AhmedMKAlzoubi/Digital-B-Card/datasheets/all_datasheets_combined.md

# Digital Business Card — All Datasheets (Combined)

*Single merged reference: system datasheets (MCU, display) + all BOM part datasheets.
Merged 2026-08-01 from `datasheets_combined.md` and `part_datasheets_combined.md`, with J2 (C295747) added as §15 of Part II.*

---

# PART I — SYSTEM DATASHEETS

# Datasheets — Combined Reference

_Compiled 2026-07-31 from 4 source PDFs. Full-text extraction; the Good Display module was OCR-processed as it is image-based, so minor OCR artifacts may be present._

## Contents

1. [ESP32-C3-MINI-1 Datasheet](#1-esp32-c3-mini-1-datasheet) — Espressif Systems — ESP32-C3-MINI-1 / MINI-1U Wi-Fi + Bluetooth LE MCU module
2. [ESP32-C3 Hardware Design Guidelines](#2-esp32-c3-hardware-design-guidelines) — Espressif Systems — ESP32-C3 series hardware design guidelines
3. [SSD1680 Datasheet](#3-ssd1680-datasheet) — Solomon Systech — SSD1680 active matrix EPD display driver / controller
4. [GDEM0266T71WT Datasheet](#4-gdem0266t71wt-datasheet) — Good Display — GDEM0266T71WT 2.66" e-paper display module (OCR-extracted)

---

# 1. ESP32-C3-MINI-1 Datasheet

> **Source file:** `esp32-c3-mini-1_datasheet_en.pdf`  
> Espressif Systems — ESP32-C3-MINI-1 / MINI-1U Wi-Fi + Bluetooth LE MCU module

<!-- Page 1 -->

ESP32-C3-MINI-1
ESP32-C3-MINI-1U
Datasheet Version 2.2
Small-sized 2.4 GHz Wi-Fi (802.11b/g/n) and Bluetooth® 5 module
Built around ESP32-C3 series of SoCs, RISC-V single-core microprocessor
Up to 8 MB flash in chip package
15 GPIOs
On-board PCB antenna or external antenna connector
ESP32-C3-MINI-1
ESP32-C3-MINI-1U
www.espressif.com

<!-- Page 2 -->

1
Module Overview
1
Module Overview
Note:
Check the link or the QR code to make sure that you use the latest version of this document:
https://www.espressif.com/documentation/esp32-c3-mini-1_datasheet_en.pdf
1.1
Features
CPU and On-Chip Memory
• ESP32-C3FH4, ESP32-C3FH4X,
ESP32-C3FH8X, or ESP32-C3FH4AZ
embedded, 32-bit RISC-V single-core
processor, up to 160 MHz
• 384 KB ROM
• 400 KB SRAM (16 KB for cache)
• 8 KB SRAM in RTC
• Up to 8 MB flash in chip package
Wi-Fi
• IEEE 802.11 b/g/n-compliant
• Center frequency range of operating channel:
2412 ~ 2484 MHz
• Supports 20 MHz, 40 MHz bandwidth in 2.4
GHz band
• 1T1R mode with data rate up to 150 Mbps
• Wi-Fi Multimedia (WMM)
• TX/RX A-MPDU, TX/RX A-MSDU
• Immediate Block ACK
• Fragmentation and defragmentation
• Transmit opportunity (TXOP)
• Automatic Beacon monitoring (hardware TSF)
• 4 × virtual Wi-Fi interfaces
• Simultaneous support for Infrastructure BSS in
Station mode, SoftAP mode, Station + SoftAP
mode, and promiscuous mode
Note that when the chip scans in Station mode,
the SoftAP channel will change along with the
Station channel
• 802.11mc FTM
Bluetooth®
• Bluetooth LE: Bluetooth 5, Bluetooth mesh
• Speed: 125 Kbps, 500 Kbps, 1 Mbps, 2 Mbps
• Advertising extensions
• Multiple advertisement sets
• Channel selection algorithm #2
• Internal co-existence mechanism between Wi-Fi
and Bluetooth to share the same antenna
Peripherals
• Up to 15 GPIOs
– 3 strapping GPIOs
• SPI, UART, I2C, I2S, remote control peripheral,
LED PWM controller, general DMA controller,
TWAI® controller (compatible with ISO 11898-1,
i.e. CAN Specification 2.0), USB Serial/JTAG
controller, temperature sensor, SAR ADC,
general-purpose timers, watchdog timers
Note:
* Please refer to ESP32-C3 Series Datasheet for
detailed information about the module peripher-
als.
Integrated Components on Module
• 40 MHz crystal oscillator
Espressif Systems
2
Submit Documentation Feedback
ESP32-C3-MINI-1 & MINI-1U Datasheet v2.2

<!-- Page 3 -->

1
Module Overview
Antenna Options
• ESP32-C3-MINI-1: On-board PCB antenna
• ESP32-C3-MINI-1U: External antenna via a
connector
Operating Conditions
• Operating voltage/Power supply: 3.0 ~ 3.6 V
• Operating ambient temperature:
– 85 °C version module: –40 ~ 85 °C
– 105 °C version module: –40 ~ 105 °C
Certification
• RF certification: See certificates
• Green certification: RoHS/REACH
Test
• HTOL/HTSL/uHAST/TCT/ESD/Latch-up
1.2
Series Comparison
ESP32-C3-MINI-1 and ESP32-C3-MINI-1U are two general-purpose Wi-Fi and Bluetooth LE modules. The rich
set of peripherals and a small size make the two modules an ideal choice for smart homes, industrial
automation, health care, consumer electronics, etc.
ESP32-C3-MINI-1 comes with a PCB antenna. ESP32-C3-MINI-1U comes with an external antenna connector.
A wide selection of module variants are available as shown in Table 1-1 and 1-2.
The series comparison for the two modules is as follows:
Table 1-1. ESP32-C3-MINI-1 (ANT) Series Comparison1
Ambient Temp.2
Embedded
Size3
Part Number5
Flash4
(°C)
Chip Revision6
(mm)
ESP32-C3-MINI-1-N4X
(Recommended)
4 MB (Quad SPI)
–40 ∼85
v1.1
13.2 × 16.6 × 2.4
ESP32-C3-MINI-1-H4X
(Recommended)
–40 ∼105
v1.1
ESP32-C3-MINI-1-H8X
8 MB (Quad SPI)
–40 ∼105
v1.1
ESP32-C3-MINI-1-N4 (NRND)
4 MB (Quad SPI)
–40 ∼85
v0.4
ESP32-C3-MINI-1-H4 (NRND)
–40 ∼105
v0.4
ESP32-C3-MINI-1-H4-AZ (NRND)
–40 ∼105
v0.4
1 This table shares the same notes presented in Table 1-2 below.
Espressif Systems
3
Submit Documentation Feedback
ESP32-C3-MINI-1 & MINI-1U Datasheet v2.2

<!-- Page 4 -->

1
Module Overview
Table 1-2. ESP32-C3-MINI-1U (CONN) Series Comparison
Ambient Temp.2
Embedded
Size3
Part Number5
Flash4, 7
(°C)
Chip Revision 6
(mm)
ESP32-C3-MINI-1U-N4X
(Recommended)
4 MB (Quad SPI)
–40 ∼85
v1.1
13.2 × 12.5 × 2.4
ESP32-C3-MINI-1U-H4X
(Recommended)
–40 ∼105
v1.1
ESP32-C3-MINI-1U-N4 (NRND)
–40 ∼85
v0.4
ESP32-C3-MINI-1U-H4 (NRND)
–40 ∼105
v0.4
2 Ambient temperature specifies the recommended temperature range of the environment immediately outside the
Espressif module.
3 For details, refer to Section 10.1 Module Dimensions.
4 The flash is integrated in the chip’s package. For specifications, refer to Section 6.5 Memory Specifications.
5 All modules can be pre-programmed with AWS IoT ExpressLink firmware. Modules with such firmware have suffix ”-A”
in their part numbers, e.g. ESP32-C3-MINI-1-N4-A. Since AWS IoT ExpressLink firmware enables flash encryption
and secure boot, joint download boot mode will be disabled, and it will no longer be possible to program firmware
through the UART or USB port into the modules.
6 All chip revisions have the same SRAM size, but chip revision v1.1 has around 10 KB more available space for users
than chip revision v0.4. Chip revision v1.1 depends on specific ESP-IDF versions, as detailed in Compatibility Advisory
for ESP32-C3 Chip Revision v1.1. For how to identify chip revisions, please refer to ESP32-C3 Series SoC Errata.
7 By default, the SPI flash on the module operates at a maximum clock frequency of 80 MHz and does not support
the auto suspend feature. If you have a requirement for a higher flash clock frequency of 120 MHz or if you need
the flash auto suspend feature, please contact us.
Both ESP32-C3-MINI-1 and ESP32-C3-MINI-1U has two operating ambient temperature options: –40 ∼85 °C
variants and –40 ∼105 °C variants. These modules can be embedded with the following chips:
• ESP32-C3FH4: chip revision v0.4, 4 MB flash
• ESP32-C3FH4X: chip revision v1.1, 4 MB flash
• ESP32-C3FH8X: chip reivision v1.1, 8 MB
ESP32-C3-MINI-1 has one more variant: ESP32-C3-MINI-1-H4-AZ embedded with the ESP32-C3FH4AZ chip.
For this chip, SPI0/SPI1 pins for flash connection are not bonded.
For more information about the differences between chips embedded, please refer to Section Chip Series
Comparison in ESP32-C3 Series Datasheet.
1.3
Applications
• Smart Home
• Industrial Automation
• Health Care
• Consumer Electronics
• Smart Agriculture
• POS Machines
• Service Robot
• Audio Devices
• Generic Low-power IoT Sensor Hubs
• Generic Low-power IoT Data Loggers
Espressif Systems
4
Submit Documentation Feedback
ESP32-C3-MINI-1 & MINI-1U Datasheet v2.2

<!-- Page 5 -->

Contents
Contents
1
Module Overview
2
1.1
Features
2
1.2
Series Comparison
3
1.3
Applications
4
2
Block Diagram
9
3
Pin Definitions
10
3.1
Pin Layout
10
3.2
Pin Description
10
4
Boot Configurations
12
4.1
Chip Boot Mode Control
13
4.2
ROM Messages Printing Control
14
4.3
Chip Power-up and Reset
14
5
Peripherals
16
5.1
Peripheral Overview
16
5.2
Peripheral Description
16
5.2.1
Connectivity Interface
16
5.2.1.1
UART Controller
16
5.2.1.2
SPI Controller
16
5.2.1.3
I2C Controller
17
5.2.1.4
I2S Controller
18
5.2.1.5
USB Serial/JTAG Controller
18
5.2.1.6
Two-wire Automotive Interface
18
5.2.1.7
LED PWM Controller
19
5.2.1.8
Remote Control Peripheral
19
5.2.2
Analog Signal Processing
19
5.2.2.1
SAR ADC
20
5.2.2.2
Temperature Sensor
20
6
Electrical Characteristics
21
6.1
Absolute Maximum Ratings
21
6.2
Recommended Operating Conditions
21
6.3
DC Characteristics (3.3 V, 25 °C)
21
6.4
Current Consumption Characteristics
22
6.4.1
Current Consumption in Active Mode
22
6.4.2
Current Consumption in Other Modes
23
6.5
Memory Specifications
23
7
RF Characteristics
25
7.1
Wi-Fi Radio
25
Espressif Systems
5
Submit Documentation Feedback
ESP32-C3-MINI-1 & MINI-1U Datasheet v2.2

<!-- Page 6 -->

Contents
7.1.1
Wi-Fi RF Transmitter (TX) Characteristics
25
7.1.2
Wi-Fi RF Receiver (RX) Characteristics
26
7.2
Bluetooth 5 (LE) Radio
27
7.2.1
Bluetooth LE RF Transmitter (TX) Characteristics
27
7.2.2
Bluetooth LE RF Receiver (RX) Characteristics
29
8
Module Schematics
32
9
Peripheral Schematics
34
10 Physical Dimensions
35
10.1
Module Dimensions
35
10.2
Dimensions of External Antenna Connector
36
11
PCB Layout Recommendations
38
11.1
PCB Land Pattern
38
11.2
Module Placement for PCB Design
39
12 Product Handling
40
12.1
Storage Conditions
40
12.2
Electrostatic Discharge (ESD)
40
12.3
Reflow Profile
40
12.4
Ultrasonic Vibration
41
Datasheet Versioning
42
Related Documentation and Resources
43
Revision History
45
Espressif Systems
6
Submit Documentation Feedback
ESP32-C3-MINI-1 & MINI-1U Datasheet v2.2

<!-- Page 7 -->

List of Tables
List of Tables
1-1
ESP32-C3-MINI-1 (ANT) Series Comparison1
3
1-2
ESP32-C3-MINI-1U (CONN) Series Comparison
4
3-1
Pin Definitions
11
4-1
Default Configuration of Strapping Pins
12
4-2
Description of Timing Parameters for the Strapping Pins
13
4-3
Chip Boot Mode Control
13
4-4
UART0 ROM Message Printing Control
14
4-5
USB Serial/JTAG ROM Message Printing Control
14
4-6 Description of Timing Parameters for Power-up and Reset
15
6-1
Absolute Maximum Ratings
21
6-2 Recommended Operating Conditions
21
6-3 DC Characteristics (3.3 V, 25 °C)
21
6-4 Current Consumption for Wi-Fi (2.4 GHz) in Active Mode
22
6-5 Current Consumption for Bluetooth LE in Active Mode
22
6-6 Current Consumption in Modem-sleep Mode
23
6-7
Current Consumption in Low-Power Modes
23
6-8 Flash Specifications
23
7-1
Wi-Fi RF Characteristics
25
7-2
TX Power with Spectral Mask and EVM Meeting 802.11 Standards
25
7-3
TX EVM Test1
25
7-4
RX Sensitivity
26
7-5
Maximum RX Level
27
7-6
RX Adjacent Channel Rejection
27
7-7
Bluetooth LE RF Characteristics
27
7-8
Bluetooth LE - Transmitter Characteristics - 1 Mbps
28
7-9
Bluetooth LE - Transmitter Characteristics - 2 Mbps
28
7-10 Bluetooth LE - Transmitter Characteristics - 125 Kbps
28
7-11
Bluetooth LE - Transmitter Characteristics - 500 Kbps
29
7-12 Bluetooth LE - Receiver Characteristics - 1 Mbps
29
7-13 Bluetooth LE - Receiver Characteristics - 2 Mbps
30
7-14 Bluetooth LE - Receiver Characteristics - 125 Kbps
30
7-15 Bluetooth LE - Receiver Characteristics - 500 Kbps
31
Espressif Systems
7
Submit Documentation Feedback
ESP32-C3-MINI-1 & MINI-1U Datasheet v2.2

<!-- Page 8 -->

List of Figures
List of Figures
2-1
ESP32-C3-MINI-1 Block Diagram
9
2-2 ESP32-C3-MINI-1U Block Diagram
9
3-1
Pin Layout (Top View)
10
4-1
Visualization of Timing Parameters for the Strapping Pins
13
4-2
Visualization of Timing Parameters for Power-up and Reset
15
8-1
ESP32-C3-MINI-1 Schematics
32
8-2
ESP32-C3-MINI-1U Schematics
33
9-1
Peripheral Schematics
34
10-1 ESP32-C3-MINI-1 Physical Dimensions
35
10-2 ESP32-C3-MINI-1U Physical Dimensions
35
10-3 Dimensions of External Antenna Connector
36
11-1
ESP32-C3-MINI-1 Recommended PCB Land Pattern
38
11-2 ESP32-C3-MINI-1U Recommended PCB Land Pattern
39
12-1 Reflow Profile
40
Espressif Systems
8
Submit Documentation Feedback
ESP32-C3-MINI-1 & MINI-1U Datasheet v2.2

<!-- Page 9 -->

2
Block Diagram
2
Block Diagram
SPI Flash
RF Matching
40 MHz
Crystal
3V3
ESP32-C3-MINI-1
EN
GPIOs
Antenna
ESP32-C3FH4
Figure 2-1. ESP32-C3-MINI-1 Block Diagram
SPI Flash
40 MHz
Crystal
3V3
ESP32-C3-MINI-1U
EN
GPIOs
ESP32-C3FH4
RF Matching
Antenna
Figure 2-2. ESP32-C3-MINI-1U Block Diagram
Note:
For the pin mapping between the chip and the in-package flash, please refer to ESP32-C3 Series Datasheet > Table
Pin Mapping Between Chip and In-package Flash.
Espressif Systems
9
Submit Documentation Feedback
ESP32-C3-MINI-1 & MINI-1U Datasheet v2.2

<!-- Page 10 -->

3
Pin Definitions
3
Pin Definitions
3.1
Pin Layout
The pin diagram below shows the approximate location of pins on the module. For the actual diagram drawn to
scale, please refer to Figure 10.1 Module Dimensions.
Pin 49
GND
GND
GND
GND
GND
GND
GND
GND
GND
Pin 1
Pin 2
Pin 3
Pin 4
Pin 6
Pin 5
Pin 7
Pin 8
Pin 9
Pin 10
Pin 11
Pin 53
GND
Pin 52
GND
Pin 12
Pin 13
Pin 14
Pin 15
Pin 16
Pin 17
Pin 18
Pin 19
Pin 20
Pin 21
Pin 22
Pin 23
Pin 24
Pin 25
Pin 51
GND
Pin 26
Pin 27
Pin 28
Pin 29
Pin 30
Pin 31
Pin 32
Pin 33
Pin 34
Pin 35
Pin 50
GND
Pin 36
Pin 37
Pin 38
Pin 39
Pin 40
Pin 41
Pin 42
Pin 43
Pin 44
Pin 45
Pin 46
Pin 47
Pin 48
GND
GND
3V3
NC
IO2
IO3
NC
EN
NC
NC
GND
IO0
IO1
GND
NC
IO10
NC
IO4
IO5
IO6
IO7
IO8
IO9
NC
NC
IO18
IO19
NC
NC
RXD0
TXD0
NC
NC
NC
NC
GND
GND
GND
GND
GND
GND
GND
GND
GND
GND
GND
GND
GND
Keepout Zone
A
Figure 3-1. Pin Layout (Top View)
Note A:
The zone marked with dotted lines is the antenna keepout zone. The pin diagram is applicable to ESP32-C3-MINI-1
and ESP32-C3-MINI-1U, but the latter has no antenna keepout zone.
To learn more about the keepout zone for module’s antenna on the base board, please refer to
ESP32-C3 Hardware Design Guidelines > Section General Principles of PCB Layout for Modules.
3.2
Pin Description
The module has 53 pins. See pin definitions in Table 3-1 Pin Definitions.
For peripheral pin configurations, please refer to Section 5.2 Peripheral Description.
Espressif Systems
10
Submit Documentation Feedback
ESP32-C3-MINI-1 & MINI-1U Datasheet v2.2

<!-- Page 11 -->

3
Pin Definitions
Table 3-1. Pin Definitions
Name
No.
Type1
Function
GND
1, 2, 11, 14,
36-53
P
Ground
3V3
3
P
Power supply
NC
4, 7, 9, 10,
15, 17, 24,
25, 28, 29,
32-35
—
NC
IO2
5
I/O/T
GPIO2, ADC1_CH2, FSPIQ
IO3
6
I/O/T
GPIO3, ADC1_CH3
EN
8
I
High: on, enables the chip.
Low: off, the chip powers off.
Note: Do not leave the EN pin floating.
IO0
12
I/O/T
GPIO0, ADC1_CH0, XTAL_32K_P
IO1
13
I/O/T
GPIO1, ADC1_CH1, XTAL_32K_N
IO10
16
I/O/T
GPIO10, FSPICS0
IO4
18
I/O/T
GPIO4, ADC1_CH4, FSPIHD, MTMS
IO5
19
I/O/T
GPIO5, ADC2_CH0, FSPIWP, MTDI
IO6
20
I/O/T
GPIO6, FSPICLK, MTCK
IO7
21
I/O/T
GPIO7, FSPID, MTDO
IO8
22
I/O/T
GPIO8
IO9
23
I/O/T
GPIO9
IO18
26
I/O/T
GPIO18, USB_D-
IO19
27
I/O/T
GPIO19, USB_D+
RXD0
30
I/O/T
GPIO20, U0RXD
TXD0
31
I/O/T
GPIO21, U0TXD
1 P: power supply; I: input; O: output; T: high impedance.
Espressif Systems
11
Submit Documentation Feedback
ESP32-C3-MINI-1 & MINI-1U Datasheet v2.2

<!-- Page 12 -->

4
Boot Configurations
4
Boot Configurations
Note:
The content below is excerpted from ESP32-C3 Series Datasheet > Chapter Boot Configurations. For the strapping
pin mapping between the chip and modules, please refer to Chapter 8 Module Schematics.
The chip allows for configuring the following boot parameters through strapping pins and eFuse parameters at
power-up or a hardware reset, without microcontroller interaction.
• Chip boot mode
– Strapping pins: GPIO2, GPIO8, and GPIO9
• ROM message printing
– Strapping pin: GPIO8
– eFuse parameters: EFUSE_UART_PRINT_CONTROL and EFUSE_USB_PRINT_CHANNEL
The default values of all the above eFuse parameters are 0, which means that they are not burnt. Given that
eFuse is one-time programmable, once programmed to 1, it can never be reverted to 0. For how to program
eFuse parameters, please refer to ESP32-C3 Technical Reference Manual > Chapter eFuse Controller.
The default values of the strapping pins, namely the logic levels, are determined by pins’ internal weak
pull-up/pull-down resistors at reset if the pins are not connected to any circuit, or connected to an external
high-impedance circuit.
Table 4-1. Default Configuration of Strapping Pins
Strapping Pin
Default Configuration
Bit Value
GPIO2
Floating
–
GPIO8
Floating
–
GPIO9
Weak pull-up
1
To change the bit values, the strapping pins should be connected to external pull-down/pull-up resistances. If
the ESP32-C3 is used as a device by a host MCU, the strapping pin voltage levels can also be controlled by
the host MCU.
All strapping pins have latches. At Chip Reset, the latches sample the bit values of their respective strapping
pins and store them until the chip is powered down or shut down. The states of latches cannot be changed in
any other way. It makes the strapping pin values available during the entire chip operation, and the pins are
freed up to be used as regular IO pins after reset. For details on Chip Reset, see
ESP32-C3 Technical Reference Manual > Chapter Reset and Clock.
The timing of signals connected to the strapping pins should adhere to the setup time and hold time
specifications in Table 4-2 and Figure 4-1.
Espressif Systems
12
Submit Documentation Feedback
ESP32-C3-MINI-1 & MINI-1U Datasheet v2.2

<!-- Page 13 -->

4
Boot Configurations
Table 4-2. Description of Timing Parameters for the Strapping Pins
Parameter
Description
Min (ms)
tSU
Setup time is the time reserved for the power rails to stabilize be-
fore the CHIP_EN pin is pulled high to activate the chip.
0
tH
Hold time is the time reserved for the chip to read the strapping
pin values after CHIP_EN is already high and before these pins
start operating as regular IO pins.
3
Strapping pin
VIH_nRST
VIH
tSU
tH
CHIP_EN
Figure 4-1. Visualization of Timing Parameters for the Strapping Pins
4.1
Chip Boot Mode Control
GPIO2, GPIO8, and GPIO9 control the boot mode after the reset is released. See Table 4-3 Chip Boot Mode
Control.
Table 4-3. Chip Boot Mode Control
Boot Mode
GPIO2 2
GPIO8
GPIO9
SPI boot mode
1
Any value
1
Joint download boot mode 3
1
1
0
1 Bold marks the default value and configuration.
2 GPIO2 actually does not determine SPI Boot and Joint Down-
load Boot mode, but it is recommended to pull this pin up due
to glitches.
3 Joint Download Boot mode supports the following download
methods:
• USB-Serial-JTAG Download Boot
• UART Download Boot
In SPI Boot mode, the ROM bootloader loads and executes the program from SPI flash to boot the
system.
Espressif Systems
13
Submit Documentation Feedback
ESP32-C3-MINI-1 & MINI-1U Datasheet v2.2

<!-- Page 14 -->

4
Boot Configurations
In Joint Download Boot mode, users can download binary files into flash using UART0 or USB interface. It is
also possible to download binary files into SRAM and execute it from SRAM.
In addition to SPI Boot and Joint Download Boot modes, ESP32-C3 also supports SPI Download Boot mode.
For details, please see ESP32-C3 Technical Reference Manual > Chapter Chip Boot Control.
4.2
ROM Messages Printing Control
During the boot process, the messages by the ROM code can be printed to:
• (Default) UART0 and USB Serial/JTAG controller
• UART0
• USB Serial/JTAG controller
EFUSE_UART_PRINT_CONTROL and GPIO8 control ROM messages printing to UART0 as shown in Table 4-4
UART0 ROM Message Printing Control.
Table 4-4. UART0 ROM Message Printing Control
UART0 ROM Code Printing
EFUSE_UART_PRINT_CONTROL
GPIO8
Enabled
0
Ignored
1
0
2
1
Disabled
1
1
2
0
3
Ignored
1 Bold marks the default value and configuration.
EFUSE_USB_PRINT_CHANNEL controls the printing to USB Serial/JTAG controller as shown in Table 4-5 USB
Serial/JTAG ROM Message Printing Control.
Table 4-5. USB Serial/JTAG ROM Message Printing Control
USB Serial/JTAG
ROM Code Printing
EFUSE_DIS_USB_SERIAL_JTAG 2
EFUSE_USB_PRINT_CHANNEL
Enabled
0
0
Disabled
0
1
1
Ignored
1 Bold marks the default value and configuration.
2 EFUSE_DIS_USB_SERIAL_JTAG controls whether to disable USB Serial/JTAG.
4.3
Chip Power-up and Reset
Once the power is supplied to the chip, its power rails need a short time to stabilize. After that, CHIP_EN – the
pin used for power-up and reset – is pulled high to activate the chip. For information on CHIP_EN as well as
power-up and reset timing, see Figure 4-2 and Table 4-6.
Espressif Systems
14
Submit Documentation Feedback
ESP32-C3-MINI-1 & MINI-1U Datasheet v2.2

<!-- Page 15 -->

4
Boot Configurations
VIL_nRST
tST BL
tRST
2.8 V
VDDA,
VDD3P3,
VDD3P3_RTC,
VDD3P3_CPU
CHIP_EN
Figure 4-2. Visualization of Timing Parameters for Power-up and Reset
Table 4-6. Description of Timing Parameters for Power-up and Reset
Parameter
Description
Min (µs)
tST BL
Time
reserved
for
the
power
rails
of
VDDA,
VDD3P3,
VDD3P3_RTC, and VDD3P3_CPU to stabilize before the CHIP_EN
pin is pulled high to activate the chip
50
tRST
Time reserved for CHIP_EN to stay below VIL_nRST to reset the
chip (see Table 6-3)
50
Espressif Systems
15
Submit Documentation Feedback
ESP32-C3-MINI-1 & MINI-1U Datasheet v2.2

<!-- Page 16 -->

5
Peripherals
5
Peripherals
5.1
Peripheral Overview
ESP32-C3FH4 integrates a rich set of peripherals including SPI, UART, I2C, I2S, remote control peripheral, LED
PWM controller, TWAI® controller, USB Serial/JTAG controller, temperature sensor, SAR ADC.
To learn more about on-chip components, please refer to ESP32-C3 Series Datasheet > Section Functional
Description.
Note:
The content below is sourced from ESP32-C3 Series Datasheet > Section Peripherals. Some information may not be
applicable to ESP32-C3-MINI-1 and ESP32-C3-MINI-1U as not all the IO signals are exposed on the module.
To learn more about peripheral signals, please refer to ESP32-C3 Technical Reference Manual > Section Peripheral
Signal List.
5.2
Peripheral Description
This section describes the chip’s peripheral capabilities, covering connectivity interfaces and on-chip sensors
that extend its functionality.
5.2.1
Connectivity Interface
This subsection describes the connectivity interfaces on the chip that enable communication and interaction
with external devices and networks.
5.2.1.1
UART Controller
ESP32-C3 has two UART interfaces, i.e. UART0 and UART1, which support IrDA and asynchronous
communication (RS232 and RS485) at a speed of up to 5 Mbps. The UART controller provides hardware flow
control (CTS and RTS signals) and software flow control (XON and XOFF). Both UART interfaces connect to
GDMA via UHCI0, and can be accessed by the GDMA controller or directly by the CPU.
For details, see ESP32-C3 Technical Reference Manual > Chapter UART Controller (UART, LP_UART).
Pin Assignment
For details, see ESP32-C3 Series Datasheet > Section Peripheral Pin Assignment.
5.2.1.2
SPI Controller
ESP32-C3 has the following SPI interfaces:
• SPI0 used by ESP32-C3’s GDMA controller and cache to access in-package or off-package flash
• SPI1 used by the CPU to access in-package or off-package flash
• SPI2 is a general purpose SPI controller with access to a DMA channel allocated by the GDMA controller
Espressif Systems
16
Submit Documentation Feedback
ESP32-C3-MINI-1 & MINI-1U Datasheet v2.2

<!-- Page 17 -->

5
Peripherals
Features of SPI0 and SPI1
• Supports Single SPI, Dual SPI, and Quad SPI, QPI modes
• Configurable clock frequency with a maximum of 120 MHz in Single Transfer Rate (STR) mode
• Data transmission is in bytes
Features of SPI2
• Supports operation as a master or slave
• Connects to a DMA channel allocated by the GDMA controller
• Supports Single SPI, Dual SPI, and Quad SPI, QPI
• Configurable clock polarity (CPOL) and phase (CPHA)
• Configurable clock frequency
• Data transmission is in bytes
• Configurable read and write data bit order: most-significant bit (MSB) first, or least-significant bit (LSB)
first
• As a master
– Supports 2-line full-duplex communication with clock frequency up to 80 MHz
– Supports 1-, 2-, 4-line half-duplex communication with clock frequency up to 80 MHz
– Provides six SPI_CS pins for connection with six independent SPI slaves
– Configurable CS setup time and hold time
• As a slave
– Supports 2-line full-duplex communication with clock frequency up to 60 MHz
– Supports 1-, 2-, 4-line half-duplex communication with clock frequency up to 60 MHz
For details, see ESP32-C3 Technical Reference Manual > Chapter SPI Controller (SPI).
Pin Assignment
For details, see ESP32-C3 Series Datasheet > Section Peripheral Pin Assignment.
5.2.1.3
I2C Controller
ESP32-C3 has an I2C bus interface which is used for I2C master mode or slave mode, depending on your
configuration. The I2C interface supports:
• Standard mode (100 Kbit/s)
• Fast mode (400 Kbit/s)
• Up to 800 Kbit/s (constrained by SCL and SDA pull-up strength)
• 7-bit and 10-bit addressing mode
• Double addressing mode
Espressif Systems
17
Submit Documentation Feedback
ESP32-C3-MINI-1 & MINI-1U Datasheet v2.2

<!-- Page 18 -->

5
Peripherals
• 7-bit broadcast address
For details, see ESP32-C3 Technical Reference Manual > Chapter I2C Controller (I2C).
Pin Assignment
For details, see ESP32-C3 Series Datasheet > Section Peripheral Pin Assignment.
5.2.1.4
I2S Controller
ESP32-C3 includes a standard I2S interface. This interface can operate as a master or a slave in full-duplex
mode or half-duplex mode, and can be configured for 8-bit, 16-bit, 24-bit, or 32-bit serial communication. BCK
clock frequency, from 10 kHz up to 40 MHz, is supported.
The I2S interface connects to the GDMA controller. The interface supports TDM PCM, TDM MSB alignment,
TDM standard, and PDM standard.
For details, see ESP32-C3 Technical Reference Manual > Chapter I2S Controller (I2S).
Pin Assignment
For details, see ESP32-C3 Series Datasheet > Section Peripheral Pin Assignment.
5.2.1.5
USB Serial/JTAG Controller
ESP32-C3 integrates a USB Serial/JTAG controller. This controller has the following features:
• CDC-ACM virtual serial port and JTAG adapter functionality
• USB 2.0 full speed compliant, capable of up to 12 Mbit/s transfer speed (Note that this controller does
not support the faster 480 Mbit/s high-speed transfer mode)
• Programming in-package/off-package flash
• CPU debugging with compact JTAG instructions
• A full-speed USB PHY integrated in the chip
For details, see ESP32-C3 Technical Reference Manual > Chapter USB Serial/JTAG Controller
(USB_SERIAL_JTAG).
Pin Assignment
For details, see ESP32-C3 Series Datasheet > Section Peripheral Pin Assignment.
5.2.1.6
Two-wire Automotive Interface
ESP32-C3 has a TWAI® controller with the following features:
• Compatible with ISO 11898-1 protocol (CAN Specification 2.0)
• Standard frame format (11-bit ID) and extended frame format (29-bit ID)
• Bit rates from 1 Kbit/s to 1 Mbit/s
• Multiple modes of operation: Normal, Listen Only, and Self-Test (no acknowledgment required)
Espressif Systems
18
Submit Documentation Feedback
ESP32-C3-MINI-1 & MINI-1U Datasheet v2.2

<!-- Page 19 -->

5
Peripherals
• 64-byte receive FIFO
• Acceptance filter (single and dual filter modes)
• Error detection and handling: error counters, configurable error interrupt threshold, error code capture,
arbitration lost capture
For details, see ESP32-C3 Technical Reference Manual > Chapter Two-wire Automotive Interface.
Pin Assignment
For details, see ESP32-C3 Series Datasheet > Section Peripheral Pin Assignment.
5.2.1.7
LED PWM Controller
The LED PWM controller can generate independent digital waveform on six channels. The LED PWM
controller:
• Can generate digital waveform with configurable periods and duty cycle. The resolution of duty cycle
can be up to 14 bits.
• Has multiple clock sources, including APB clock and external main crystal clock.
• Can operate when the CPU is in Light-sleep mode.
• Supports gradual increase or decrease of duty cycle, which is useful for the LED RGB color-gradient
generator.
For details, see ESP32-C3 Technical Reference Manual > Chapter LED PWM Controller.
Pin Assignment
For details, see ESP32-C3 Series Datasheet > Section Peripheral Pin Assignment.
5.2.1.8
Remote Control Peripheral
The Remote Control Peripheral (RMT) supports two channels of infrared remote transmission and two
channels of infrared remote reception. By controlling pulse waveform through software, it supports various
infrared and other single wire protocols. All four channels share a 192 × 32-bit memory block to store transmit
or receive waveform.
For more details, see ESP32-C3 Technical Reference Manual > Chapter Remote Control Peripheral (RMT).
Pin Assignment
For details, see ESP32-C3 Series Datasheet > Section Peripheral Pin Assignment.
5.2.2
Analog Signal Processing
This subsection describes components on the chip that sense and process real-world data.
Espressif Systems
19
Submit Documentation Feedback
ESP32-C3-MINI-1 & MINI-1U Datasheet v2.2

<!-- Page 20 -->

5
Peripherals
5.2.2.1
SAR ADC
ESP32-C3 integrates two 12-bit SAR ADCs.
• ADC1 supports measurements on 5 channels, and is factory-calibrated.
• ADC2 supports measurements on 1 channel, and is not factory-calibrated.
Note:
ADC2 of some chip revisions is not operable. For details, please refer to ESP32-C3 Series SoC Errata.
For more details, see ESP32-C3 Technical Reference Manual > Chapter On-Chip Sensors and Analog Signal
Processing.
Pin Assignment
For details, see ESP32-C3 Series Datasheet > Section Peripheral Pin Assignment.
5.2.2.2
Temperature Sensor
The temperature sensor generates a voltage that varies with temperature. The voltage is internally converted
via an ADC into a digital value.
The temperature sensor has a range of –40 °C to 125 °C. It is designed primarily to sense the temperature
changes inside the chip. The temperature value depends on factors like microcontroller clock frequency or
I/O load. Generally, the chip’s internal temperature is higher than the operating ambient temperature.
For more details, see ESP32-C3 Technical Reference Manual > Chapter On-Chip Sensors and Analog Signal
Processing.
Espressif Systems
20
Submit Documentation Feedback
ESP32-C3-MINI-1 & MINI-1U Datasheet v2.2

<!-- Page 21 -->

6
Electrical Characteristics
6
Electrical Characteristics
6.1
Absolute Maximum Ratings
Stresses above those listed in Table 6-1 Absolute Maximum Ratings may cause permanent damage to the
device. These are stress ratings only and functional operation of the device at these or any other conditions
beyond those indicated under Table 6-2 Recommended Operating Conditions is not implied. Exposure to
absolute-maximum-rated conditions for extended periods may affect device reliability.
Table 6-1. Absolute Maximum Ratings
Symbol
Parameter
Min
Max
Unit
VDD33
Power supply voltage
–0.3
3.6
V
6.2
Recommended Operating Conditions
Table 6-2. Recommended Operating Conditions
Symbol
Parameter
Min
Typ
Max
Unit
VDD33
Power supply voltage
3.0
3.3
3.6
V
IV DD
Current delivered by external power supply
0.5
—
—
A
TA
Operating ambient temperature
85 °C version
–40
—
85
°C
105 °C version
105
6.3
DC Characteristics (3.3 V, 25 °C)
Table 6-3. DC Characteristics (3.3 V, 25 °C)
Parameter
Description
Min
Typ
Max
Unit
CIN
Pin capacitance
—
2
—
pF
VIH
High-level input voltage
0.75 × VDD 1
—
VDD 1 + 0.3
V
VIL
Low-level input voltage
–0.3
—
0.25 × VDD 1
V
IIH
High-level input current
—
—
50
nA
IIL
Low-level input current
—
—
50
nA
VOH 2
High-level output voltage
0.8 × VDD 1
—
—
V
VOL 2
Low-level output voltage
—
—
0.1 × VDD 1
V
IOH
High-level source current (VDD 1 = 3.3 V,
VOH >= 2.64 V, PAD_DRIVER = 3)
—
40
—
mA
IOL
Low-level sink current (VDD 1 = 3.3 V, VOL =
0.495 V, PAD_DRIVER = 3)
—
28
—
mA
RP U
Internal weak pull-up resistor
—
45
—
kΩ
RP D
Internal weak pull-down resistor
—
45
—
kΩ
VIH_nRST
Chip reset release voltage (CHIP_EN voltage
is within the specified range)
0.75 × VDD 1
—
VDD 1 + 0.3
V
Cont’d on next page
Espressif Systems
21
Submit Documentation Feedback
ESP32-C3-MINI-1 & MINI-1U Datasheet v2.2

<!-- Page 22 -->

6
Electrical Characteristics
Table 6-3 – cont’d from previous page
Parameter
Description
Min
Typ
Max
Unit
VIL_nRST
Chip reset voltage (CHIP_EN voltage is within
the specified range)
–0.3
—
0.25 × VDD 1
V
1 VDD – voltage from a power pin of a respective power domain.
2 VOH and VOL are measured using high-impedance load.
6.4
Current Consumption Characteristics
6.4.1
Current Consumption in Active Mode
The current consumption measurements are taken with a 3.3 V supply at 25 °C ambient temperature.
TX current consumption is rated at a 100% duty cycle.
RX current consumption is rated when the peripherals are disabled and the CPU idle.
Table 6-4. Current Consumption for Wi-Fi (2.4 GHz) in Active Mode
Work mode
Description
Peak (mA)
Active (RF working)
TX
802.11b, 1 Mbps, @20.5 dBm
350
802.11g, 54 Mbps, @18 dBm
295
802.11n, HT20, MCS7, @17.5 dBm
290
802.11n, HT40, MCS7, @17 dBm
290
RX
802.11b/g/n, HT20
82
802.11n, HT40
84
Table 6-5. Current Consumption for Bluetooth LE in Active Mode
Work Mode
RF Condition
Description
Peak (mA)
Active (RF working)
TX
Bluetooth LE @ 20.0 dBm
340
Bluetooth LE @ 9.0 dBm
190
Bluetooth LE @ 0 dBm
170
Bluetooth LE @ –15.0 dBm
100
RX
Bluetooth LE
86
Espressif Systems
22
Submit Documentation Feedback
ESP32-C3-MINI-1 & MINI-1U Datasheet v2.2

<!-- Page 23 -->

6
Electrical Characteristics
Note:
The content below is excerpted from Section Power Consumption in Other Modes in ESP32-C3 Series Datasheet.
6.4.2
Current Consumption in Other Modes
Table 6-6. Current Consumption in Modem-sleep Mode
Typ
Mode
CPU Frequency
(MHz)
Description
All Peripherals Clocks
Disabled (mA)
All Peripherals Clocks
Enabled (mA) 1
Modem-sleep 2,3
160
CPU is running
23
28
CPU is idle
16
21
80
CPU is running
17
22
CPU is idle
13
18
1 In practice, the current consumption might be different depending on which peripherals are enabled.
2 In Modem-sleep mode, Wi-Fi is clock gated.
3 In Modem-sleep mode, the consumption might be higher when accessing flash. For a flash rated at
80 Mbit/s, in SPI 2-line mode the consumption is 10 mA.
Table 6-7. Current Consumption in Low-Power Modes
Mode
Description
Typ (µA)
Light-sleep
VDD_SPI and Wi-Fi are powered down, and all GPIOs are high-impedance
130
Deep-sleep
RTC timer + RTC memory
5
Power off
CHIP_EN is set to low level, the chip is powered off
1
6.5
Memory Specifications
The data below is sourced from the memory vendor datasheet. These values are guaranteed through design
and/or characterization but are not fully tested in production. Devices are shipped with the memory
erased.
Table 6-8. Flash Specifications
Parameter
Description
Min
Typ
Max
Unit
VCC
Power supply voltage (1.8 V)
1.65
1.80
2.00
V
Power supply voltage (3.3 V)
2.7
3.3
3.6
V
FC
Maximum clock frequency
80
—
—
MHz
—
Program/erase cycles
100,000
—
—
cycles
TRET
Data retention time
20
—
—
years
TP P
Page program time
—
0.8
5
ms
TSE
Sector erase time (4 KB)
—
70
500
ms
TBE1
Block erase time (32 KB)
—
0.2
2
s
TBE2
Block erase time (64 KB)
—
0.3
3
s
Cont’d on next page
Espressif Systems
23
Submit Documentation Feedback
ESP32-C3-MINI-1 & MINI-1U Datasheet v2.2

<!-- Page 24 -->

6
Electrical Characteristics
Table 6-8 – cont’d from previous page
Parameter
Description
Min
Typ
Max
Unit
TCE
Chip erase time (16 Mb)
—
7
20
s
Chip erase time (32 Mb)
—
20
60
s
Chip erase time (64 Mb)
—
25
100
s
Chip erase time (128 Mb)
—
60
200
s
Chip erase time (256 Mb)
—
70
300
s
Espressif Systems
24
Submit Documentation Feedback
ESP32-C3-MINI-1 & MINI-1U Datasheet v2.2

<!-- Page 25 -->

7
RF Characteristics
7
RF Characteristics
This section contains tables with RF characteristics of the Espressif product.
The RF data is measured at the antenna port, where RF cable is connected, including the front-end loss. The
external antennas used for the tests on the modules with external antenna connectors have an impedance of
50 Ω.
Devices should operate in the center frequency range allocated by regional regulatory authorities. The target
center frequency range and the target transmit power are configurable by software. See ESP RF Test Tool and
Test Guide for instructions.
Unless otherwise stated, the RF tests are conducted with a 3.3 V (±5%) supply at 25 ºC ambient temperature.
7.1
Wi-Fi Radio
Table 7-1. Wi-Fi RF Characteristics
Name
Description
Center frequency range of operating channel
2412 ~ 2484 MHz
Wi-Fi wireless standard
IEEE 802.11b/g/n
7.1.1
Wi-Fi RF Transmitter (TX) Characteristics
Table 7-2. TX Power with Spectral Mask and EVM Meeting 802.11 Standards
Min
Typ
Max
Rate
(dBm)
(dBm)
(dBm)
802.11b, 1 Mbps
—
20.5
—
802.11b, 11 Mbps
—
20.5
—
802.11g, 6 Mbps
—
20.0
—
802.11g, 54 Mbps
—
18.0
—
802.11n, HT20, MCS0
—
19.0
—
802.11n, HT20, MCS7
—
17.5
—
802.11n, HT40, MCS0
—
18.5
—
802.11n, HT40, MCS7
—
17.0
—
Table 7-3. TX EVM Test1
Min
Typ
Limit
Rate
(dB)
(dB)
(dB)
802.11b, 1 Mbps, @20.5 dBm
—
–24.5
–10
802.11b, 11 Mbps, @20.5 dBm
—
–25.0
–10
802.11g, 6 Mbps, @20 dBm
—
–23.0
–5
802.11g, 54 Mbps, @18 dBm
—
–28.0
–25
Cont’d on next page
Espressif Systems
25
Submit Documentation Feedback
ESP32-C3-MINI-1 & MINI-1U Datasheet v2.2

<!-- Page 26 -->

7
RF Characteristics
Table 7-3 – cont’d from previous page
Min
Typ
Limit
Rate
(dB)
(dB)
(dB)
802.11n, HT20, MCS0, @19 dBm
—
–23.5
–5
802.11n, HT20, MCS7, @17.5 dBm
—
–30.5
–27
802.11n, HT40, MCS0, @18.5 dBm
—
–26.5
–5
802.11n, HT40, MCS7, @17 dBm
—
–30.5
–27
1 EVM is measured at the corresponding typical TX power provided
in Table 7-2 TX Power with Spectral Mask and EVM Meeting 802.11
Standards above.
7.1.2
Wi-Fi RF Receiver (RX) Characteristics
For RX tests, the PER (packet error rate) limit is 8% for 802.11b, and 10% for 802.11g/n.
Table 7-4. RX Sensitivity
Min
Typ
Max
Rate
(dBm)
(dBm)
(dBm)
802.11b, 1 Mbps
—
–98.0
—
802.11b, 2 Mbps
—
–96.0
—
802.11b, 5.5 Mbps
—
–93.0
—
802.11b, 11 Mbps
—
–88.6
—
802.11g, 6 Mbps
—
–92.8
—
802.11g, 9 Mbps
—
–91.8
—
802.11g, 12 Mbps
—
–90.8
—
802.11g, 18 Mbps
—
–88.4
—
802.11g, 24 Mbps
—
–85.4
—
802.11g, 36 Mbps
—
–82.0
—
802.11g, 48 Mbps
—
–77.8
—
802.11g, 54 Mbps
—
–76.2
—
802.11n, HT20, MCS0
—
–92.6
—
802.11n, HT20, MCS1
—
–90.6
—
802.11n, HT20, MCS2
—
–88.0
—
802.11n, HT20, MCS3
—
–84.8
—
802.11n, HT20, MCS4
—
–81.6
—
802.11n, HT20, MCS5
—
–77.4
—
802.11n, HT20, MCS6
—
–75.6
—
802.11n, HT20, MCS7
—
–74.4
—
802.11n, HT40, MCS0
—
–90.0
—
802.11n, HT40, MCS1
—
–87.6
—
802.11n, HT40, MCS2
—
–84.8
—
802.11n, HT40, MCS3
—
–81.8
—
802.11n, HT40, MCS4
—
–78.4
—
802.11n, HT40, MCS5
—
–74.2
—
Cont’d on next page
Espressif Systems
26
Submit Documentation Feedback
ESP32-C3-MINI-1 & MINI-1U Datasheet v2.2

<!-- Page 27 -->

7
RF Characteristics
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
GPIO is already configured. It is recommended to use the default configuration. Please refer to
ESP-AT User Guide for ESP32-C3 > Section Hardware Connection.
Espressif Systems
34
Submit Documentation Feedback
ESP32-C3-MINI-1 & MINI-1U Datasheet v2.2

<!-- Page 35 -->

10
Physical Dimensions
10
Physical Dimensions
10.1
Module Dimensions
5.4
16.6±0.15
0.8
13.2±0.15
Top view
Side view
Bottom view
2.4±0.15
11.2
0.6
1.45
1.45
8.4
9.2
10
11.2
12.6
6.8
7.6
8.4
9
10.6
0.62
0.62
11.95
9.95
0.6
5.4
9.2
11
Ø0.5
Unit: mm
Figure 10-1. ESP32-C3-MINI-1 Physical Dimensions
5.4
12.5±0.15
0.8
13.2±0.15
Top view
Side view
Bottom view
0.6
1.45
1.45
8.4
9.2
10
11.2
12.6
6.8
7.6
8.4
9
10.6
12.25
0.6
5.4
9.2
11
Unit: mm
1.55
1.7
8.7
0.47
0.48
9.18
11.55
2.4±0.15
0.85
5.6
Figure 10-2. ESP32-C3-MINI-1U Physical Dimensions
Note:
For information about tape, reel, and product marking, please refer to ESP32-C3 Module Packaging Information.
Espressif Systems
35
Submit Documentation Feedback
ESP32-C3-MINI-1 & MINI-1U Datasheet v2.2

<!-- Page 36 -->

10
Physical Dimensions
10.2
Dimensions of External Antenna Connector
ESP32-C3-MINI-1U uses the third generation external antenna connector as shown in Figure 10-3 Dimensions
of External Antenna Connector. This connector is compatible with the following connectors:
• W.FL Series connector from Hirose
• MHF III connector from I-PEX
• AMC connector from Amphenol
SECTION: A-A
SCALE: 1:1
A
1.7
1.7
0.85
2.05±0.10
1.40
A
0.10
0.57
INSULATION RESISTANCE: 500MOHM Min.
DIELECTRIC WITHSTANDING VOLTAGE: 200V AC FOR 1MINUTE;
CONTACT MATERIAL: COPPER ALLOY, GOLD PLATED ALL OVER;
PERFORMANCE:
CONTACT RESISTANCE: 20mOHM Max.
HOUSING MATERIAL: THERMOPLASTIC, WHITE, UL 94V-0;
SHELL MATERIAL: COPPER ALLOY, GOLD PLATED ALL OVER;
CONTACT
GROUND CONTACT
2.00±0.10
Unit: mm
Tolerance: +/-0.1 mm
HOUSING
CONTACT
SHELL
Figure 10-3. Dimensions of External Antenna Connector
The external antenna used for ESP32-C3-MINI-1U during certification testing is the third generation monopole
antenna, with material code TFPD08H10060011.
The module does not include an external antenna upon shipment. If needed, select a suitable external
Espressif Systems
36
Submit Documentation Feedback
ESP32-C3-MINI-1 & MINI-1U Datasheet v2.2

<!-- Page 37 -->

10
Physical Dimensions
antenna based on the product’s usage environment and performance requirements.
It is recommended to select an antenna that meets the following requirements:
• 2.4 GHz band
• 50 Ωimpedance
• The maximum gain does not exceed 2.33 dBi, the gain of the antenna used for certification
• The connector matches the specifications shown in Figure 10-3 Dimensions of External Antenna
Connector
Note:
If you use an external antenna of a different type or gain, additional testing, such as EMC, may be required beyond the
existing antenna test reports for Espressif modules. Specific requirements depend on the certification type.
Espressif Systems
37
Submit Documentation Feedback
ESP32-C3-MINI-1 & MINI-1U Datasheet v2.2

<!-- Page 38 -->

11
PCB Layout Recommendations
11
PCB Layout Recommendations
11.1
PCB Land Pattern
This section provides the following resources for your reference:
• Figures for recommended PCB land patterns with all the dimensions needed for PCB design. See Figure
11-1 ESP32-C3-MINI-1 Recommended PCB Land Pattern and Figure 11-2 ESP32-C3-MINI-1U
Recommended PCB Land Pattern.
• Source files of recommended PCB land patterns to measure dimensions not covered in Figure 11-1 and
Figure 11-2. You can view the source files for ESP32-C3-MINI-1 and ESP32-C3-MINI-1U with Autodesk
Viewer.
• 3D models of ESP32-C3-MINI-1 and ESP32-C3-MINI-1U. Please make sure that you download the 3D
model file in .STEP format. Beware that some browsers might add .txt.
1.6
Antenna Area
Pin 1
11.2
0.6
9.9
5.4
11.9
1.6
13.2
16.6
1.45
5.4
1.45
0.6
11.8
9.8
Unit: mm
Pad
48 x 0.4
48 x 0.8
4 x 0.7
4 x 0.7
0.8
Via for thermal pad
Figure 11-1. ESP32-C3-MINI-1 Recommended PCB Land Pattern
Espressif Systems
38
Submit Documentation Feedback
ESP32-C3-MINI-1 & MINI-1U Datasheet v2.2

<!-- Page 39 -->

11
PCB Layout Recommendations
1.6
Pin 1
12.5
0.6
9.9
5.4
11.9
1.6
13.2
1.45
5.4
1.45
0.6
11.8
9.8
48 x 0.4
48 x 0.8
4 x 0.7
4 x 0.7
0.8
5.6
Unit: mm
Pad
Via for thermal pad
Figure 11-2. ESP32-C3-MINI-1U Recommended PCB Land Pattern
11.2
Module Placement for PCB Design
If module-on-board design is adopted, attention should be paid while positioning the module on the base
board. The interference of the base board on the module’s antenna performance should be minimized.
For details about module placement for PCB design, please refer to ESP32-C3 Hardware Design Guidelines >
Section General Principles of PCB Layout for Modules.
Espressif Systems
39
Submit Documentation Feedback
ESP32-C3-MINI-1 & MINI-1U Datasheet v2.2

<!-- Page 40 -->

12
Product Handling
12
Product Handling
12.1
Storage Conditions
The products sealed in moisture barrier bags (MBB) should be stored in a non-condensing atmospheric
environment of < 40 °C and 90%RH. The module is rated at the moisture sensitivity level (MSL) of 3.
After unpacking, the module must be soldered within 168 hours with the factory conditions 25±5 °C and
60%RH. If the above conditions are not met, the module needs to be baked.
12.2
Electrostatic Discharge (ESD)
• Human body model (HBM): ±2000 V
• Charged-device model (CDM): ±500 V
12.3
Reflow Profile
Solder the module in a single reflow.
50
100
0
150
200
250
200
100
50
150
250

Time (s)
217
25
Preheating
150 – 200 °C
60 – 120 s
Ramp-up
25 – 150 °C
60 – 90 s
1 – 3 °C/s
Soldering
＞ 217 °C
60 – 90 s
Peak temperature: 235 – 250 °C
Peak time: 30 – 70 s
Soldering time: ＞ 30 s
Solder: Sn-Ag-Cu (SAC305) lead-free solder
Temperature (°C)
180
230
Cooling
＜ 180 °C
–5 ~ –1 °C/s
Figure 12-1. Reflow Profile
Espressif Systems
40
Submit Documentation Feedback
ESP32-C3-MINI-1 & MINI-1U Datasheet v2.2

<!-- Page 41 -->

12
Product Handling
12.4
Ultrasonic Vibration
Avoid exposing Espressif modules to vibration from ultrasonic equipment, such as ultrasonic welders or
ultrasonic cleaners. This vibration may induce resonance in the in-module crystal and lead to its malfunction or
even failure. As a consequence, the module may stop working or its performance may deteriorate.
Espressif Systems
41
Submit Documentation Feedback
ESP32-C3-MINI-1 & MINI-1U Datasheet v2.2

<!-- Page 42 -->

Datasheet Versioning
Datasheet Versioning
Datasheet
Version
Status
Watermark
Definition
v0.1 ~ v0.5
(excluding v0.5)
Draft
Confidential
This datasheet is under development for products
in the design stage. Specifications may change
without prior notice.
v0.5 ~ v1.0
(excluding v1.0)
Preliminary
release
Preliminary
This datasheet is actively updated for products in
the verification stage. Specifications may change
before mass production, and the changes will be
documentation in the datasheet’s Revision History.
v1.0 and higher
Official release
—
This datasheet is publicly released for products in
mass production. Specifications are finalized, and
major changes will be communicated via Product
Change Notifications (PCN).
Any version
—
Not
Recommended
for New Design
(NRND)1
This datasheet is updated less frequently for
products not recommended for new designs.
Any version
—
End of Life
(EOL)2
This datasheet is no longer mtained for products
that have reached end of life.
1 Watermark will be added to the datasheet title page only when all the product variants covered by this
datasheet are not recommended for new designs.
2 Watermark will be added to the datasheet title page only when all the product variants covered by this
datasheet have reached end of life.
Espressif Systems
42
Submit Documentation Feedback
ESP32-C3-MINI-1 & MINI-1U Datasheet v2.2

<!-- Page 43 -->

Related Documentation and Resources
Related Documentation and Resources
Related Documentation
• ESP32-C3 Series Datasheet- Specifications of the ESP32-C3 hardware.
• ESP32-C3 Technical Reference Manual – Detailed information on how to use the ESP32-C3 memory and periph-
erals.
• ESP32-C3 Hardware Design Guidelines – Guidelines on how to integrate the ESP32-C3 into your hardware prod-
uct.
• ESP32-C3 Series SoC Errata – Descriptions of known errors in ESP32-C3 series of SoCs.
• Certificates
https://espressif.com/en/support/documents/certificates
• ESP32-C3 Product/Process Change Notifications (PCN)
https://espressif.com/en/support/documents/pcns?keys=ESP32-C3
• ESP32-C3 Advisories – Information on security, bugs, compatibility, component reliability.
https://espressif.com/en/support/documents/advisories?keys=ESP32-C3
• Documentation Updates and Update Notification Subscription
https://espressif.com/en/support/download/documents
Developer Zone
• ESP-IDF Programming Guide for ESP32-C3 – Extensive documentation for the ESP-IDF development framework.
• ESP-IDF and other development frameworks on GitHub.
https://github.com/espressif
• ESP32 BBS Forum – Engineer-to-Engineer (E2E) Community for Espressif products where you can post questions,
share knowledge, explore ideas, and help solve problems with fellow engineers.
https://esp32.com/
• ESP-FAQ – A summary document of frequently asked questions released by Espressif.
https://espressif.com/projects/esp-faq/en/latest/index.html
• The ESP Journal – Best Practices, Articles, and Notes from Espressif folks.
https://blog.espressif.com/
• See the tabs SDKs and Demos, Apps, Tools, AT Firmware.
https://espressif.com/en/support/download/sdks-demos
Products
• ESP32-C3 Series SoCs – Browse through all ESP32-C3 SoCs.
https://espressif.com/en/products/socs?id=ESP32-C3
• ESP32-C3 Series Modules – Browse through all ESP32-C3-based modules.
https://espressif.com/en/products/modules?id=ESP32-C3
• ESP32-C3 Series DevKits – Browse through all ESP32-C3-based devkits.
https://espressif.com/en/products/devkits?id=ESP32-C3
• ESP Product Selector – Find an Espressif hardware product suitable for your needs by comparing or applying filters.
https://products.espressif.com/#/product-selector?language=en
Espressif Systems
43
Submit Documentation Feedback
ESP32-C3-MINI-1 & MINI-1U Datasheet v2.2

<!-- Page 44 -->

Related Documentation and Resources
Contact Us
• See the tabs Sales Questions, Technical Enquiries, Circuit Schematic & PCB Design Review, Get Samples
(Online stores), Become Our Supplier, Comments & Suggestions.
https://espressif.com/en/contact-us/sales-questions
Espressif Systems
44
Submit Documentation Feedback
ESP32-C3-MINI-1 & MINI-1U Datasheet v2.2

<!-- Page 45 -->

Revision History
Revision History
Date
Version
Release notes
2026-05-06
v2.2
• Added ESP32-C3-MINI-1-H8X
• Table 1-1 ESP32-C3-MINI-1 (ANT) Series Comparison1 and Table 1-
2 ESP32-C3-MINI-1U (CONN) Series Comparison: Updated ”Ordering
Code” to ”Part Number”
2025-07-14
v2.1
• Added Section 4.3 Chip Power-up and Reset
• Added Section 6.5 Memory Specifications
• Section 9 Peripheral Schematics: Added a note about AT communication
using UART0
• Section 10.2 Dimensions of External Antenna Connector: Added the ex-
ternal antenna information for certification
• Added Datasheet Versioning
2025-04-14
v2.0
According to updates in Compatibility Advisory for ESP32-C3 Chip Revision v1.1,
updated SRAM space in note 6 for Table ESP32-C3-MINI-1U (CONN) Series
Comparison
2025-01-24
v1.9
Updated chip in ESP32-C3-MINI-1-N4 and ESP32-C3-MINI-1U-N4 from ESP32-
C3FN4 to ESP32-C3FH4
2024-11-20
v1.8
• Table 1-1 ESP32-C3-MINI-1 (ANT) Series Comparison1 and 1-2 ESP32-C3-
MINI-1U (CONN) Series Comparison:
– Added the ESP32-C3-MINI-1-N4X, ESP32-C3-MINI-1U-N4X, and
ESP32-C3-MINI-1U-H4X variants
– Marked the ESP32-C3-MINI-1U-N4 and ESP32-C3-MINI-1U-H4 vari-
ants as Not Recommended for New Designs (NRND)
• Added Table 6-5 Current Consumption for Bluetooth LE in Active Mode
2024-09-19
v1.7
• Table 1-2 ESP32-C3-MINI-1U (CONN) Series Comparison: Updated flash
program/erase cycles, data retention time (note 4) and maximum clock
frequency (note 7)
• Improved the wording and structure of following sections:
– Updated Section ”Strapping Pins” and renamed to 4 Boot Configu-
rations
– Added Chapter 5 Peripherals
– Updated Table ”Wi-Fi RF Standards” and renamed to ”Wi-Fi RF Char-
acteristics”
– Added Section 11.2 Module Placement for PCB Design
– Optimized Figure 12-1 Reflow Profile
Cont’d on next page
Espressif Systems
45
Submit Documentation Feedback
ESP32-C3-MINI-1 & MINI-1U Datasheet v2.2

<!-- Page 46 -->

Revision History
Cont’d from previous page
Date
Version
Release notes
2024-07-29
v1.6
Added Compatibility Advisory for ESP32-C3 Chip Revision v1.1 to the notes of
Table ESP32-C3-MINI-1U (CONN) Series Comparison
2024-06-05
v1.5
• Added new variant ESP32-C3-MINI-1-H4X
• Marked the ESP32-C3-MINI-1-N4, ESP32-C3-MINI-1-H4, and ESP32-C3-
MINI-1-H4-AZ variants as Not Recommended for New Designs (NRND)
2024-05-15
v1.4
• Updated note 5 of Table ESP32-C3-MINI-1 (ANT) Series Comparison1 and
Table ESP32-C3-MINI-1U (CONN) Series Comparison
• Updated the formatting of Section 4 Boot Configurations
• Updated the maximum value of ”RF power control range” to 20 dBm in
Table Bluetooth LE RF Characteristics
• Updated the note about solder paste in Section 9 Peripheral Schematics
• Updated the markings of dimensions and thermal pad vias in Section 11.1
PCB Land Pattern
2022-11-08
v1.3
• Added a new variant ESP32-C3-MINI-1-H4-AZ
• Changed Table Ordering Information to Table ESP32-C3-MINI-1 (ANT) Se-
ries Comparison1 and Table ESP32-C3-MINI-1U (CONN) Series Compari-
son
• Updated test condition descriptions and data in Section 6.4 Current Con-
sumption Characteristics
• Updated ”RF power control range” in Table Bluetooth LE RF Characteris-
tics
• Added descriptions in Section 11.1 PCB Land Pattern
2022-06-30
v1.2
Added Section 12.4 Ultrasonic Vibration
2022-05-16
v1.1
• Added a note under Table Ordering Information
• Updated Chapter 8 Module Schematics
2021-06-21
v1.0
• Updated module description on the title page
• Deleted Section ”About This Document”
• Restructured Section 1.1 Features
• Added ordering code in Table Ordering Information
• Added descriptions in Section 10.2 Dimensions of External Antenna Con-
nector
• Updated Section ”Learning Resources” and renamed to Related Docu-
mentation and Resources
• Replaced ”chip family” with ”chip series” following Espressif’s taxonomy
2021-04-16
v0.7
Added information about ESP32-C3-MINI-1U module
Cont’d on next page
Espressif Systems
46
Submit Documentation Feedback
ESP32-C3-MINI-1 & MINI-1U Datasheet v2.2

<!-- Page 47 -->

Revision History
Cont’d from previous page
Date
Version
Release notes
2021-02-22
v0.6
Updated the value of C7 to 0.1 µF in Chapter 8 Module Schematics
2021-02-05
v0.5
Preliminary release
Espressif Systems
47
Submit Documentation Feedback
ESP32-C3-MINI-1 & MINI-1U Datasheet v2.2

<!-- Page 48 -->

Disclaimer and Copyright Notice
Information in this document, including URL references, is subject to change without notice.
ALL THIRD PARTY’S INFORMATION IN THIS DOCUMENT IS PROVIDED AS IS WITH NO WARRANTIES TO ITS AUTHENTICITY AND
ACCURACY.
NO WARRANTY IS PROVIDED TO THIS DOCUMENT FOR ITS MERCHANTABILITY, NON-INFRINGEMENT, FITNESS FOR ANY PARTICULAR
PURPOSE, NOR DOES ANY WARRANTY OTHERWISE ARISING OUT OF ANY PROPOSAL, SPECIFICATION OR SAMPLE.
All liability, including liability for infringement of any proprietary rights, relating to use of information in this document is disclaimed. No
licenses express or implied, by estoppel or otherwise, to any intellectual property rights are granted herein.
The Wi-Fi Alliance Member logo is a trademark of the Wi-Fi Alliance. The Bluetooth logo is a registered trademark of Bluetooth SIG.
All trade names, trademarks and registered trademarks mentioned in this document are property of their respective owners, and are
hereby acknowledged.
Copyright © 2026 Espressif Systems (Shanghai) Co., Ltd. All rights reserved.
www.espressif.com

---

# 2. ESP32-C3 Hardware Design Guidelines

> **Source file:** `esp-hardware-design-guidelines-en-master-esp32c3.pdf`  
> Espressif Systems — ESP32-C3 series hardware design guidelines

<!-- Page 1 -->

ESP32-C3
Hardware Design Guidelines
Release master
Espressif Systems
Jul 06, 2026

<!-- Page 2 -->

Table of contents
Table of contents
i
1
Latest Version of This Document
3
1.1
About This Document
. . . . . . . . . . . . . . . . . . . . . . . . . . . . . . . . . . . . . . . .
3
1.1.1
Introduction . . . . . . . . . . . . . . . . . . . . . . . . . . . . . . . . . . . . . . . . .
3
1.1.2
Latest Version of This Document . . . . . . . . . . . . . . . . . . . . . . . . . . . . . .
3
1.2
Product Overview . . . . . . . . . . . . . . . . . . . . . . . . . . . . . . . . . . . . . . . . . . .
3
1.3
Schematic Checklist
. . . . . . . . . . . . . . . . . . . . . . . . . . . . . . . . . . . . . . . . .
4
1.3.1
Overview
. . . . . . . . . . . . . . . . . . . . . . . . . . . . . . . . . . . . . . . . . .
4
1.3.2
Power Supply . . . . . . . . . . . . . . . . . . . . . . . . . . . . . . . . . . . . . . . .
5
1.3.3
Chip Power-up and Reset Timing . . . . . . . . . . . . . . . . . . . . . . . . . . . . . .
6
1.3.4
Flash . . . . . . . . . . . . . . . . . . . . . . . . . . . . . . . . . . . . . . . . . . . . .
7
1.3.5
Clock Source
. . . . . . . . . . . . . . . . . . . . . . . . . . . . . . . . . . . . . . . .
7
1.3.6
RF . . . . . . . . . . . . . . . . . . . . . . . . . . . . . . . . . . . . . . . . . . . . . .
9
1.3.7
UART . . . . . . . . . . . . . . . . . . . . . . . . . . . . . . . . . . . . . . . . . . . .
11
1.3.8
SPI
. . . . . . . . . . . . . . . . . . . . . . . . . . . . . . . . . . . . . . . . . . . . .
11
1.3.9
Strapping Pins . . . . . . . . . . . . . . . . . . . . . . . . . . . . . . . . . . . . . . . .
11
1.3.10
GPIO
. . . . . . . . . . . . . . . . . . . . . . . . . . . . . . . . . . . . . . . . . . . .
13
1.3.11
ADC . . . . . . . . . . . . . . . . . . . . . . . . . . . . . . . . . . . . . . . . . . . . .
14
1.3.12
USB . . . . . . . . . . . . . . . . . . . . . . . . . . . . . . . . . . . . . . . . . . . . .
14
1.4
PCB Layout Design . . . . . . . . . . . . . . . . . . . . . . . . . . . . . . . . . . . . . . . . . .
15
1.4.1
General Principles of PCB Layout for the Chip . . . . . . . . . . . . . . . . . . . . . . .
15
1.4.2
Power Supply . . . . . . . . . . . . . . . . . . . . . . . . . . . . . . . . . . . . . . . .
15
1.4.3
Crystal . . . . . . . . . . . . . . . . . . . . . . . . . . . . . . . . . . . . . . . . . . . .
17
1.4.4
RF . . . . . . . . . . . . . . . . . . . . . . . . . . . . . . . . . . . . . . . . . . . . . .
18
1.4.5
Flash . . . . . . . . . . . . . . . . . . . . . . . . . . . . . . . . . . . . . . . . . . . . .
19
1.4.6
UART . . . . . . . . . . . . . . . . . . . . . . . . . . . . . . . . . . . . . . . . . . . .
20
1.4.7
General Principles of PCB Layout for Modules (Positioning a Module on a Base Board)
.
21
1.4.8
USB . . . . . . . . . . . . . . . . . . . . . . . . . . . . . . . . . . . . . . . . . . . . .
22
1.4.9
Typical Layout Problems and Solutions . . . . . . . . . . . . . . . . . . . . . . . . . . .
22
1.5
Download Guidelines . . . . . . . . . . . . . . . . . . . . . . . . . . . . . . . . . . . . . . . . .
23
1.6
Related Documentation and Resources . . . . . . . . . . . . . . . . . . . . . . . . . . . . . . . .
24
1.6.1
ESP32-C3 Modules . . . . . . . . . . . . . . . . . . . . . . . . . . . . . . . . . . . . .
24
1.6.2
ESP32-C3 Development Boards
. . . . . . . . . . . . . . . . . . . . . . . . . . . . . .
25
1.6.3
Other Related Documentation and Resources . . . . . . . . . . . . . . . . . . . . . . . .
25
1.7
Glossary
. . . . . . . . . . . . . . . . . . . . . . . . . . . . . . . . . . . . . . . . . . . . . . .
25
1.8
Revision History
. . . . . . . . . . . . . . . . . . . . . . . . . . . . . . . . . . . . . . . . . . .
25
1.9
Disclaimer and Copyright Notice . . . . . . . . . . . . . . . . . . . . . . . . . . . . . . . . . . .
26
i

<!-- Page 3 -->

ii

<!-- Page 4 -->

Table of contents
This document provides guidelines for the ESP32-C3 SoC.
Schematic Checklist
PCB Layout Design
Download Guidelines
Resources
Espressif Systems
1
Submit Document Feedback
Release master

<!-- Page 5 -->

Table of contents
Espressif Systems
2
Submit Document Feedback
Release master

<!-- Page 6 -->

Chapter 1
Latest Version of This Document
Check the link to make sure that you use the latest version of this document: https://docs.espressif.com/projects/
esp-hardware-design-guidelines/en/latest/esp32c3/index.html
1.1
About This Document
1.1.1
Introduction
The hardware design guidelines advise on how to integrate ESP32-C3 into a product. These guidelines will help to
achieve optimal performance of your product, ensuring technical accuracy and adherence to Espressif’s standards.
The guidelines are intended for hardware and application engineers.
The document assumes that you possess a certain level of familiarity with the ESP32-C3 SoC. In case you lack prior
knowledge, we recommend utilizing this document in conjunction with the ESP32-C3 Series Datasheet.
1.1.2
Latest Version of This Document
Check the link to make sure that you use the latest version of this document: https://docs.espressif.com/projects/
esp-hardware-design-guidelines/en/latest/esp32c3/index.html
1.2
Product Overview
ESP32-C3 is a system on a chip that integrates the following features:
• Wi-Fi (2.4 GHz band)
• Bluetooth® 5 (LE)
• High performance 32-bit RISC-V single-core processor
• Multiple peripherals
• Built-in security hardware
Powered by 40 nm technology, ESP32-C3 provides a robust, highly-integrated platform, which helps meet the con-
tinuous demands for efficient power usage, compact design, security, high performance, and reliability. Typical
application scenarios for ESP32-C3 include:
• Smart Home
3

<!-- Page 7 -->

Chapter 1. Latest Version of This Document
• Industrial Automation
• Health Care
• Consumer Electronics
• Smart Agriculture
• POS Machines
• Service Robot
• Audio Devices
• Generic Low-power IoT Sensor Hubs
• Generic Low-power IoT Data Loggers
For more information about ESP32-C3, please refer to ESP32-C3 Series Datasheet.
Note:
Unless otherwise specified, “ESP32-C3”used in this document refers to the series of chips, instead of a
specific chip variant.
1.3
Schematic Checklist
1.3.1
Overview
The integrated circuitry of ESP32-C3 requires only 20 electrical components (resistors, capacitors, and inductors)
and a crystal, as well as an SPI flash. The high integration of ESP32-C3 allows for simple peripheral circuit design.
This chapter details the schematic design of ESP32-C3.
The following figure shows a reference schematic design of ESP32-C3. It can be used as the basis of your schematic
design.
Fig. 1: ESP32-C3 Reference Schematic
Espressif Systems
4
Submit Document Feedback
Release master

<!-- Page 8 -->

Chapter 1. Latest Version of This Document
Any basic ESP32-C3 circuit design may be broken down into the following major building blocks:
• Power supply
• Chip power-up and reset timing
• Flash
• Clock source
• RF
• UART
• SPI
• Strapping pins
• GPIO
• ADC
• USB
The rest of this chapter details the specifics of circuit design for each of these sections.
1.3.2
Power Supply
The general recommendations for power supply design are:
• When using a single power supply, the recommended power supply voltage is 3.3 V and the output current is
no less than 500 mA.
• It is suggested to add an ESD protection diode and at least 10 μF capacitor at the main power entrance (where
the external power supply enters the PCB).
The power scheme is shown in ESP32-C3 Series Datasheet > Figure ESP32-C3 Power Scheme.
More information about power supply pins can be found in ESP32-C3 Series Datasheet > Section Power Supply.
Digital Power Supply
ESP32-C3 has pin17 VDD3P3_CPU as the digital power supply pin(s) working in a voltage range of 3.0 V ~ 3.6 V.
It is recommended to add an extra 0.1 μF decoupling capacitor close to the pin(s).
Pin VDD_SPI can serve as the power supply for the external device at 3.3 V (typical value), provided by
VDD3P3_CPU via RSPI. Therefore, there will be some voltage drop from VDD3P3_CPU. When the VDD_SPI
outputs 3.3 V, it is recommended that users add a 1 μF capacitor close to VDD_SPI.
VDD_SPI can be connected to and powered by an external power supply.
When not serving as a power supply pin, VDD_SPI can be used as a regular GPIO.
Attention: When using VDD_SPI as the power supply pin for the in-package flash or external 3.3 V flash, the
supply voltage should be 3.0 V or above, so as to meet the requirements of flash’s working voltage. In such
cases, VDD_SPI cannot be used as a regular GPIO.
Analog Power Supply
ESP32-C3’s VDDA and VDD3P3 pins are the analog power supply pins, working at 3.0 V ~ 3.6 V.
For VDD3P3, when ESP32-C3 is transmitting signals, there may be a sudden increase in the current draw, causing
power rail collapse. Therefore, it is highly recommended to add a 10 μF capacitor to the power rail, which can work
in conjunction with the 0.1 μF capacitor(s) or other capacitors.
It is suggested to add an extra 10 μF capacitor at the main power entrance. If the main power entrance is close to
VDD3P3, then the two 10 μF capacitors can be merged into one.
Espressif Systems
5
Submit Document Feedback
Release master

<!-- Page 9 -->

Chapter 1. Latest Version of This Document
Add an LC circuit to the VDD3P3 power rail to suppress high-frequency harmonics. The inductor’s rated current
is preferably 500 mA and above.
For the remaining capacitor circuits, please refer to ESP32-C3 Reference Schematic.
RTC Power Supply
ESP32-C3’s VDD3P3_RTC pin is the RTC and analog power pin. It is recommended to place a 0.1 μF decoupling
capacitor near this power pin in the circuit.
Note that this power supply cannot be used as a single backup power supply.
The schematic for the RTC power supply pin is shown in Figure ESP32-C3 Schematic for RTC Power Supply Pin.
Fig. 2: ESP32-C3 Schematic for RTC Power Supply Pin
1.3.3
Chip Power-up and Reset Timing
ESP32-C3’s CHIP_EN pin can enable the chip when it is high and reset the chip when it is low.
When ESP32-C3 uses a 3.3 V system power supply, the power rails need some time to stabilize before CHIP_EN
is pulled up and the chip is enabled. Therefore, CHIP_EN needs to be asserted high after the 3.3 V rails have been
brought up.
To reset the chip, keep the reset voltage VIL_nRST in the range of (–0.3 ~ 0.25 × VDD) V. To avoid reboots caused
by external interferences, make the CHIP_EN trace as short as possible.
Figure ESP32-C3 Power-up and Reset Timing shows the power-up and reset timing of ESP32-C3.
Fig. 3: ESP32-C3 Power-up and Reset Timing
Table Description of Timing Parameters for Power-up and Reset provides the specific timing requirements.
Espressif Systems
6
Submit Document Feedback
Release master

<!-- Page 10 -->

Chapter 1. Latest Version of This Document
Table 1: Description of Timing Parameters for Power-up and Reset
Parameter
Description
Minimum (µs)
tSTBL
Time reserved for the power rails to stabilize before the CHIP_EN
pin is pulled high to activate the chip
50
tRST
Time reserved for CHIP_EN to stay below VIL_nRST to reset the
chip
50
Attention:
• CHIP_EN must not be left floating.
• To ensure the correct power-up and reset timing, it is advised to add an RC delay circuit at the CHIP_EN
pin. The recommended setting for the RC delay circuit is usually R = 10 kΩand C = 1 μF. However, specific
parameters should be adjusted based on the characteristics of the actual power supply and the power-up
and reset timing of the chip.
• If the user application has one of the following scenarios:
– Slow power rise or fall, such as during battery charging.
– Frequent power on/off operations.
– Unstable power supply, such as in photovoltaic power generation.
Then, the RC circuit alone may not meet the timing requirements, which may prevent the chip from entering
normal operating mode or cause flash erase operations to occasionally fail to complete. In this case, please
reserve a power monitor chip to reset the chip when the power supply is abnormal, and the threshold of the
power monitor chip is recommended to be around 3.0 V.
1.3.4
Flash
ESP32-C3 can support up to 16 MB external flash, powered by VDD_SPI. It is recommended to add zero-ohm resistor
footprints in series on the SPI communication lines as shown in Figure ESP32-C3 Schematic for External Flash.
These footprints provide flexibility for future adjustments, such as tuning drive strength, mitigating RF interference,
correcting signal timing, and reducing noise, if needed.
For the ESP32-C3 variants with in-package SPI flash, the pins for flash communication cannot be used externally for
other purposes.
Fig. 4: ESP32-C3 Schematic for External Flash
1.3.5
Clock Source
ESP32-C3 supports two external clock sources:
Espressif Systems
7
Submit Document Feedback
Release master

<!-- Page 11 -->

Chapter 1. Latest Version of This Document
• External crystal clock source (Compulsory)
• RTC clock source (Optional)
External Crystal Clock Source (Compulsory)
The ESP32-C3 firmware only supports 40 MHz crystal.
The circuit for the crystal is shown in Figure ESP32-C3 Schematic for External Crystal. Note that the accuracy of the
selected crystal should be within ±10 ppm.
Fig. 5: ESP32-C3 Schematic for External Crystal
Please add a series component on the XTAL_P clock trace. Initially, it is suggested to use an inductor of 24 nH to
reduce the impact of high-frequency crystal harmonics on RF performance, and the value should be adjusted after an
overall test.
The initial values of external capacitors C1 and C2 can be determined according to the formula:
CL = C1 × C2
C1 + C2 + Cstray
where the value of CL (load capacitance) can be found in the crystal’s datasheet, and the value of Cstray refers to the
PCB’s stray capacitance. The values of C1 and C2 need to be further adjusted after an overall test as below:
1. Select TX tone mode using the Certification and Test Tool.
2. Observe the 2.4 GHz signal with a radio communication analyzer or a spectrum analyzer and demodulate it to
obtain the actual frequency offset.
3. Adjust the frequency offset to be within ±10 ppm (recommended) by adjusting the external load capacitance.
• When the center frequency offset is positive, it means that the equivalent load capacitance is small, and the
external load capacitance needs to be increased.
• When the center frequency offset is negative, it means the equivalent load capacitance is large, and the external
load capacitance needs to be reduced.
• External load capacitance at the two sides are usually equal, but in special cases, they may have slightly different
values.
Note:
• Defects in the manufacturing of crystal (for example, large frequency deviation of more than ±10 ppm, unstable
performance within the operating temperature range, etc) may lead to the malfunction of ESP32-C3, resulting
in a decrease of the RF performance.
• It is recommended that the amplitude of the crystal is greater than 500 mV.
• When Wi-Fi or Bluetooth connection fails, after ruling out software problems, you may follow the steps men-
tioned above to ensure that the frequency offset meets the requirements by adjusting capacitors at the two sides
of the crystal.
Espressif Systems
8
Submit Document Feedback
Release master

<!-- Page 12 -->

Chapter 1. Latest Version of This Document
RTC Clock Source (Optional)
ESP32-C3 supports an external 32.768 kHz crystal to act as the RTC clock. The external RTC clock source enhances
timing accuracy and consequently decreases average power consumption, without impacting functionality.
Figure ESP32-C3 Schematic for 32.768 kHz Crystal shows the schematic for the external 32.768 kHz crystal.
Fig. 6: ESP32-C3 Schematic for 32.768 kHz Crystal
Please note the requirements for the 32.768 kHz crystal:
• Equivalent series resistance (ESR) ≤70 kΩ.
• Load capacitance at both ends should be configured according to the crystal’s specification.
The parallel resistor R is used for biasing the crystal circuit (5 MΩ< R ≤10 MΩ).
In general, you do not need to populate the resistor.
If the RTC clock source is not required, then the pins for the 32.768 kHz crystal can be used as GPIOs.
1.3.6
RF
RF Circuit
ESP32-C3’s RF circuit is mainly composed of three parts, the RF traces on the PCB board, the chip matching
circuit, the antenna and the antenna matching circuit. Each part should meet the following requirements:
• For the RF traces on the PCB board, 50 Ωimpedance control is required.
• For the chip matching circuit, it must be placed close to the chip. A CLC structure is preferred.
– The CLC structure is mainly used to adjust the impedance point and suppress harmonics, and
a set of LC can be added if space permits.
– The RF matching circuit is shown in Figure ESP32-C3 Schematic for RF Matching.
• For the antenna and the antenna matching circuit, to ensure radiation performance, the antenna’s characteristic
impedance must be around 50 Ω. Adding a CLC matching circuit near the antenna is recommended to adjust
the antenna. However, if the available space is limited and the antenna impedance point can be guaranteed to
be 50 Ωby simulation, then there is no need to add a matching circuit near the antenna.
RF Tuning
The RF matching parameters vary with the board, so the ones used in Espressif modules could not be applied directly.
Follow the instructions below to do RF tuning.
Figure ESP32-C3 RF Tuning Diagram shows the general process of RF tuning.
In the matching circuit, define the port near the chip as Port 1 and the port near the antenna as Port 2. S11 describes
the ratio of the signal power reflected back from Port 1 to the input signal power, the transmission performance is
best if the matching impedance is conjugate to the chip impedance. S21 is used to describe the transmission loss of
Espressif Systems
9
Submit Document Feedback
Release master

<!-- Page 13 -->

Chapter 1. Latest Version of This Document
Fig. 7: ESP32-C3 Schematic for RF Matching
Fig. 8: ESP32-C3 RF Tuning Diagram
Espressif Systems
10
Submit Document Feedback
Release master

<!-- Page 14 -->

Chapter 1. Latest Version of This Document
signal from Port 1 to Port 2. If S11 is close to the chip conjugate point 35+j0 and S21 is less than -35 dB at 4.8 GHz
and 7.2 GHz, the matching circuit can satisfy transmission requirements.
Connect the two ends of the matching circuit to the network analyzer, and test its signal reflection parameter S11
and transmission parameter S21. Adjust the values of the components in the circuit until S11 and S21 meet the
requirements. If your PCB design of the chip strictly follows the PCB design stated in Chapter PCB Layout Design,
you can refer to the value ranges in Table Recommended Value Ranges for Components to debug the matching circuit.
Table 2: Recommended Value Ranges for Components
Reference Desig-
nator
Recommended Value Range
Serial No.
C11
1.2 ~ 1.8 pF
GRM0335C1H1RXBA01D
L2
2.0 ~ 3.0 nH
LQP03TN2NXB02D
C12
1.8 ~ 1.2 pF
GRM0335C1H1RXBA01D
Please use 0201 packages for RF matching components and add a stub to the first capacitor in the matching circuit
at the chip end.
Note:
If RF function is not required, it is recommended not to initialize the RF stack in firmware. In this case,
the RF pin can be left floating. However, if RF function is enabled, make sure an antenna is connected. Operation
without an antenna may result in unstable behavior or potential damage to the RF circuit.
1.3.7
UART
Usually, UART0 is used as the serial port for download and log printing. For instructions on download over UART0,
please refer to Section Download Guidelines. It is recommended to connect a 499 Ωseries resistor to the U0TXD
line to suppress harmonics.
For application communication, use UART interfaces other than UART0 if possible. Add a series resistor on the TX
line to suppress harmonics.
When using the AT firmware, please note that the UART GPIO is already configured (refer to Hardware Connection).
It is recommended to use the default configuration.
1.3.8
SPI
When using the SPI function, to improve EMC performance, add a series resistor (or ferrite bead) and a capacitor
to ground on the SPI_CLK trace. If space allows, it is recommended to also add a series resistor and capacitor to
ground on other SPI traces. Ensure that the RC/LC components are placed close to the pins of the chip or module.
1.3.9
Strapping Pins
At each startup or reset, a chip requires some initial configuration parameters, such as in which boot mode to load
the chip, etc. These parameters are passed over via the strapping pins. After reset, the strapping pins work as normal
function pins.
GPIO2, GPIO8, and GPIO9 are strapping pins.
All the information about strapping pins is covered in ESP32-C3 Series Datasheet > Chapter Boot Configurations.
In this section, we will mainly cover the strapping pins related to boot mode.
After chip reset is released, the combination of GPIO2, GPIO8, and GPIO9 controls the boot mode. See Table Boot
Mode Control.
Espressif Systems
11
Submit Document Feedback
Release master

<!-- Page 15 -->

Chapter 1. Latest Version of This Document
Table 3: Boot Mode Control
Boot Mode
GPIO2Page 12, 1
GPIO8
GPIO9
Default Config
–(Floating)
–(Floating)
1 (Pull-up)
SPI Boot (default)
1
Any value
1
Joint Download Boot2
1
1
0
Signals applied to the strapping pins should have specific setup time and hold time. For more information, see Figure
Setup and Hold Times for Strapping Pins and Table Description of Timing Parameters for Strapping Pins.
Fig. 9: Setup and Hold Times for Strapping Pins
Table 4: Description of Timing Parameters for Strapping Pins
Parameter
Description
Minimum (ms)
tSU
Time reserved for the power rails to stabilize before the chip enable
pin (CHIP_EN) is pulled high to activate the chip.
0
tH
Time reserved for the chip to read the strapping pin values after
CHIP_EN is already high and before these pins start operating as
regular IO pins.
3
Attention:
• It is recommended to place a pull-up resistor at the GPIO9 pin.
• Do not add high-value capacitors at GPIO9, or the chip may enter download mode.
1 GPIO2 actually does not determine SPI Boot and Joint Download Boot mode, but it is recommended to pull this pin up due to glitches.
2 Joint Download Boot mode supports the following download methods:
• USB-Serial-JTAG Download Boot
• UART Download Boot
Espressif Systems
12
Submit Document Feedback
Release master

<!-- Page 16 -->

Chapter 1. Latest Version of This Document
1.3.10
GPIO
The pins of ESP32-C3 can be configured via IO MUX or GPIO matrix. IO MUX provides the default pin configura-
tions (see ESP32-C3 Series Datasheet > Appendix ESP32-C3 Consolidated Pin Overview), whereas the GPIO matrix
is used to route signals from peripherals to GPIO pins. For more information about IO MUX and GPIO matrix,
please refer to ESP32-C3 Technical Reference Manual > Chapter IO MUX and GPIO Matrix.
Some peripheral signals have already been routed to certain GPIO pins, while some can be routed to any available
GPIO pins. For details, please refer to ESP32-C3 Series Datasheet > Section Peripherals.
When using GPIOs, please:
• Pay attention to the states of strapping pins during power-up.
• Pay attention to the default GPIO configurations after reset (see the table below). For unused pins in the high-
impedance state without an internal pull-up or pull-down, it is recommended to add a pull-up or pull-down
resistor or enable the internal pull during software initialization to avoid extra power consumption, selecting
the direction as required by the external circuit.
• Avoid using the pins already occupied by flash.
• Some pins will have glitches during power-up. Refer to Table Power-Up Glitches on Pins for details.
Table 5: IO MUX Pin Functions
Name
No.
Function 0
Function 1
Function 2
Reset
Notes
XTAL_32K_P
4
GPIO0
GPIO0
—
0
R
XTAL_32K_N
5
GPIO1
GPIO1
—
0
R
GPIO2
6
GPIO2
GPIO2
FSPIQ
1
R
GPIO3
8
GPIO3
GPIO3
—
1
R
MTMS
9
MTMS
GPIO4
FSPIHD
1
R
MTDI
10
MTDI
GPIO5
FSPIWP
1
R
MTCK
12
MTCK
GPIO6
FSPICLK
1*
G
MTDO
13
MTDO
GPIO7
FSPID
1
G
GPIO8
14
GPIO8
GPIO8
—
1
—
GPIO9
15
GPIO9
GPIO9
—
3
—
GPIO10
16
GPIO10
GPIO10
FSPICS0
1
G
VDD_SPI
18
GPIO11
GPIO11
—
0
—
SPIHD
19
SPIHD
GPIO12
—
3
—
SPIWP
20
SPIWP
GPIO13
—
3
—
SPICS0
21
SPICS0
GPIO14
—
3
—
SPICLK
22
SPICLK
GPIO15
—
3
—
SPID
23
SPID
GPIO16
—
3
—
SPIQ
24
SPIQ
GPIO17
—
3
—
GPIO18
25
GPIO18
GPIO18
—
0
USB, G
GPIO19
26
GPIO19
GPIO19
—
0*
USB
U0RXD
27
U0RXD
GPIO20
—
3
G
U0TXD
28
U0TXD
GPIO21
—
4
—
Reset
The default configuration of each pin after reset:
• 0 –input disabled, in high impedance state (IE = 0)
• 1 –input enabled, in high impedance state (IE = 1)
• 2 –input enabled, pull-down resistor enabled (IE = 1, WPD = 1)
• 3 –input enabled, pull-up resistor enabled (IE = 1, WPU = 1)
• 4 –output enabled, pull-up resistor enabled (OE = 1, WPU = 1)
• 0* –input disabled, pull-up resistor enabled (IE = 0, WPU = 0, USB_WPU = 1). See details in Notes
• 1* –When the value of eFuse bit EFUSE_DIS_PAD_JTAG is
– 0, input enabled, pull-up resistor enabled (IE = 1, WPU = 1)
Espressif Systems
13
Submit Document Feedback
Release master

<!-- Page 17 -->

Chapter 1. Latest Version of This Document
– 1, input enabled, in high impedance state (IE = 1)
Notes
• R –These pins have analog functions.
• USB –GPIO18 and GPIO19 are USB pins.
– By default,
the USB function is enabled for USB pins (i.e.,
GPIO18 and GPIO19),
and
the pin pull-up is decided by the USB pull-up resistor.
The USB pull-up resistor is
controlled by USB_SERIAL_JTAG_DP/DM_PULLUP and the pull-up value is controlled by
USB_SERIAL_JTAG_PULLUP_VALUE. For details, see ESP32-C3 Technical Reference Manual >
Chapter USB Serial/JTAG Controller.
– When the USB function is disabled, USB pins are used as regular GPIOs and the pin’s internal weak
pull-up and pull-down resistors are disabled by default (configurable by IO_MUX_FUN_WPU/WPD).
• G –These pins have glitches during power-up. See details in Table Power-Up Glitches on Pins.
Table 6: Power-Up Glitches on Pins
Pin
GlitchPage 14, 3
Typical Time (ns)
MTCK
Low-level glitch
5
MTDO
Low-level glitch
5
GPIO10
Low-level glitch
5
U0RXD
Low-level glitch
5
GPIO18
High-level glitch
50,000
1.3.11
ADC
Please add a 0.1 μF filter capacitor between ESP pins and ground when using the ADC function to improve accuracy.
It is recommend to use ADC1, given that ADC2 is not factory-calibrated, and ADC2 of some chip revisions is not
operable. For details, please refer to ESP32-C3 Series SoC Errata.
The calibrated ADC results after hardware calibration and software calibration are shown in the list below. For higher
accuracy, you may implement your own calibration methods.
• When ATTEN=0 and the effective measurement range is 0 ~ 750 mV, the total error is ±10 mV.
• When ATTEN=1 and the effective measurement range is 0 ~ 1050 mV, the total error is ±10 mV.
• When ATTEN=2 and the effective measurement range is 0 ~ 1300 mV, the total error is ±10 mV.
• When ATTEN=3 and the effective measurement range is 0 ~ 2500 mV, the total error is ±35 mV.
1.3.12
USB
ESP32-C3 integrates a USB Serial/JTAG controller that supports USB 2.0 full-speed device.
GPIO18 and GPIO19 can be used as D- and D+ of USB respectively. It is recommended to reserve series resistors
(initial value can be 22/33 Ω) and capacitors to ground on the traces (initially can be unpopulated), and place them
close to the chip.
Note that upon power-up, the USB_D+ signal will fluctuate between high and low states. The high-level signal is
relatively strong and requires a robust pull-down resistor to drive it low. Therefore, if you need a stable initial state,
adding an external pull-up resistor is recommended to ensure a consistent high-level output voltage at startup.
ESP32-C3 also supports download functions and log message printing via USB. For details please refer to Section
Download Guidelines.
3
• Low-level glitch: the pin is at a low level output status during the time period;
• High-level glitch: the pin is at a high level output status during the time period.
Espressif Systems
14
Submit Document Feedback
Release master

<!-- Page 18 -->

Chapter 1. Latest Version of This Document
1.4
PCB Layout Design
This chapter introduces the key points of how to design an ESP32-C3 PCB layout using an ESP32-C3 module (see
Figure ESP32-C3 Reference PCB Layout) as an example.
Fig. 10: ESP32-C3 Reference PCB Layout
1.4.1
General Principles of PCB Layout for the Chip
It is recommended to use a four-layer PCB design:
• Layer 1 (TOP): Signal traces and components.
• Layer 2 (GND): No signal traces here to ensure a complete GND plane.
• Layer 3 (POWER): GND plane should be applied to better isolate the RF and crystal. Route power traces and
a few signal traces on this layer, provided that there is a complete GND plane under the RF and crystal.
• Layer 4 (BOTTOM): Route a few signal traces here. It is not recommended to place any components on this
layer.
A two-layer PCB design can also be used:
• Layer 1 (TOP): Signal traces and components.
• Layer 2 (BOTTOM): Do not place any components on this layer and keep traces to a minimum. Please make
sure there is a complete GND plane for the chip, RF, and crystal.
1.4.2
Power Supply
Four-Layer PCB Design
Figure ESP32-C3 Power Traces in a Four-Layer PCB Design shows the power traces in a four-layer PCB design.
• A four-layer PCB design is recommended. Whenever possible, route the power traces on the inner layers (not
the ground layer) and connect them to the chip pins through vias. There should be at least two vias if the main
power traces need to cross layers. The drill diameter on other power traces should be no smaller than the width
of the power traces.
Espressif Systems
15
Submit Document Feedback
Release master

<!-- Page 19 -->

Chapter 1. Latest Version of This Document
Fig. 11: ESP32-C3 Power Traces in a Four-Layer PCB Design
• The yellow highlighted traces in Figure ESP32-C3 Power Traces in a Four-Layer PCB Design are the 3.3 V
power traces. The width of the main power traces should be no less than 25 mil. The width of VDD3P3 power
traces should be no less than 20 mil. The recommended width of other power traces is 10 mil. Ensure the
power traces are surrounded by ground copper.
• The red circles in ESP32-C3 Power Traces in a Four-Layer PCB Design show ESD protection diodes. Place
them close to the power input. Add a 10 µF capacitor before the power trace enters the chip. You can also
add a 0.1 µF or 1 µF capacitor in parallel. After that, the power trace can branch out in a star-shaped layout to
reduce coupling between different power pins.
• The power supply for pin2 and pin3 is RF related, so please place a 10 µF capacitor for each pin. You can also
add a 0.1 µF or 1 µF capacitor in parallel.
• Add a CLC/LC filter circuit near pin2 and pin3 to suppress high-frequency harmonics. The power trace can
be routed at a 45-degree angle to maintain distance from adjacent RF traces. Except for the 10 µF capacitor,
it is recommended to use 0201 components. This allows the filter circuit for pin2 and pin3 to be placed closer
to the pins, with a GND isolation layer separating them from surrounding RF and GPIO traces, while also
maximizing the placement of ground vias. Using 0201 components enables placing a via to the bottom layer at
the first capacitor near the chip, while maintaining a keep-out area on other layers, further reducing harmonic
interference. See Figure ESP32-C3 Power Traces in a Four-Layer PCB Design.
• In Figure ESP32-C3 Power Traces in a Four-Layer PCB Design, the 10 µF capacitor is shared by the analog
power supply VDD3P3, and the power entrance since the analog power is close to the chip power entrance.
If the chip power entrance is not near VDD3P3, it is recommended to add a 10 µF capacitor to both the chip
power entrance and VDD3P3.
• Place appropriate decoupling capacitors at the rest of the power pins. Ground vias should be added close to
the capacitor’s ground pad to ensure a short return path.
• The ground pad at the bottom of the chip should be connected to the ground plane through at least nine ground
vias.
• The ground pads of the chip and surrounding circuit components should make full contact with the ground
copper pour rather than being connected via traces.
• If you need to add a thermal pad EPAD under the chip on the bottom of the module, it is recommended to
employ a square grid on the EPAD, cover the gaps with solder paste, and place ground vias in the gaps, as
shown in Figure ESP32-C3 Power Traces in a Four-Layer PCB Design. This helps effectively reduce solder
leakage issues when soldering the module EPAD to the substrate.
• For optimal grounding, connect the EPAD to a large external ground area using wide traces or copper planes.
Two-Layer PCB Design
Figure ESP32 Power Traces in a Two-Layer PCB Design shows the power traces in a two-layer PCB design.
Espressif Systems
16
Submit Document Feedback
Release master

<!-- Page 20 -->

Chapter 1. Latest Version of This Document
Fig. 12: ESP32 Power Traces in a Two-Layer PCB Design
• For a two-layer design, ensure to provide a continuous reference ground for the chip, RF, and crystal oscillator,
as shown in the figure above.
• In the figure above, the trace VDD33 represents the 3.3 V power trace. Unlike a four-layer design, the power
trace should be routed on the top layer as much as possible. Therefore, the thermal pad in the center of the
chip should be reduced in size, allowing the power trace to pass between the signal pads and the thermal pad.
Vias to the bottom layer should only be used when absolutely necessary.
• Other layout considerations are the same as for a four-layer design.
• Note that there are no official two-layer modules. The figure above uses the ESP32 module as an example.
1.4.3
Crystal
Figure ESP32-C3 Crystal Layout (without Keep-out Area on Top Layer) shows the layout for the crystal that is con-
nected to the ground through vias but there is no keep-out area on the top layer for ground isolation.
The layout of the crystal should follow the guidelines below:
• Ensure a complete GND plane for the RF, crystal, and chip.
• The crystal should be placed far from the clock pin to avoid interference on the chip. The gap should be at least
2.0 mm. It is good practice to add high-density ground vias stitching around the clock trace for better isolation.
• There should be no vias for the clock input and output traces.
• Components in series to the crystal trace should be placed close to the chip side.
• The external matching capacitors should be placed on the two sides of the crystal, preferably at the end of the
clock trace, but not connected directly to the series components. This is to make sure the ground pad of the
capacitor is close to that of the crystal.
• Do not route high-frequency digital signal traces under the crystal. It is best not to route any signal trace under
the crystal. The vias on the power traces on both sides of the crystal clock trace should be placed as far away
from the clock trace as possible, and the two sides of the clock trace should be surrounded by ground copper.
• As the crystal is a sensitive component, do not place any magnetic components nearby that may cause interfer-
ence, for example large inductance component, and ensure that there is a clean large-area ground plane around
the crystal.
Espressif Systems
17
Submit Document Feedback
Release master

<!-- Page 21 -->

Chapter 1. Latest Version of This Document
Fig. 13: ESP32-C3 Crystal Layout (without Keep-out Area on Top Layer)
1.4.4
RF
The RF trace is routed as shown highlighted in pink in Figure ESP32-C3 RF Layout in a Four-layer PCB Design.
Fig. 14: ESP32-C3 RF Layout in a Four-layer PCB Design
The RF layout should meet the following guidelines:
• The RF trace should have a 50 Ω characteristic impedance. The reference plane is the layer next to the chip.
For designing the RF trace at 50 Ω impedance, you could refer to the PCB stack-up design shown below.
• A CLC matching circuit is required for chip tuning. Please use 0201 components and place them close to the
pin in a zigzag. In other words, the two capacitors should not be oriented in the same direction to minimize
interference.
• Add a stub on the ground pad of the grounding capacitor near the chip side in the matching circuit to suppress
the second harmonics. It is preferable to keep the stub length 15 mil, and determine the stub width according
to the PCB stack-up so that the characteristic impedance of the stub is 100 Ω± 10%. The reference plane
Espressif Systems
18
Submit Document Feedback
Release master

<!-- Page 22 -->

Chapter 1. Latest Version of This Document
Fig. 15: ESP32-C3 PCB Stack-up Design
is the third layer, so the area under the trace on the second layer should be cleared. The trace highlighted in
Figure ESP32-C3 Stub in a Four-layer PCB Design is the stub. Note that a stub is not required for package
types of 0402 and above.
• For PCB antennas, make sure to validate them through both simulation and real-world testing on a development
board. It is recommended to include an additional CLC matching circuit for antenna tuning. Place this circuit
as close to the antenna as possible.
• The RF trace should have a consistent width and not branch out. It should be as short as possible with dense
ground vias around for interference shielding.
• The RF trace should be routed on the outer layer without vias, i.e., should not cross layers. The RF trace should
be routed at a 135° angle, or with circular arcs if trace bends are required.
• The ground plane on the adjacent layer needs to be complete. Do not route any traces under the RF trace
whenever possible.
• There should be no high-frequency signal traces routed close to the RF trace. The RF antenna should be
placed away from high-frequency components, such as crystals, DDR SDRAM, high-frequency clocks, etc. In
addition, the USB port, USB-to-serial chip, UART signal lines (including traces, vias, test points, header pins,
etc.) must be as far away from the antenna as possible. The UART signal line should be surrounded by ground
copper and ground vias.
1.4.5
Flash
The layout for flash should follow the guidelines below:
• Place the zero-ohm resistors in series on the SPI lines close to ESP32-C3.
• Route the SPI traces on the inner layer (e.g., the third layer) whenever possible, and add ground copper and
ground vias around the clock and data traces of SPI separately.
Espressif Systems
19
Submit Document Feedback
Release master

<!-- Page 23 -->

Chapter 1. Latest Version of This Document
Fig. 16: ESP32-C3 Stub in a Four-layer PCB Design
• If the flash and PSRAM are located far from ESP32-C3, it is recommended to place appropriate decoupling
capacitors both at VDD_SPI and near the flash and PSRAM power supply.
Figure ESP32-C3 Quad SPI Flash Layout shows the quad SPI flash layout.
Fig. 17: ESP32-C3 Quad SPI Flash Layout
1.4.6
UART
Figure ESP32-C3 UART Layout shows the UART layout.
The UART layout should meet the following guidelines:
• The series resistor on the U0TXD trace needs to be placed close to the chip side and away from the crystal.
• The U0TXD and U0RXD traces on the top layer should be as short as possible.
Espressif Systems
20
Submit Document Feedback
Release master

<!-- Page 24 -->

Chapter 1. Latest Version of This Document
Fig. 18: ESP32-C3 UART Layout
• The UART trace should be surrounded by ground copper and ground vias stitching.
1.4.7
General Principles of PCB Layout for Modules (Positioning a Module on a Base
Board)
If module-on-board design is adopted, attention should be paid while positioning the module on the base board. The
interference of the baseboard on the module’s antenna performance should be minimized.
It is suggested to place the module’s on-board PCB antenna outside the base board, and the feed point of the
antenna close to the edge of the base board. In the following example figures, positions with mark ✓are strongly
recommended, while positions without a mark are not recommended.
Fig. 19: Placement of ESP32-C3 Modules on Base Board (antenna feed point on the right)
If the antenna cannot extend beyond the board edge, the feed point should still be placed as close to the board edge
as possible. Then cut off the base board on both sides of the antenna and below it to minimize the impact of the
base board material on the PCB antenna and provide a sufficiently large clearance area for the PCB antenna. Note
that the module should not be placed in the center of the board with clearance created by hollowing out on all four
Espressif Systems
21
Submit Document Feedback
Release master

<!-- Page 25 -->

Chapter 1. Latest Version of This Document
Fig. 20: Placement of ESP32-C3 Modules on Base Board (antenna feed point on the left)
sides. Figure Keepout Zone for ESP32-C3 Module’s Antenna (Antenna feed point on the Left) shows the suggested
clearance area. Please note that sufficient ground copper and dense ground vias should be placed on the base board
near the antenna.
After the base board is placed in the end product, please consider the impact of the housing on the antenna during
end-product design. Ensure that the PCB antenna on the base board also has a sufficiently large clearance area inside
the housing. A clearance of at least 15 mm is recommended in all directions.
Please note that the final end product should be tested for throughput and communication range to ensure RF perfor-
mance.
1.4.8
USB
The USB layout should meet the following guidelines:
• Reserve space for resistors and capacitors on the USB traces close to the chip side.
• Use differential pairs and route them in parallel at equal lengths. Maintain a differential pair impedance of 90
Ω with a tolerance of ±10%.
• USB differential traces should minimize via transitions as much as possible to ensure better impedance control
and avoid signal reflections. If vias are necessary, add a pair of ground return vias at each transition point.
• Ensure there is a continuous reference layer (a ground layer is recommended) beneath the USB traces.
• Surround the USB traces with ground copper.
1.4.9
Typical Layout Problems and Solutions
When ESP32-C3 sends data packages, the voltage ripple is small, but RF TX performance is poor.
Analysis: The RF TX performance can be affected not only by voltage ripples, but also by the crystal itself. Poor
quality and big frequency offsets of the crystal decrease the RF TX performance. The crystal clock may be corrupted
by other interfering signals, such as high-speed output or input signals. In addition, high-frequency signal traces,
such as the SDIO traces and UART traces under the crystal, could also result in the malfunction of the crystal.
Besides, sensitive components or radiating components, such as inductors and antennas, may also decrease the RF
performance.
Espressif Systems
22
Submit Document Feedback
Release master

<!-- Page 26 -->

Chapter 1. Latest Version of This Document
Fig. 21: Keepout Zone for ESP32-C3 Module’s Antenna (Antenna feed point on the Left)
Solution: This problem is caused by improper layout for the crystal and can be solved by re-layout. Please refer to
Section Crystal for details.
When ESP32-C3 sends data packages, the power value is much higher or lower than the target power value,
and the EVM is relatively poor.
Analysis: The disparity between the tested value and the target value may be due to signal reflection caused by
the impedance mismatch on the transmission line connecting the RF pin and the antenna. Besides, the impedance
mismatch will affect the working state of the internal PA, making the PA prematurely access the saturated region in
an abnormal way. The EVM becomes poor as the signal distortion happens.
Solution: Match the antenna’s impedance with the π-type circuit on the RF trace, so that the impedance of the
antenna as seen from the RF pin matches closely with that of the chip. This reduces reflections to the minimum.
TX performance is not bad, but the RX sensitivity is low.
Analysis: Good TX performance indicates proper RF impedance matching. Poor RX sensitivity may result from
external coupling to the antenna. For instance, the crystal signal harmonics could couple to the antenna. If the TX
and RX traces of UART cross over with RF trace, they will affect the RX performance, as well. If there are many
high-frequency interference sources on the board, signal integrity should be considered.
Solution: Keep the antenna away from crystals. Do not route high-frequency signal traces close to the RF trace.
Please refer to Section RF for details.
1.5
Download Guidelines
Espressif Systems
23
Submit Document Feedback
Release master

<!-- Page 27 -->

Chapter 1. Latest Version of This Document
You can download firmware to ESP32-C3 via UART and USB.
To download via UART:
1. Before the download, make sure to set the chip or module to Joint Download Boot mode, according to Table
Boot Mode Control.
2. Power up the chip or module and check the log via the UART0 serial port. If the log shows “waiting for
download”, the chip or module has entered Joint Download Boot mode.
3. Use the Flash Download Tool to flash firmware into flash via UART.
4. After the firmware has been downloaded, pull GPIO9 high or leave it floating to make sure that the chip or
module enters SPI Boot mode.
5. Power up the chip or module again. The chip will read and execute the new firmware during initialization.
To download via USB:
1. If the flash is empty, set the chip or module to Joint Download Boot mode, according to Table Boot Mode
Control.
2. Power up the chip or module and check the log via USB serial port. If the log shows “waiting for download”
, the chip or module has entered Joint Download Boot mode.
3. Use the Flash Download Tool to flash firmware into flash via USB.
4. After the firmware has been downloaded, pull GPIO9 high or leave it floating to make sure that the chip or
module enters SPI Boot mode.
5. Power up the chip or module again. The chip will read and execute the new firmware during initialization.
6. If the flash is not empty, start directly from Step 3.
Note:
• For firmware download instructions, see also ESP Product Firmware Download Instructions.
• For how to check serial port output, see also Establish Serial Connection with ESP32-C3.
• It is advised to download the firmware only after the “waiting for download”log shows via the serial port.
• Serial tools cannot be used simultaneously with the Flash Download Tool on one COM port.
• The USB auto-download will be disabled if the following conditions occur in the application, where it will be
necessary to set the chip or module to Joint Download Boot mode first by configuring the strapping pin.
– USB PHY is disabled by the application;
– USB is configured for other USB functions, e.g., USB host, USB standard device;
– USB IOs are configured to other peripherals, such as UART and LEDC.
• It is recommended that the user retains control of the strapping pins to avoid the USB download function not
being available in case of the above scenario.
• It is recommended to retain the UART download interface, as the current RF test firmware only supports the
UART interface.
1.6
Related Documentation and Resources
1.6.1
ESP32-C3 Modules
For a list of ESP32-C3 modules please check the Modules section on Espressif’s official website.
For module reference designs please refer to:
• Download links
Note: Use the following tools to open the files in module reference designs:
Espressif Systems
24
Submit Document Feedback
Release master

<!-- Page 28 -->

Chapter 1. Latest Version of This Document
• .DSN files: OrCAD Capture V16.6
• .pcb files: Pads Layout VX.2. If you cannot open the .pcb files, please try importing the .asc files into your
software to view the PCB layout.
1.6.2
ESP32-C3 Development Boards
For a list of the latest designs of ESP32-C3 boards please check the Development Boards section on Espressif’s
official website.
1.6.3
Other Related Documentation and Resources
• Chip Datasheet (PDF)
• Technical Reference Manual (PDF)
• Chip Errata
• ESP32-C3 Chip Variants
• Espressif KiCad Library
• ESP Product Selector
• Regulatory Certificates
• User Forum (Hardware)
• Technical Support
• ESP-FAQ
1.7
Glossary
The glossary contains terms and acronyms that are used in this document.
Term
Description
CLC
Capacitor-Inductor-Capacitor
DDR SDRAM
Double Data Rate Synchronous Dynamic Random-Access Memory
ESD
Electrostatic Discharge
LC
Inductor-Capacitor
PA
Power Amplifier
RC
Resistor-Capacitor
RTC
Real-Time Clock
Zero-ohm resistor
A zero-ohm resistor acts as a placeholder in the circuit, allowing for the replacement with
a higher-ohm resistor based on specific design requirements.
1.8
Revision History
Espressif Systems
25
Submit Document Feedback
Release master

<!-- Page 29 -->

Chapter 1. Latest Version of This Document
Table 7: Revision History
Date
Version
Release Notes
2025-06-05
v1.8
•PCB Layout Design
– Section USB: Updated descriptions about the USB layout
guidelines
2025-05-23
v1.7
•PCB Layout Design
– Section Crystal: Updated descriptions about the crystal layout
guidelines
2025-01-07
v1.6
•ESP32-C3 Modules：
– Added download links to module reference designs
2024-11-15
v1.5
•Schematic Checklist
– Section SPI: Newly added section
2024-10-15
v1.4
•Schematic Checklist
– Section UART: Updated the AT related description
2024-02-18
v1.3
•PCB Layout Design
– Section General Principles of PCB Layout for Modules (Posi-
tioning a Module on a Base Board): Updated Figure Placement
of ESP32-C3 Modules on Base Board (antenna feed point on
the right) and Figure Placement of ESP32-C3 Modules on Base
Board (antenna feed point on the left)
2024-01-09
v1.2
•Schematic Checklist
– Section RF Tuning: Updated RF matching description
2023-12-25
v1.1
•PCB Layout Design
– Section Crystal: Updated crystal PCB layout
2023-12-22
v1.0
Migrated ESP32-C3 Hardware Design Guidelines from PDF to HTML for-
mat. During the migration from PDF to HTML format, minor updates, im-
provements, and clarifications were made throughout the documentation. If
you would like to check previous versions of the document, please submit doc-
umentation feedback.
1.9
Disclaimer and Copyright Notice
Information in this document, including URL references, is subject to change without notice.
All third party’s information in this document is provided as is with no warranties to its authenticity and accuracy.
No warranty is provided to this document for its merchantability, non-infringement, fitness for any particular purpose,
nor does any warranty otherwise arising out of any proposal, specification or sample.
All liability, including liability for infringement of any proprietary rights, relating to use of information in this doc-
ument is disclaimed. No licenses express or implied, by estoppel or otherwise, to any intellectual property rights are
Espressif Systems
26
Submit Document Feedback
Release master

<!-- Page 30 -->

Chapter 1. Latest Version of This Document
granted herein.
The Wi-Fi Alliance Member logo is a trademark of the Wi-Fi Alliance. The Bluetooth logo is a registered trademark
of Bluetooth SIG.
All trade names, trademarks and registered trademarks mentioned in this document are property of their respective
owners, and are hereby acknowledged.
Espressif Systems
27
Submit Document Feedback
Release master

---

# 3. SSD1680 Datasheet

> **Source file:** `SSD1680.pdf`  
> Solomon Systech — SSD1680 active matrix EPD display driver / controller

<!-- Page 1 -->

SOLOMON SYSTECH
SEMICONDUCTOR TECHNICAL DATA
This document contains information on a product under development. Solomon Systech reserves the right to change
or discontinue this product without notice.
http://www.solomon-systech.com
SSD1680
Rev 0.14
P 1/46
Jun 2019
Copyright  2019 Solomon Systech Limited
SSD1680
Product Preview
176 Source x 296 Gate Red/Black/White
Active Matrix EPD Display Driver with Controller

<!-- Page 2 -->

SSD1680
Rev 0.14
P 2/46
Jun 2019
Solomon Systech
Appendix: IC Revision history of SSD1680 Specification
Version
Change Items
Effective Date
0.10
Initial Release
28-Feb-19
0.11
Updated Feature list
02-Apr-19
0.12
Updated AC Characteristics
Updated Component list
21-May-19
0.13
Updated Component list
24-May-19
0.14
Updated Component list, removed case size for C0 and C1.
5-Jun-19

<!-- Page 3 -->

SSD1680
Rev 0.14
P 3/46
Jun 2019
Solomon Systech
CONTENTS
1
GENERAL DESCRIPTION ....................................................................................................... 5
2
FEATURES ............................................................................................................................... 5
3
ORDERING INFORMATION..................................................................................................... 6
4
BLOCK DIAGRAM ................................................................................................................... 6
5
PIN DESCRIPTION ................................................................................................................... 7
6
FUNCTIONAL BLOCK DESCRIPTION .................................................................................. 10
6.1
MCU INTERFACE ........................................................................................................................... 10
6.1.1 MCU INTERFACE SELECTION.......................................................................................................... 10
6.1.2 MCU SERIAL INTERFACE (4-WIRE SPI) ........................................................................................... 10
6.1.3 MCU SERIAL PERIPHERAL INTERFACE (3-WIRE SPI) ....................................................................... 11
6.2
OSCILLATOR .............................................................................................................................. 12
6.3
BOOSTER & REGULATOR ......................................................................................................... 12
6.4
VCOM SENSING ......................................................................................................................... 12
6.5
RAM ............................................................................................................................................ 13
6.6
PROGRAMMABLE WAVEFORM FOR GATE, SOURCE AND VCOM ........................................................ 13
6.7
WAVEFORM SETTING ............................................................................................................... 15
6.8
TEMPERATURE SEARCHING............................................................................................................ 16
6.8.1 INTERNAL TEMPERATURE SENSOR ................................................................................................. 16
6.8.2 EXTERNAL TEMPERATURE SENSOR I2C SINGLE MASTER INTERFACE ............................................... 16
6.8.3 FORMAT OF TEMPERATURE VALUE .................................................................................................. 16
6.9
WAVEFORM SETTING SEARCHING MECHANISM ................................................................................ 17
6.10
ONE TIME PROGRAMMABLE (OTP) MEMORY ................................................................................... 18
6.11
THE FORMAT FOR TEMPERATURE RANGE (TR) ............................................................................... 18
6.12
CASCADE MODE ............................................................................................................................ 19
6.13
VCI DETECTION ............................................................................................................................ 19
6.14
HV READY DETECTION .................................................................................................................. 19
7
COMMAND TABLE ................................................................................................................ 20
8
COMMAND DESCRIPTION ................................................................................................... 34
8.1
DRIVER OUTPUT CONTROL (01H) ................................................................................................... 34
8.2
GATE SCAN START POSITION (0FH) ............................................................................................... 36
8.3
DATA ENTRY MODE SETTING (11H) ................................................................................................ 37
8.4
SET RAM X - ADDRESS START / END POSITION (44H) ..................................................................... 38
8.5
SET RAM Y - ADDRESS START / END POSITION (45H) ..................................................................... 38
8.6
SET RAM ADDRESS COUNTER (4EH-4FH) ...................................................................................... 38
9
OPERATION FLOW AND CODE SEQUENCE ...................................................................... 39
9.1
GENERAL OPERATION FLOW TO DRIVE DISPLAY PANEL ..................................................................... 39
10 ABSOLUTE MAXIMUM RATING ........................................................................................... 40
11 ELECTRICAL CHARACTERISTICS ...................................................................................... 40
12 AC CHARACTERISTICS ........................................................................................................ 42
12.1
SERIAL PERIPHERAL INTERFACE ..................................................................................................... 42
13 APPLICATION CIRCUIT ........................................................................................................ 43
14 PACKAGE INFORMATION .................................................................................................... 44
14.1
DIE TRAY DIMENSIONS FOR SSD1680Z ......................................................................................... 44
14.2
DIE TRAY DIMENSIONS FOR SSD1680Z8 ....................................................................................... 45

<!-- Page 4 -->

SSD1680
Rev 0.14
P 4/46
Jun 2019
Solomon Systech
TABLES
TABLE 3-1 : ORDERING INFORMATION .............................................................................................................. 6
TABLE 5-1: POWER SUPPLY PINS .................................................................................................................... 7
TABLE 5-2: INTERFACE LOGIC PINS .................................................................................................................. 8
TABLE 5-3: ANALOG PINS ................................................................................................................................ 9
TABLE 5-4: DRIVER OUTPUT PINS .................................................................................................................... 9
TABLE 5-5: MISCELLANEOUS PINS ................................................................................................................... 9
TABLE 6-1 : INTERFACE PINS ASSIGNMENT UNDER DIFFERENT MCU INTERFACE ............................................... 10
TABLE 6-2 : CONTROL PINS STATUS OF 4-WIRE SPI ........................................................................................ 10
TABLE 6-3 : CONTROL PINS STATUS OF 3-WIRE SPI ........................................................................................ 11
TABLE 6-4 : RAM BIT AND LUT MAPPING FOR 3-COLOR DISPLAY ...................................................................... 13
TABLE 6-5 : RAM BIT AND LUT MAPPING FOR BLACK/WHITE DISPLAY ............................................................... 13
TABLE 6-6 : VS[NX-LUTM] SETTINGS FOR SOURCE VOLTAGE AND VCOM VOLTAGE ......................................... 14
TABLE 6-7 : EXAMPLE OF 12-BIT BINARY TEMPERATURE SETTINGS FOR TEMPERATURE RANGES ........................ 16
TABLE 6-8 : EXAMPLE OF WAVEFORM SETTINGS SELECTION BASED ON TEMPERATURE RANGES. ........................ 17
TABLE 7-1: COMMAND TABLE ........................................................................................................................ 20
TABLE 10-1 : MAXIMUM RATINGS ................................................................................................................... 40
TABLE 11-1: DC CHARACTERISTICS ............................................................................................................... 40
TABLE 11-2: REGULATORS CHARACTERISTICS ............................................................................................... 41
TABLE 12-1 : SERIAL PERIPHERAL INTERFACE TIMING CHARACTERISTICS ........................................................ 42
TABLE 13-1: COMPONENT LIST FOR SSD1680 APPLICATION CIRCUIT ............................................................... 43
FIGURES
FIGURE 4-1 : SSD1680 BLOCK DIAGRAM ......................................................................................................... 6
FIGURE 6-1 : WRITE PROCEDURE IN 4-WIRE SPI MODE ................................................................................... 10
FIGURE 6-2 : READ PROCEDURE IN 4-WIRE SPI MODE ..................................................................................... 11
FIGURE 6-3 : WRITE PROCEDURE IN 3-WIRE SPI ............................................................................................. 11
FIGURE 6-4 : READ PROCEDURE IN 3-WIRE SPI MODE ..................................................................................... 12
FIGURE 6-5 : GATE WAVEFORM AND PROGRAMMABLE SOURCE AND VCOM WAVEFORM ILLUSTRATION .............. 13
FIGURE 6-6 : WAVEFORM SETTING MAPPING .................................................................................................. 15
FIGURE 6-7 : THE WAVEFORM SETTING MAPPING IN OTP FOR WAVEFORM SETTING AND TEMPERATURE RANGE . 18
FIGURE 6-8 : FORMAT OF TEMPERATURE RANGE (TR) IN OTP ........................................................................ 18
FIGURE 8-1: OUTPUT PIN ASSIGNMENT ON DIFFERENT SCAN MODE SETTING .................................................... 35
FIGURE 8-2: EXAMPLE OF SET DISPLAY START LINE WITH NO REMAPPING ....................................................... 36
FIGURE 9-1: OPERATION FLOW TO DRIVE DISPLAY PANEL ................................................................................ 39
FIGURE 12-1: SPI TIMING DIAGRAM ................................................................................................................ 42
FIGURE 13-1: SCHEMATIC OF SSD1680 APPLICATION CIRCUIT ........................................................................ 43
FIGURE 14-1 : SSD1680Z DIE TRAY INFORMATION (UNIT: MM) ......................................................................... 44
FIGURE 14-2 : SSD1680Z8 DIE TRAY INFORMATION (UNIT: MM) ....................................................................... 45

<!-- Page 5 -->

SSD1680
Rev 0.14
P 5/46
Jun 2019
Solomon Systech
1
GENERAL DESCRIPTION
SSD1680 is an Active Matrix EPD display driver with controller for Red/Black/White EPD displays.
It consists of 176 source outputs, 296 gate outputs, 1 VCOM and 1VBD (for border), which can support displays
with resolution up to 176x 296. In addition, SSD1680 has a cascade mode which provides two-chip solutions for
displays with higher resolution.
In the SSD1680, data and commands are sent from MCU through hardware selectable serial peripheral interface.
It has embedded booster, regulator and oscillator which is suitable for EPD display applications.
2
FEATURES
•
Design for dot matrix type active matrix EPD display, support Red/Black/White color
•
Resolution: 176 source outputs, 296 gate outputs, 1 VCOM and 1VBD (for border)
•
Power supply:
•
VCI:
2.2 to 3.7V
•
VDDIO: Connect to VCI
•
VDD:
1.8V, regulate from VCI supply
•
On chip display RAM
•
Mono B/W: 176x296 bits
•
Mono Red: 176x296 bits
•
On-chip booster and regulator for generating VCOM, Gate and Source driving voltage
•
Gate driving output voltage: 2-level outputs (VGH, VGL), Max 40Vp-p
•
VGH: 10V to 20V (Voltage adjustment step: 500mV)
•
VGL: -VGH (Voltage adjustment step: 500mV)
•
Source / VBD driving output voltage: 4-levels outputs (VSH1, VSH2, VSS and VSL)
•
VSH1/VSH2: 2.4V to 17V (Voltage adjustment step: 100mV for 2.4V to 8.8V, 200mV for 8.8V to
17V)
•
VSL: -5V to -17V (Voltage adjustment step: 500mV)
•
VCOM output voltage
•
DCVCOM: -3V to -0.2V in 100mV resolution
•
ACVCOM: 3-level outputs (VSH1+DCVCOM, DCVCOM, VSL+DCVCOM)
•
On-chip oscillator, adjustable frame rate from 25Hz to 200Hz
•
Programmable output Waveform Settings:
•
Individual setting of 5 LUT [LUT0~4]
-
VS: 2-bit per 4 phases
•
Common setting of 5 LUT
-
48 phases (4 phases/group, 12 groups with repeat and state repeat function)
-
TP: Max. 255 frame/phase
-
RP: 1 to 256 times for repeat count
-
SR: 1 to 256 times for state repeat count; state repeat count for phase A,B and 1 state
repeat count for phase C,D
-
FR: Selective Frame Rate for each group
-
XON: All Gate On Selection for each phase A,B and phase C,D
•
Embedded OTP to store the waveform settings and parameters:
•
36 sets of Waveform Settings (WS) including
-
waveform look up table (LUT),
-
Gate/Source voltage, VCOM value
-
Option for LUT end
•
36 sets of Temperature Range (TR)
•
Display mode selection
•
4-byte waveform version
•
10-byte User ID
•
Embedded OTP to store the init code setting
•
External or internal generated voltage for burning OTP
•
Built-in CRC checking method for RAM content and WS & TR in OTP
•
Panel break diagnostic
•
VCI low voltage detection
•
Driving voltage ready detection
•
Support display partial update

<!-- Page 6 -->

SSD1680
Rev 0.14
P 6/46
Jun 2019
Solomon Systech
•
Auto write RAM command for regular patterns
•
Internal Temperature Sensor of +/-2degC accuracy from -25degC to 50degC
•
I2C single master interface to communicate with external temperature sensor
•
MCU interface: 4-wire or 3-wire Serial peripheral interface (maximum SPI write speed 20MHz)
•
Cascade mode to support displays with higher resolution
•
Available in COG package
3
ORDERING INFORMATION
Table 3-1 : Ordering Information
Ordering Part Number
Package Form
Remark
SSD1680Z
Gold Bump Die
Bump Face Up
On Waffle pack
Die thickness: 300um
Bump height: 12um
SSD1680Z8
Gold Bump Die
Bump Face Down
On Waffle pack
Die thickness: 300um
Bump height: 12um
4
BLOCK DIAGRAM
Figure 4-1 : SSD1680 Block Diagram

<!-- Page 7 -->

SSD1680
Rev 0.14
P 7/46
Jun 2019
Solomon Systech
5
PIN DESCRIPTION
Key:
I = Input
O =Output
IO = Bi-directional (input/output)
P = Power pin
C = Capacitor Pin
NC = Not Connected
Table 5-1: Power Supply Pins
Name
Type
Connect to
Function
Description
When not
in use
VCI
P
Power
Supply
Power Supply
Power input pin for the chip.
-
VCIA
P
Power
Supply
Power Supply
Power input pin for the chip.
- Connect to VCI in the application circuit.
-
VDDIO
P
Power
Supply
Power for
interface logic
pins
Power input pin for the Interface.
- Connect to VCI in the application circuit.
-
VDD
P
Capacitor
Regulator
output
Core logic power pin
VDD can be regulated internally from VCI.
- For the single chip application, a capacitor
should be connected between VDD and VSS
under all circumstances.
- For the cascade mode application, a capacitor
should be connected between VDD and VSS in
the master chip under all circumstances.  For the
slave chip, the capacitor is not necessary as
VDD will be supplied from the cascade master
chip externally.
-
VSS
P
VSS
GND
Ground (Digital).
-
VSSA
P
VSS
GND
Ground (Analog)
- Connect to VSS in the application circuit.
-
VSSBG
P
VSS
GND
Ground (Reference) pin.
- Connect to VSS in the application circuit.
-
VSSGS
P
VSS
GND
Ground (Output) pin.
- Connect to VSS in the application circuit.
-
VPP
P
Power
Supply
OTP power
Power Supply for OTP Programming.
Open

<!-- Page 8 -->

SSD1680
Rev 0.14
P 8/46
Jun 2019
Solomon Systech
Table 5-2: Interface Logic Pins
Name
Type
Connect to
Function
Description
When not
in use
SCL
I
MPU
Data Bus
This pin is serial clock pin for interface.
Refer to MCU interface in Section 6.1.
-
SDA
I/O
MPU
Data Bus
This pin is serial data pin for interface.
Refer to MCU interface in Section 6.1.
-
CS#
I
MPU
Logic Control
This pin is the chip select input connecting to the
MCU. Refer to MCU interface in Section 6.1.
VDDIO or
VSS
D/C#
I
MPU
Logic Control
This pin is Data/Command control pin connecting
to the MCU. Refer to MCU interface in Section 6.1.
VDDIO or
VSS
RES#
I
MPU
System Reset
This pin is reset signal input.
Active Low.
-
BUSY
O
MPU
Device Busy
Signal
This pin is Busy state output pin.
When Busy is High, the operation of the chip
should not be interrupted, and command should
not be sent.
For example., The chip would output Busy pin as
High when
- Outputting display waveform; or
- Programming with OTP
- Communicating with digital temperature sensor
In the cascade mode, the BUSY pin of the slave
chip should be left open.
Open
M/S#
I
VDDIO/VSS
Cascade
Mode
Selection
This pin is Master and Slave selection pin.
- For the single chip application, the M/S# pin
should be connected to VDDIO.
- In the cascade mode:
For Master Chip, the M/S# pin should be
connected to VDDIO.
For Slave Chip, the M/S# pin should be
connected to VSS.  The oscillator, booster and
regulator circuits of the slave chip will be
disabled.  The corresponding pins including CL,
VDD, VDDIO, VGH, VGL, VSH1, VSH2, VSL
and VCOM must be connected to the master
chip.
-
CL
I/O
NC
Clock signal
This pin is the clock signal pin.
- For the single chip application, the CL pin should
be left open.
- In the cascade mode, the CL pin of the slave
chip should be connected to the CL pin of the
master chip.
Open
BS1
I
VDDIO/VSS
MCU Interface
Mode
Selection
This pin is for selecting 3-wire or 4-wire SPI bus.
BS1
MCU Interface
L
4-wire SPI
H
3-wire SPI (9-bit SPI)
-
TSDA
I/O
Temperature
sensor SDA
Interface to
Digital Temp.
Sensor
This pin is I2C Interface to digital temperature
sensor Data pin.
External pull up resistor is required when
connecting to I2C slave.
Open
TSCL
O
Temperature
sensor SCL
Interface to
Digital Temp.
Sensor
This pin is I2C Interface to digital temperature
sensor Clock pin.
External pull up resistor is required when
connecting to I2C slave.
Open

<!-- Page 9 -->

SSD1680
Rev 0.14
P 9/46
Jun 2019
Solomon Systech
Table 5-3: Analog Pins
Name
Type
Connect to
Function
Description
When not
in use
GDR
O
POWER
MOSFET
Driver
Control
VGH, VGL
Generation
This pin is N-Channel MOSFET gate drive control
pin.
-
RESE
I
Booster
Control
Input
This pin is Current sense input pin for the control
Loop.
-
VGH
C
Stabilizing
capacitor
This pin is Positive Gate driving voltage.
Connect a stabilizing capacitor between VGH and
VSS in the application circuit.
-
VGL
C
Stabilizing
capacitor
This pin is Negative Gate driving voltage.
Connect a stabilizing capacitor between VGL and
VSS in the application circuit.
-
VSH1
C
Stabilizing
capacitor
VSH1, VSH2,
VSL
Generation
This pin is Positive Source driving voltage, VSH1
Connect a stabilizing capacitor between VSH1 and
VSS in the application circuit.
-
VSH2
C
Stabilizing
capacitor
This pin is Positive Source driving voltage, VSH2
Connect a stabilizing capacitor between VSH2 and
VSS in the application circuit.
VSL
C
Stabilizing
capacitor
This pin is Negative Source driving voltage.
Connect a stabilizing capacitor between VSL and
VSS in the application circuit.
-
VCOM
C
Panel/
Stabilizing
capacitor
VCOM
Generation
This pins is VCOM driving voltage
Connect a stabilizing capacitor between VCOM
and VSS in the application circuit.
-
Table 5-4: Driver Output Pins
Name
Type
Connect to
Function
Description
When not
in use
S [175:0]
O
Panel
Source driving
signal
Source output pin.
Open
G [295:0]
O
Panel
Gate driving
signal
Gate output pin.
Open
VBD
O
Panel
Border driving
signal
Border output pin.
Open
Table 5-5: Miscellaneous Pins
Name
Type
Connect to
Function
Description
When not
in use
NC
NC
NC
Not Connected
This is dummy pin. It should not be connected with
other NC pins.
Open
RSV
NC
NC
Reserved
This is a reserved pin and should be kept open.
Open
TPA, TPB,
TPC, TPD,
TPF, FB
NC
NC
Reserved for
Testing
Reserved pins.
- Keep open.
- Do not connect to other NC pins and test pins
including TPA, TPB, TPC, TPD, TPE, TPF, TIN
and FB.
Open
TIN
I
NC
Reserved for
Testing
This is a reserved pin and should be kept open.
Open
TPE
O
NC
Reserved for
Testing
This is a reserved pin and should be kept open.
Open

<!-- Page 10 -->

SSD1680
Rev 0.14
P 10/46
Jun 2019
Solomon Systech
6
Functional Block Description
6.1 MCU Interface
6.1.1 MCU Interface selection
The SSD1680 can support 3-wire/4-wire serial peripheral. MCU interface is pin selectable by BS1
shown in Table 6-1.
Table 6-1 : Interface pins assignment under different MCU interface
Pin Name
MCU Interface
BS1
RES#
CS#
D/C#
SCL
SDA
4-wire serial peripheral
interface (SPI)
L
RES#
CS#
DC#
SCL
SDA
3-wire serial peripheral
interface (SPI) – 9 bits SPI
H
RES#
CS#
L
SCL
SDA
Note
(1) L is connected to VSS and H is connected to VDDIO
6.1.2 MCU Serial Interface (4-wire SPI)
The 4-wire SPI consists of serial clock SCL, serial data SDA, D/C# and CS#. The control pins status in
4-wire SPI in writing command/data is shown in Table 6-2 and the write procedure 4-wire SPI is shown
in Table 6-2
Table 6-2 : Control pins status of 4-wire SPI
Function
SCL pin
SDA pin
D/C# pin
CS# pin
Write command
↑
Command bit
L
L
Write data
↑
Data bit
H
L
Note:
(1) L is connected to VSS and H is connected to VDDIO
(2) ↑ stands for rising edge of signal
(3) SDA (Write Mode) is shifted into an 8-bit shift register on every rising edge of SCL in the order of
D7, D6, ... D0. The level of D/C# should be kept over the whole byte. The data byte in the shift
register is written to the Graphic Display Data RAM (RAM)/Data Byte register or command Byte
register according to D/C# pin.
Figure 6-1 : Write procedure in 4-wire SPI mode

<!-- Page 11 -->

SSD1680
Rev 0.14
P 11/46
Jun 2019
Solomon Systech
In the read operation (Command 0x1B, 0x27, 0x2D, 0x2E, 0x2F, 0x35). After CS# is pulled low, the
first byte sent is command byte, D/C# is pulled low.  After command byte sent, the following byte(s)
read are data byte(s), so D/C# bit is then pulled high.  An 8-bit data will be shifted out on every clock
falling edge.  The serial data SDA bit shifting sequence is D7, D6, to D0 bit. Figure 6-2 shows the read
procedure in 4-wire SPI.
Figure 6-2 : Read procedure in 4-wire SPI mode
6.1.3 MCU Serial Peripheral Interface (3-wire SPI)
The 3-wire SPI consists of serial clock SCL, serial data SDA and CS#. The operation is similar to 4-
wire SPI while D/C# pin is not used and it must be tied to LOW.  The control pins status in 3-wire SPI
is shown in Table 6-3.
In the write operation, a 9-bit data will be shifted into the shift register on every clock rising edge.  The
bit shifting sequence is D/C# bit, D7 bit, D6 bit to D0 bit.  The first bit is D/C# bit which determines the
following byte is command or data.  When D/C# bit is 0, the following byte is command.  When D/C#
bit is 1, the following byte is data. Table 6-3 shows the write procedure in 3-wire SPI
Table 6-3 : Control pins status of 3-wire SPI
Function
SCL pin
SDA pin
D/C# pin
CS# pin
Write command
↑
Command bit
Tie LOW
L
Write data
↑
Data bit
Tie LOW
L
Note:
(1)
L is connected to VSS and H is connected to VDDIO
(2)
↑ stands for rising edge of signal
Figure 6-3 : Write procedure in 3-wire SPI
SCL
SDA
(Read Mode)
SDA
(Write Mode)
D7
D6
D5
D4
D3
D2
D1
D0
D/C#
CS#
D7
D0

<!-- Page 12 -->

SSD1680
Rev 0.14
P 12/46
Jun 2019
Solomon Systech
In the read operation (Register 0x1B, 0x27, 0x2D, 0x2E, 0x2F, 0x35).  SDA data are transferred in the
unit of 9 bits. After CS# pull low, the first byte is command byte, the D/C# bit is as 0 and following with
the register byte.  After command byte send, the following byte(s) are data byte(s), with D/C# bit is 1.
After D/C# bit sending from MCU, an 8-bit data will be shifted out on every clock falling edge.  The serial
data SDA bit shifting sequence is D7, D6, to D0 bit. Figure 6-4 shows the read procedure in 3-wire SPI.
Figure 6-4 : Read procedure in 3-wire SPI mode
6.2 OSCILLATOR
The oscillator module generates the clock reference for waveform timing and analog operations.
6.3 BOOSTER & REGULATOR
A voltage generation system is included in the driver. It provides all necessary driving voltages required for an
AMEPD panel including VGH, VGL, VSH1, VSH2, VSL and VCOM.  External application circuit is needed to make
the on-chip booster & regulator circuit work properly.
6.4 VCOM SENSING
This functional block provides the scheme to select the optimal VCOM DC level. The sensed value can be
programmed into OTP.
The flow of VCOM sensing:
•
Active Gate is scanning during the VCOM sense Period.
•
Source are VSS.
•
VCOM pin used for sensing.
•
During Sensing period, BUSY is high.
•
After Sensing, Active Gate return to non-select stage.
C3
C2
GDR
C5
VSH1
VSH1
Generator
C4
VGL
C7
VSL
VSL
Generator
C8
VCOM
VCOM
Generator
C1
VDD
VDDIO
VCI
VSS
C0
RESE
VGH
L1
Q1
R1
D1
D2
D3
VGH & VGL
Generator
C6
VSH2
VSH2
Generator

<!-- Page 13 -->

SSD1680
Rev 0.14
P 13/46
Jun 2019
Solomon Systech
6.5 RAM
The On chip display RAM is holding the image data.
1 set of RAM is built for Mono B/W. The RAM size is 176x296 bits.
1 set of RAM is built for Mono Red. The RAM size is 176x296 bits.
Table 6-4 : RAM bit and LUT mapping for 3-color display
Data bit in R RAM
Data bit in B/W RAM
Image Color
LUT
0
0
Black
LUT 0 for driving Black
0
1
White
LUT 1 for driving White
1
0
Red
LUT 2 for driving Red
1
1
Red
LUT 3 = LUT2
Table 6-5 : RAM bit and LUT mapping for black/white display
Data bit in R RAM
Data bit in B/W RAM
Image Color
LUT
0
0
Black
LUT 0 for driving Black
0
1
White
LUT 1 for driving White
1
0
Black
LUT 2 = LUT0
1
1
White
LUT 3 = LUT1
6.6 Programmable Waveform for Gate, Source and VCOM
Figure 6-5 : Gate waveform and Programmable Source and VCOM waveform illustration
SR:repeat times between two Sub Groups from 1 to 256
RP:repeat times for Group from 1 to 256
RP[0]
RP[1]
RP[11]
SR[0AB]
SR[0CD]
SR[1AB]
SR[1CD]
SR[11AB]
SR[11CD]
VSH1
VSH2
VSS
……..
VSL
Option
for LUT
d
  Sub group C&D
group0
group1
group11
phase0A
phase0B
phase0C
phase0D
phase1A phase1B phase1C phase1D
phase11A phase11B phase11Cphase11D
  Sub group A&B
Source
Signal
end
VGH
……..
VGL
…
TP[0A]
TP[0B]
TP[0C]
TP[0D]
TP[1A]
TP[1B]
TP[1C]
TP[1D]
TP[11A]
TP[11B]
TP[11C]
…
…
…
…
…
TP[11D]
…
…
…
…
…
…
…
…
…
…
…
…
…
…
…
…
…
…
Gate
Signal
…
…
…
…
…
…
XON[11CD]
XON[0AB]
XON[0CD]
XON[1AB]
XON[1CD]
XON[11AB]
TP: time of phase length from 0 to 255* frames
0indicates phase skipped
XON: All Gate On selection for each nAB or nCD.
FR: Frame frequency selection for each group.
EOPT: Option for LUT end
FR[0]
FR[1]
FR[11]

<!-- Page 14 -->

SSD1680
Rev 0.14
P 14/46
Jun 2019
Solomon Systech
In the programmable waveform for Source and VCOM, there are 12 groups (Group0 to Group11) and each group
has 4 phases (Phase A to Phase D) and 2 state repeats (Phase A and B, Phase C and D).  Totally, there are 48
phases.  In addition, in each phase, the phase length (TP[nX]) can be set by number of frame from 0 to 255
frames.  Also, each group can be repeated with repeat counting number (RP[n]) from 1 to 256 times; each AB /
CD phases can be repeated with state repeat counting number (SR[nAB]/SR[nCD]) from 1 to 256 times.  For the
voltage, there is four levels for Source voltage (VSS, VSH1, VSH2, VSL) and three levels for VCOM voltage
(DCVCOM, VSH1+DCVCOM, VSL+DCVOM).
The description of each parameter is as follows.
1)
TP[nX] represents the phase length set by the number of frame.
•
The range of TP[nX] is from 0 to 255.
•
n represents the Group number from 0 to 11; X represents the phase number from A to D.
•
When TP[nX] = 0, the phase is skipped.  When TP[nX] = 1, the phase is 1 frame, and so on.  The
maximum phase length is 255 frame.
2)
RP[n] represents the repeat counting number for the Group.
•
The range of RP[n] is from 0 to 255.
•
n represents the Group number from 0 to 11.
•
RP[n] = 0 indicates that the repeat times =1, RP[n] = 1 indicates that the repeat times = 2, and so on.
The maximum repeat times is 256.
3)
SR[nAB] and SR[nCD] represent the state repeat counting number for Phase A & B and Phase C & D
respectively.
•
The range of SR[nXY] is from 0 to 255.
•
n represents the Group number from 0 to 11.
•
SR[nXY] = 0 indicates that the repeat times =1, SR[nXY] = 1 indicates that the repeat times = 2, and so
on.  The maximum repeat times is 256.
4)
VS[nX-LUTm] represents Source and VCOM voltage level which is used in each phase.  Table 6-6
shows the voltage settings for source voltage and VCOM voltage.
•
n represents the Group number from 0 to 11.
•
m represents the LUT number from 0-4.
Table 6-6 : VS[nX-LUTm] settings for Source voltage and VCOM voltage
VS[nX-LUTm]
Source voltage
VCOM voltage
00
VSS
DCVCOM
01
VSH1
VSH1 + DCVCOM
10
VSL
VSL + DCVCOM
11
VSH2
N/A
5)
FR[n] indicates the frame rate of group n
•
The range of FR [n] is from 0 to 7.
•
n represents the Group number from 0 to 11.
6)
XON[nAB] and XON[nCD], indicates the gate scan selection.
•
n represents the Group number from 0 to 11.
•
XON[nXY] = 0 indicates Normal gate scan in Phase[nX] & Phase[nY].
•
XON[nXY] = 1 indicates All gate on, that Gate keeps High until the phase for normal gate scan, in
Phase[nX] & Phase[nY].

<!-- Page 15 -->

SSD1680
Rev 0.14
P 15/46
Jun 2019
Solomon Systech
6.7 WAVEFORM SETTING
As described in Section 6.6, parameters VS[nX-LUTm], TP[nX], RP[n], SR[nXY], FR[n] and XON[nXY]  are used
to define the driving waveform. In the SSD1680, there are 159 bytes in the waveform setting to store LUT0, LUT1,
LUT2, LUT3 and LUT4, gate voltage, source voltage and frame rate.  The waveform LUT of a particular
temperature range can be loaded from OTP or written by MCU.
•
WS byte 0~152, the content of VS[nX-LUTm], TP[nX], RP[n], SR[nXY], FR[n] and XON[nXY]  are defined
by Register 0x32
•
WS byte 153, the content of Option for LUT end, is the parameter belonging to Register 0x3F.
•
WS byte 154, the content of gate level, is the parameter defined by Register 0x03.
•
WS byte 155~157, the content of source level, is the parameter defined by Register 0x04.
•
WS byte 158, the content of VCOM level, is the parameter defined by Register 0x2C.
The SSD1680 waveform setting is shown in Figure 6-6 : Waveform Setting mapping
Figure 6-6 : Waveform Setting mapping
addr.
D7
D6
D5
D4
D3
D2
D1
D0
addr.
D7
D6
D5
D4
D3
D2
D1
D0
0
81
1
82
2
83
3
84
4
85
5
86
6
87
7
88
8
89
9
90
10
91
11
92
12
93
13
94
14
95
15
96
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
XON[0AB]
XON[0CD]
XON[1AB]
XON[1CD]
XON[2AB]
XON[2CD]
XON[3AB]
XON[3CD]
70
151
XON[4AB]
XON[4CD]
XON[5AB]
XON[5CD]
XON[6AB]
XON[6CD]
XON[7AB]
XON[7CD]
71
152
XON[8AB]
XON[8CD]
XON[9AB]
XON[9CD] XON[10AB] XON[10CD] XON[11AB] XON[11CD]
72
153
73
154
74
155
75
156
76
157
77
158
78
79
80
EOPT
TP[11D]
SR[11CD]
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
VS[4C-L0]
VS[4D-L0]
RP[0]
VS[5A-L0]
VS[5B-L0]
VS[5C-L0]
VS[5D-L0]
VS[3A-L0]
VS[3B-L0]
VS[3C-L0]
VS[3D-L0]
TP[0D]
VS[4A-L0]
VS[4B-L0]
VS[1A-L0]
VS[1B-L0]
VS[1C-L0]
VS[1D-L0]
TP[0B]
VS[2A-L0]
VS[0A-L0]
VS[0B-L0]
VS[0C-L0]
VS[0D-L0]
TP[0A]
VS[2B-L0]
VS[2C-L0]
VS[2D-L0]
TP[0C]

<!-- Page 16 -->

SSD1680
Rev 0.14
P 16/46
Jun 2019
Solomon Systech
6.8 Temperature Searching
The SSD1680 has internal temperature sensor to detect the environment temperature or can communicate with
the external temperature sensor by I2C single master interface or can communicate with the external MCU to get
the temperature value through SPI.  In the SSD1680, there is a dedicated format for the temperature value so
that the driver IC can understand it.  The format of temperature value is described in Section 6.8.3.
6.8.1 Internal Temperature Sensor
The internal temperature sensor can be selected by command register. The accuracy of it is ±2degC from -
25degC to 50degC.
6.8.2 External Temperature Sensor I2C Single Master Interface
The driver IC can communicate with the external temperature sensor through I2C single master interface (TSDA
and TSCL). TSDA will be SDA and TSCL will be SCL. TSDA and TSCL are required to connect with external pull-
up resistor. Temperature register value of external temperature sensor can be read by command register.
6.8.3 Format of temperature value
The temperature value is defined by 12-bit binary.  The rules are shown as below.
•
If the Temperature value MSByte bit D11 = 0, then
the temperature is positive and value (DegC) = + (Temperature value) / 16
•
If the Temperature value MSByte bit D11 = 1, then
the temperature is negative and value (DegC) = - (2’s complement of Temperature value) / 16
Table 6-7 shows some examples of 12-bit binary temperature value:
Table 6-7 : Example of 12-bit binary temperature settings for temperature ranges
12-bit binary
(2's complement)
Hexadecimal
 Value
TR Value
[DegC]
0111 1111 1111
7FF
128
0111 1111 1111
7FF
127.9
0110 0100 0000
640
100
0101 0000 0000
500
80
0100 1011 0000
4B0
75
0011 0010 0000
320
50
0001 1001 0000
190
25
0000 0000 0100
004
0.25
0000 0000 0000
000
0
1111 1111 1100
FFC
-0.25
1110 0111 0000
E70
-25
1100 1001 0000
C90
-55

<!-- Page 17 -->

SSD1680
Rev 0.14
P 17/46
Jun 2019
Solomon Systech
6.9 Waveform Setting searching mechanism
As mentioned in Section 6.7, the SSD1680 OTP can store waveform setting and temperature range.  If waveform
setting and temperature range are programmed in OTP memory, corresponding waveform LUT can be selected
according to the sensed temperature to drive the display. The Waveform Setting searching mechanism by driver
IC is as follows.
1)
Read temperature value by command register in the format of 12-bit binary.
2)
According to read temperature and display mode selection, search LUT in OTP from TR0 to TR35 in
sequence.  The last match will be selected, then, the corresponding WS will be loaded in the LUT register
to drive the display.
Remark: Waveform LUT selection criteria is “Lower temperature bound < Sensed temperature ≤ Upper
temperature bound”.
Table 6-8 shows an example for the waveform LUT searching from OTP:
• If the read temperature is 25degC, then, WS4 will be selected.
• If the read temperature is 34degC, then, WS7 will be selected.  Although 34degC is also in the temperature
range TR6, according to searching mechanism, the last match should be selected. Therefore, WS7 is
selected.
Table 6-8 : Example of waveform settings selection based on temperature ranges.
Waveform
LUT in OTP
Temperature
Range in OTP
TR Lower Limit
[Hex]
TR Upper Limit
[Hex]
Temperature range in OTP
WS0
TR0
800
050
-128 DegC < Temperature ≤  5 DegC
WS1
TR1
050
0A0
5 DegC < Temperature ≤  10DegC
WS2
TR2
0A0
0F0
10 DegC < Temperature ≤  15DegC
WS3
TR3
0F0
140
15 DegC < Temperature ≤  20DegC
WS4
TR4
140
190
20 DegC < Temperature ≤  25DegC
WS5
TR5
190
1E0
25 DegC < Temperature ≤  30DegC
WS6
TR6
1E0
230
30 DegC < Temperature ≤  35DegC
WS7
TR7
210
7FF
33 DegC < Temperature ≤  127.9DegC
Others
Others
000
000
Precaution:
Please ensure the temperature range covers whole range of application temperatures, display will not be
updated if no suitable temperature range matches the sensed temperature.

<!-- Page 18 -->

SSD1680
Rev 0.14
P 18/46
Jun 2019
Solomon Systech
6.10 One Time Programmable (OTP) Memory
In the SSD1680, there is an embedded OTP memory which is designed to store the waveform settings of different
temperature range and some variables/parameters.  The OTP memory can store 36 sets of waveform LUT settings
(WS), 36 sets of temperature range (TR), VCOM value, display mode selection, waveform version and user ID.
Figure 6 7 shows the address mapping of the 36 waveform setting (WS0 to WS35) and temperature range (TR0 to
TR35).
Figure 6-7 : The Waveform setting mapping in OTP for waveform setting and temperature range
6.11 The Format for Temperature Range (TR)
The format of TR Lower limit and Upper limit as shown in Figure 6-8 which temp_L[11:0] is the lower limit and
temp_H[11:0] is the upper limit of the temperature range.  There has 36sets of TR for waveform LUT searching.
D7
D6
D5
D4
D3
D2
D1
D0
temp_L[7:0]
temp_H[3:0]
temp_L[11:8]
temp_H[11:4]
Figure 6-8 : Format of Temperature Range (TR) in OTP
addr.
D7
D6
D5
D4
D3
D2
D1
D0
0
…
158
159
…
317
318
…
476
477
…
635
636
…
794
5406
…
5564
5565
…
5723
5724
5725
5726
5727
5728
5729
5730
5731
5732
5733
5734
5735
5736
5737
5738
5826
5827
5828
5829
5830
5831
…
TR35
TR34
…
TR4
TR3
TR2
TR1
TR0
WS35
WS34
WS4
WS3
WS2
WS1
WS0

<!-- Page 19 -->

SSD1680
Rev 0.14
P 19/46
Jun 2019
Solomon Systech
6.12 Cascade Mode
SSD1680 has a cascade mode that can cascade 2 chips to achieve the display resolution up to 352 (sources) x 296
(gates).  The pin M/S# is used to configure the chip.  When M/S# is connected to VDDIO, the chip is configured as a
master chip.  When M/S# is connected to VSS, the chip is configured as a slave chip.
When the chip is configured as a master chip, it will be the same as a single chip application, ie, all circuit blocks will be
worked as usual.  When the chip is configured as a slave chip, its oscillator and booster & regulator circuit will be disabled.
The oscillator clock and all booster voltages will be come from the master chip.  Therefore, the corresponding pins
including CL, VDD, VGH, VGL, VSH1, VSH2, VSL, VGL and VCOM must be connected to the master chip.
6.13 VCI Detection
The VCI detection function is used to detect the VCI level when it is lower than Vlow, threshold voltage set by register.
In SSD1680, there is a command to execute the VCI detection function.  When the VCI detection command is issued,
the VCI detection will be executed.  During the detection period, BUSY output is at high level.  BUSY output is at low
level when the detection is completed.  Then, user can issue the Status Bit Read command to check the status bit for
the result of VCI, which 0 is normal, 1 is VCI<Vlow.
6.14 HV Ready Detection
The HV Ready detection function is used to detect whether the analog block is ready.
In SSD1680, there is a command to execute the HV Ready detection function.  When the HV Ready detection command
is issued, the HV Ready will be executed.  During the detection period, BUSY output is at high level.  BUSY output is at
low level when the detection is completed.  Then, user can issue the Status Bit Read command to check the status bit
for the result of HV Ready, which 0 is normal, 1 indicate HV is not ready.

<!-- Page 20 -->

SSD1680
Rev 0.14
P 20/46
Jun 2019
Solomon Systech
7
COMMAND TABLE
Table 7-1: Command Table
Command Table
R/W# D/C# Hex
D7
D6
D5
D4
D3
D2
D1
D0 Command
Description
0
0
01
0
0
0
0
0
0
0
1
Driver Output control
Gate setting
A[8:0]= 127h [POR], 296 MUX
MUX Gate lines setting as (A[8:0] + 1).
B[2:0] = 000 [POR].
Gate scanning sequence and direction
B[2]: GD
Selects the 1st output Gate
GD=0 [POR],
G0 is the 1st gate output channel, gate
output sequence is G0,G1, G2, G3, …
GD=1,
G1 is the 1st gate output channel, gate
output sequence is G1, G0, G3, G2, …
B[1]: SM
Change scanning order of gate driver.
SM=0 [POR],
G0, G1, G2, G3…295 (left and right gate
interlaced)
SM=1,
G0, G2, G4  …G294, G1, G3,  …G295
B[0]: TB
TB = 0 [POR], scan from G0 to G295
TB = 1, scan from G295 to G0.
0
1
A7
A6
A5
A4
A3
A2
A1
A0
0
1
0
0
0
0
0
0
0
A8
0
1
0
0
0
0
0
B2
B1
B0
0
0
03
0
0
0
0
0
0
1
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
Gate Driving voltage
Control
Set Gate driving voltage
A[4:0] = 00h [POR]
VGH setting from 10V to 20V
A[4:0]
VGH
A[4:0]
VGH
00h
20
0Dh
15
03h
10
0Eh
15.5
04h
10.5
0Fh
16
05h
11
10h
16.5
06h
11.5
11h
17
07h
12
12h
17.5
08h
12.5
13h
18
07h
12
14h
18.5
08h
12.5
15h
19
09h
13
16h
19.5
0Ah
13.5
17h
20
0Bh
14
Other
NA
0Ch
14.5
0
1
0
0
0
A4
A3
A2
A1
A0

<!-- Page 21 -->

SSD1680
Rev 0.14
P 21/46
Jun 2019
Solomon Systech
Command Table
R/W# D/C# Hex
D7
D6
D5
D4
D3
D2
D1
D0 Command
Description
0
0
04
0
0
0
0
0
1
0
0
Source Driving voltage
Control
Set Source driving voltage
A[7:0] = 41h [POR], VSH1 at 15V
B[7:0] = A8h [POR], VSH2 at 5V.
C[7:0] = 32h [POR], VSL at -15V
Remark: VSH1>=VSH2
0
1
A7
A6
A5
A4
A3
A2
A1
A0
0
1
B7
B6
B5
B4
B3
B2
B1
B0
0
1
C7
C6
C5
C4
C3
C2
C1
C0
A[7]/B[7] = 1,
VSH1/VSH2 voltage setting from 2.4V
to 8.8V
A[7]/B[7] = 0,
VSH1/VSH2 voltage setting from 9V
to 17V
C[7] = 0,
VSL setting from -5V to -17V
0
0
08
0
0
0
0
1
0
0
0
Initial Code Setting
OTP Program
Program Initial Code Setting
The command required CLKEN=1.
Refer to Register 0x22 for detail.
BUSY pad will output high during
operation.
0
0
09
0
0
0
0
1
0
0
1
Write Register for Initial
Code Setting
Write Register for Initial Code Setting
Selection
A[7:0] ~ D[7:0]: Reserved
Details refer to Application Notes of Initial
Code Setting
0
1
A7
A6
A5
A4
A3
A2
A1
A0
0
1
B7
B6
B5
B4
B3
B2
B1
B0
0
1
C7
C6
C5
C4
C3
C2
C1
C0
0
1
D7
D6
D5
D4
D3
D2
D1
D0
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
Read Register for Initial
Code Setting
Read Register for Initial Code Setting
A/B[7:0]
VSH1/VSH2
A/B[7:0]
VSH1/VSH2
8Eh
2.4
AFh
5.7
8Fh
2.5
B0h
5.8
90h
2.6
B1h
5.9
91h
2.7
B2h
6
92h
2.8
B3h
6.1
93h
2.9
B4h
6.2
94h
3
B5h
6.3
95h
3.1
B6h
6.4
96h
3.2
B7h
6.5
97h
3.3
B8h
6.6
98h
3.4
B9h
6.7
99h
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
BAh
6.8
9Ah
3.6
BBh
6.9
9Bh
3.7
BCh
7
9Ch
3.8
BDh
7.1
9Dh
3.9
BEh
7.2
9Eh
4
BFh
7.3
9Fh
4.1
C0h
7.4
A0h
4.2
C1h
7.5
A1h
4.3
C2h
7.6
A2h
4.4
C3h
7.7
A3h
4.5
C4h
7.8
A4h
4.6
C5h
7.9
A5h
4.7
C6h
8
A6h
4.8
C7h
8.1
A7h
4.9
C8h
8.2
A8h
5
C9h
8.3
A9h
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
CAh
8.4
AAh
5.2
CBh
8.5
ABh
5.3
CCh
8.6
ACh
5.4
CDh
8.7
ADh
5.5
CEh
8.8
AEh
5.6
Other
NA
A/B[7:0]
VSH1/VSH2
A/B[7:0]
VSH1/VSH2
23h
9
3Ch
14
24h
9.2
3Dh
14.2
25h
9.4
3Eh
14.4
26h
9.6
3Fh
14.6
27h
9.8
40h
14.8
28h
10
41h
15
29h
10.2
42h
15.2
2Ah
10.4
43h
15.4
2Bh
10.6
44h
15.6
2Ch
10.8
45h
15.8
2Dh
11
46h
16
2Eh
11.2
47h
16.2
2Fh
11.4
48h
16.4
30h
11.6
49h
16.6
31h
11.8
4Ah
16.8
32h
12
4Bh
17
33h
12.2
Other
NA
34h
12.4
35h
12.6
36h
12.8
37h
13
38h
13.2
39h
13.4
3Ah
13.6
3Bh
13.8
C[7:0]
VSL
0Ah
0Ch
-5.5
0Eh
-6
10h
-6.5
12h
-7
14h
-7.5
16h
-8
18h
-8.5
1Ah
-9
1Ch
-9.5
1Eh
-10
20h
-10.5
22h
-11
24h
-11.5
26h
-12
28h
-12.5
2Ah
-13
2Ch
-13.5
2Eh
-14
30h
-14.5
32h
-15
34h
-15.5
36h
-16
38h
-16.5
3Ah
-17
Other
NA

<!-- Page 22 -->

SSD1680
Rev 0.14
P 22/46
Jun 2019
Solomon Systech
Command Table
R/W# D/C# Hex
D7
D6
D5
D4
D3
D2
D1
D0 Command
Description
0
0
0C
0
0
0
0
1
1
0
0
Booster Soft start
Control
Booster Enable with Phase 1, Phase 2 and Phase 3
for soft start current and duration setting.
A[7:0] -> Soft start setting for Phase1
= 8Bh [POR]
B[7:0] -> Soft start setting for Phase2
= 9Ch [POR]
C[7:0] -> Soft start setting for Phase3
= 96h [POR]
D[7:0] -> Duration setting
= 0Fh [POR]
 Bit Description of each byte:
 A[6:0] / B[6:0] / C[6:0]:
Bit[6:4]
Driving Strength
Selection
000
1(Weakest)
001
2
010
3
011
4
100
5
101
6
110
7
111
8(Strongest)
Bit[3:0]
Min Off Time Setting of GDR
[ Time unit ]
0000
~
0011
NA
0100
2.6
0101
3.2
0110
3.9
0111
4.6
1000
5.4
1001
6.3
1010
7.3
1011
8.4
1100
9.8
1101
11.5
1110
13.8
1111
16.5
 D[5:0]: duration setting of phase
D[5:4]: duration setting of phase 3
D[3:2]: duration setting of phase 2
D[1:0]: duration setting of phase 1
Bit[1:0]
Duration of Phase
[Approximation]
00
10ms
01
20ms
10
30ms
11
40ms
0
1
1
A6
A5
A4
A3
A2
A1
A0
0
1
1
B6
B5
B4
B3
B2
B1
B0
0
1
1
C6
C5
C4
C3
C2
C1
C0
0
1
0
0
D5
D4
D3
D2
D1
D0

<!-- Page 23 -->

SSD1680
Rev 0.14
P 23/46
Jun 2019
Solomon Systech
Command Table
R/W# D/C# Hex
D7
D6
D5
D4
D3
D2
D1
D0 Command
Description
0
0
10
0
0
0
1
0
0
0
0
Deep Sleep mode
Deep Sleep mode Control:
A[1:0] :
Description
00
Normal Mode [POR]
01
Enter Deep Sleep Mode 1
11
Enter Deep Sleep Mode 2
After this command initiated, the chip will
enter Deep Sleep Mode, BUSY pad will
keep output high.
Remark:
To Exit Deep Sleep mode, User required
to send HWRESET to the driver
0
1
0
0
0
0
0
0
A1
A0
0
0
11
0
0
0
1
0
0
0
1
Data Entry mode setting Define data entry sequence
A[2:0] = 011 [POR]
A [1:0] = ID[1:0]
Address automatic increment / decrement
setting
The setting of incrementing or
decrementing of the address counter can
be made independently in each upper and
lower bit of the address.
00 –Y decrement, X decrement,
01 –Y decrement, X increment,
10 –Y increment, X decrement,
11 –Y increment, X increment [POR]
A[2] = AM
Set the direction in which the address
counter is updated automatically after data
are written to the RAM.
AM= 0, the address counter is updated in
the X direction. [POR]
AM = 1, the address counter is updated in
the Y direction.
0
1
0
0
0
0
0
A2
A1
A0
0
0
12
0
0
0
1
0
0
1
0
SW RESET
It resets the commands and parameters to
their S/W Reset default values except
R10h-Deep Sleep Mode
During operation, BUSY pad will output
high.
Note: RAM are unaffected by this
command.

<!-- Page 24 -->

SSD1680
Rev 0.14
P 24/46
Jun 2019
Solomon Systech
Command Table
R/W# D/C# Hex
D7
D6
D5
D4
D3
D2
D1
D0 Command
Description
0
0
14
0
0
0
1
0
1
0
0
HV Ready Detection
HV ready detection
A[7:0] = 00h [POR]
The command required CLKEN=1 and
ANALOGEN=1.
Refer to Register 0x22 for detail.
After this command initiated, HV Ready
detection starts.
BUSY pad will output high during
detection.
The detection result can be read from the
Status Bit Read (Command 0x2F).
0
1
0
A6
A5
A4
0
A2
A1
A0
A[6:4]=n for cool down duration:
10ms x (n+1)
A[2:0]=m for number of Cool Down Loop
to detect.
The max HV ready duration is
10ms x (n+1) x (m)
HV ready detection will be trigger after
each cool down time. The detection will be
completed when HV is ready.
For 1 shot HV ready detection, A[7:0] can
be set as 00h.
0
0
15
0
0
0
1
0
1
0
1
VCI Detection
VCI Detection
A[2:0] = 100 [POR] , Detect level at 2.3V
A[2:0] : VCI level Detect
A[2:0]
VCI level
011
2.2V
100
2.3V
101
2.4V
110
2.5V
111
2.6V
Other
NA
The command required CLKEN=1 and
ANALOGEN=1
Refer to Register 0x22 for detail.
After this command initiated, VCI
detection starts.
BUSY pad will output high during
detection.
The detection result can be read from the
Status Bit Read (Command 0x2F).
0
1
0
0
0
0
0
A2
A1
A0
0
0
18
0
0
0
1
1
0
0
0
Temperature Sensor
Control
Temperature Sensor Selection
A[7:0] = 48h [POR], external temperatrure
sensor
A[7:0] = 80h Internal temperature sensor
0
1
A7
A6
A5
A4
A3
A2
A1
A0
0
0
1A
0
0
0
1
1
0
1
0
Temperature Sensor
Control (Write to
temperature register)
Write to temperature register.
A[11:0] = 7FFh [POR]
0
1
A11 A10
A9
A8
A7
A6
A5
A4
0
1
A3
A2
A1
A0
0
0
0
0
0
0
1B
0
0
0
1
1
0
1
1
Temperature Sensor
Control (Read from
temperature register)
Read from temperature register.
1
1
A11 A10
A9
A8
A7
A6
A5
A4
1
1
A3
A2
A1
A0
0
0
0
0

<!-- Page 25 -->

SSD1680
Rev 0.14
P 25/46
Jun 2019
Solomon Systech
Command Table
R/W# D/C# Hex
D7
D6
D5
D4
D3
D2
D1
D0 Command
Description
0
0
1C
0
0
0
1
1
1
0
0
Temperature Sensor
Control (Write Command
to External temperature
sensor)
Write Command to External temperature
sensor.
A[7:0] = 00h [POR],
B[7:0] = 00h [POR],
C[7:0] = 00h [POR],
A[7:6]
A[7:6]
Select no of byte to be sent
00
Address + pointer
01
Address + pointer + 1st parameter
10
Address + pointer + 1st parameter +
2nd pointer
11
Address
A[5:0] – Pointer Setting
B[7:0] – 1st parameter
C[7:0] – 2nd parameter
The command required CLKEN=1.
Refer to Register 0x22 for detail.
After this command initiated, Write
Command to external temperature sensor
starts. BUSY pad will output high during
operation.
0
1
A7
A6
A5
A4
A3
A2
A1
A0
0
1
B7
B6
B5
B4
B3
B2
B1
B0
0
1
C7
C6
C5
C4
C3
C2
C1
C0
0
0
20
0
0
1
0
0
0
0
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
Master Activation
Activate Display Update Sequence
The Display Update Sequence Option is
located at R22h.
BUSY pad will output high during
operation. User should not interrupt this
operation to avoid corruption of panel
images.
0
0
21
0
0
1
0
0
0
0
1
Display Update Control
1
RAM content option for Display Update
A[7:0] = 00h [POR]
B[7:0] = 00h [POR]
A[7:4] Red RAM option
0000
Normal
0100
Bypass RAM content as 0
1000
Inverse RAM content
A[3:0] BW RAM option
0000
Normal
0100
Bypass RAM content as 0
1000
Inverse RAM content
B[7] Source Output Mode
0
Available Source from S0 to S175
1
Available Source from S8 to S167
0
1
A7
A6
A5
A4
A3
A2
A1
A0
0
1
B7
0
0
0
0
0
0
0

<!-- Page 26 -->

SSD1680
Rev 0.14
P 26/46
Jun 2019
Solomon Systech
Command Table
R/W# D/C# Hex
D7
D6
D5
D4
D3
D2
D1
D0 Command
Description
0
0
22
0
0
1
0
0
0
1
0
Display Update
Control 2
Display Update Sequence Option:
Enable the stage for Master Activation
A[7:0]= FFh (POR)
Operating sequence
Parameter
(in Hex)
Enable clock signal
80
Disable clock signal
01
Enable clock signal
 Enable Analog
C0
Disable Analog
 Disable clock signal
03
Enable clock signal
 Load LUT with DISPLAY Mode 1
 Disable clock signal
91
Enable clock signal
 Load LUT with DISPLAY Mode 2
 Disable clock signal
99
Enable clock signal
 Load temperature value
 Load LUT with DISPLAY Mode 1
 Disable clock signal
B1
Enable clock signal
 Load temperature value
 Load LUT with DISPLAY Mode 2
 Disable clock signal
B9
Enable clock signal
 Enable Analog
 Display with DISPLAY Mode 1
 Disable Analog
 Disable OSC
C7
Enable clock signal
 Enable Analog
 Display with DISPLAY Mode 2
 Disable Analog
Disable OSC
CF
Enable clock signal
Enable Analog
 Load temperature value
 DISPLAY with DISPLAY Mode 1
 Disable Analog
 Disable OSC
F7
Enable clock signal
Enable Analog
 Load temperature value
 DISPLAY with DISPLAY Mode 2
 Disable Analog
 Disable OSC
FF
0
1
A7
A6
A5
A4
A3
A2
A1
A0
0
0
24
0
0
1
0
0
1
0
0
Write RAM (Black White)
/ RAM 0x24
After this command, data entries will be
written into the BW RAM until another
command is written. Address pointers will
advance accordingly
For Write pixel:
  Content of Write RAM(BW) = 1
For Black pixel:
 Content of Write RAM(BW) = 0

<!-- Page 27 -->

SSD1680
Rev 0.14
P 27/46
Jun 2019
Solomon Systech
Command Table
R/W# D/C# Hex
D7
D6
D5
D4
D3
D2
D1
D0 Command
Description
0
0
26
0
0
1
0
0
1
1
0
Write RAM (RED)
/ RAM 0x26
After this command, data entries will be
written into the RED RAM until another
command is written. Address pointers will
advance accordingly.
For Red pixel:
  Content of Write RAM(RED) = 1
For non-Red pixel [Black or White]:
 Content of Write RAM(RED) = 0
0
0
27
0
0
1
0
0
1
1
1
Read RAM
After this command, data read on the
MCU bus will fetch data from RAM.
According to parameter of Register 41h to
select reading RAM0x24/ RAM0x26, until
another command is written. Address
pointers will advance accordingly.
The 1st byte of data read is dummy data.
0
0
28
0
0
1
0
1
0
0
0
VCOM Sense
Enter VCOM sensing conditions and hold
for duration defined in 29h before reading
VCOM value.
The sensed VCOM voltage is stored in
register
The command required CLKEN=1 and
ANALOGEN=1
Refer to Register 0x22 for detail.
BUSY pad will output high during
operation.
0
0
29
0
0
1
0
1
0
0
1
VCOM Sense Duration
Stabling time between entering VCOM
sensing mode and reading acquired.
A[3:0] = 9h, duration = 10s.
VCOM sense duration = (A[3:0]+1) sec
0
1
0
1
0
0
A3
A2
A1
A0
0
0
2A
0
0
1
0
1
0
1
0
Program VCOM OTP
Program VCOM register into OTP
The command required CLKEN=1.
Refer to Register 0x22 for detail.
BUSY pad will output high during
operation.
0
0
2B
0
0
1
0
1
0
1
1
Write Register for VCOM
Control
This command is used to reduce glitch
when ACVCOM toggle. Two data bytes
D04h and D63h should be set for this
command.
0
1
0
0
0
0
0
1
0
0
0
1
0
1
1
0
0
0
1
1

<!-- Page 28 -->

SSD1680
Rev 0.14
P 28/46
Jun 2019
Solomon Systech
Command Table
R/W# D/C# Hex
D7
D6
D5
D4
D3
D2
D1
D0 Command
Description
0
0
2C
0
0
1
0
1
1
0
0
Write VCOM register
Write VCOM register from MCU interface
A[7:0] = 00h [POR]
A[7:0]
VCOM
A[7:0]
VCOM
08h
-0.2
44h
-1.7
0Ch
-0.3
48h
-1.8
10h
-0.4
4Ch
-1.9
14h
-0.5
50h
-2
18h
-0.6
54h
-2.1
1Ch
-0.7
58h
-2.2
20h
-0.8
5Ch
-2.3
24h
-0.9
60h
-2.4
28h
-1
64h
-2.5
2Ch
-1.1
68h
-2.6
30h
-1.2
6Ch
-2.7
34h
-1.3
70h
-2.8
38h
-1.4
74h
-2.9
3Ch
-1.5
78h
-3
40h
-1.6
Other
NA
0
1
A7
A6
A5
A4
A3
A2
A1
A0
0
0
2D
0
0
1
0
1
1
0
1
OTP Register Read for
Display Option
Read Register for Display Option:
A[7:0]: VCOM OTP Selection
(Command 0x37, Byte A)
B[7:0]: VCOM Register
(Command 0x2C)
C[7:0]~G[7:0]: Display Mode
(Command 0x37, Byte B to Byte F)
[5 bytes]
H[7:0]~K[7:0]: Waveform Version
(Command 0x37, Byte G to Byte J)
[4 bytes]
1
1
A7
A6
A5
A4
A3
A2
A1
A0
1
1
B7
B6
B5
B4
B3
B2
B1
B0
1
1
C7
C6
C5
C4
C3
C2
C1
C0
1
1
D7
D6
D5
D4
D3
D2
D1
D0
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
User ID Read
Read 10 Byte User ID  stored in OTP:
A[7:0]]~J[7:0]: UserID (R38, Byte A and
Byte J)  [10 bytes]
1
1
A7
A6
A5
A4
A3
A2
A1
A0
1
1
B7
B6
B5
B4
B3
B2
B1
B0
1
1
C7
C6
C5
C4
C3
C2
C1
C0
1
1
D7
D6
D5
D4
D3
D2
D1
D0
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

<!-- Page 29 -->

SSD1680
Rev 0.14
P 29/46
Jun 2019
Solomon Systech
Command Table
R/W# D/C# Hex
D7
D6
D5
D4
D3
D2
D1
D0 Command
Description
0
0
2F
0
0
1
0
1
1
1
1
Status Bit Read
Read IC status Bit [POR 0x01]
A[5]: HV Ready Detection flag [POR=0]
0: Ready
1: Not Ready
A[4]: VCI Detection flag [POR=0]
0: Normal
1: VCI lower than the Detect level
A[3]: [POR=0]
A[2]: Busy flag [POR=0]
0: Normal
1: BUSY
A[1:0]: Chip ID [POR=01]
Remark:
A[5] and A[4] status are not valid after
RESET, they need to be initiated by
command 0x14 and command 0x15
respectively.
1
1
0
0
A5
A4
0
0
A1
A0
0
0
30
0
0
1
1
0
0
0
0
Program WS OTP
Program OTP of Waveform Setting
The contents should be written into RAM
before sending this command.
The command required CLKEN=1.
Refer to Register 0x22 for detail.
BUSY pad will output high during
operation.
0
0
31
0
0
1
1
0
0
0
1
Load WS OTP
Load OTP of Waveform Setting
The command required CLKEN=1.
Refer to Register 0x22 for detail.
BUSY pad will output high during
operation.
0
0
32
0
0
1
1
0
0
1
0
Write LUT register
Write LUT register from MCU interface
[153 bytes], which contains the content of
VS[nX-LUTm], TP[nX], RP[n], SR[nXY],
FR[n] and XON[nXY]
Refer to Session 6.7 WAVEFORM
SETTING
0
1
A7
A6
A5
A4
A3
A2
A1
A0
0
1
B7
B6
B5
B4
B3
B2
B1
B0
0
1
:
:
:
:
:
:
:
:
0
1
.
..
.
.
.
.
.
.
0
0
34
0
0
1
1
0
1
0
0
CRC calculation
CRC calculation command
For details, please refer to SSD1680
application note.
BUSY pad will output high during
operation.
0
0
35
0
0
1
1
0
1
0
1
CRC Status Read
CRC Status Read
A[15:0] is the CRC read out value
1
1
A15 A14 A13 A12 A11 A10
A9
A8
1
1
A7
A6
A5
A4
A3
A2
A1
A0

<!-- Page 30 -->

SSD1680
Rev 0.14
P 30/46
Jun 2019
Solomon Systech
Command Table
R/W# D/C# Hex
D7
D6
D5
D4
D3
D2
D1
D0 Command
Description
0
0
36
0
0
1
1
0
1
1
0
Program OTP selection
Program OTP Selection according to the
OTP Selection Control [R37h and R38h]
The command required CLKEN=1.
Refer to Register 0x22 for detail.
BUSY pad will output high during
operation.
0
0
37
0
0
1
1
0
1
1
1
Write Register for Display
Option
Write Register for Display Option
A[7] Spare VCOM OTP selection
0: Default [POR]
1: Spare
B[7:0]  Display Mode for WS[7:0]
C[7:0]  Display Mode for WS[15:8]
D[7:0]  Display Mode for WS[23:16]
E[7:0]  Display Mode for WS[31:24]
F[3:0  Display Mode for WS[35:32]
0: Display Mode 1
1: Display Mode 2
F[6]:
PingPong for Display Mode 2
0: RAM Ping-Pong disable [POR]
1: RAM Ping-Pong enable
G[7:0]~J[7:0] module ID /waveform
version.
Remarks:
1) A[7:0]~J[7:0] can be stored in OTP
2) RAM Ping-Pong function is not support
for Display Mode 1
0
1
A7
0
0
0
0
0
0
0
0
1
B7
B6
B5
B4
B3
B2
B1
B0
0
1
C7
C6
C5
C4
C3
C2
C1
C0
0
1
D7
D6
D5
D4
D3
D2
D1
D0
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
Write Register for User ID Write Register for User ID
A[7:0]]~J[7:0]: UserID [10 bytes]
Remarks: A[7:0]~J[7:0] can be stored in
OTP
0
1
A7
A6
A5
A4
A3
A2
A1
A0
0
1
B7
B6
B5
B4
B3
B2
B1
B0
0
1
C7
C6
C5
C4
C3
C2
C1
C0
0
1
D7
D6
D5
D4
D3
D2
D1
D0
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
OTP program mode
OTP program mode
A[1:0] = 00: Normal Mode [POR]
A[1:0] = 11: Internal generated OTP
programming voltage
Remark: User is required to EXACTLY
follow the reference code sequences
0
1
0
0
0
0
0
0
A1
A0

<!-- Page 31 -->

SSD1680
Rev 0.14
P 31/46
Jun 2019
Solomon Systech
Command Table
R/W# D/C# Hex
D7
D6
D5
D4
D3
D2
D1
D0 Command
Description
0
0
3C
0
0
1
1
1
1
0
0
Border Waveform Control Select border waveform for VBD
A[7:0] = C0h [POR], set VBD as HIZ.
A [7:6]  :Select VBD option
A[7:6]
Select VBD as
00
GS Transition,
Defined in A[2] and
A[1:0]
01
Fix Level,
Defined in  A[5:4]
10
VCOM
11[POR]
HiZ
A [5:4] Fix Level Setting for VBD
A[5:4]
VBD level
00
VSS
01
VSH1
10
VSL
11
VSH2
A[2] GS Transition control
A[2]
GS Transition control
0
Follow LUT
(Output VCOM @ RED)
1
Follow LUT
A [1:0] GS Transition setting for VBD
A[1:0]
VBD Transition
00
LUT0
01
LUT1
10
LUT2
11
LUT3
0
1
A7
A6
A5
A4
0
A2
A1 A0
0
0
3F
0
0
1
1
1
1
1
1
End Option (EOPT)
Option for LUT end
A[7:0]= 02h [POR]
22h
Normal.
07h
Source output level keep
previous output before power off
0
1
A7
A6
A5
A4
A3
A2
A1
A0
0
0
41
0
1
0
0
0
0
0
1
Read RAM Option
Read RAM Option
A[0]= 0 [POR]
0 : Read RAM corresponding to RAM0x24
1 : Read RAM corresponding to RAM0x26
0
1
0
0
0
0
0
0
0
A0
0
0
44
0
1
0
0
0
1
0
0
Set RAM X - address
Start / End position
Specify the start/end positions of the
window address in the X direction by an
address unit  for RAM
A[5:0]: XSA[5:0], XStart, POR = 00h
B[5:0]: XEA[5:0], XEnd,  POR = 15h
0
1
0
0
A5
A4
A3
A2
A1
A0
0
1
0
0
B5
B4
B3
B2
B1
B0
0
0
45
0
1
0
0
0
1
0
1
Set Ram Y- address
Start / End position
Specify the start/end positions of the
window address in the Y direction by an
address unit for RAM
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
window addresses which is controlled by the Data Entry Setting (R11h) {AM, ID[1:0]} ; RAM Address XStart / XEnd
Position (R44h) and RAM Address Ystart /Yend Position (R45h). Otherwise undesirable image will be displayed on the
Panel.

<!-- Page 39 -->

SSD1680
Rev 0.14
P 39/46
Jun 2019
Solomon Systech
9
Operation Flow and Code Sequence
9.1 General operation flow to drive display panel
.
START
2. Set Initial Configuration
•
Define SPI interface to communicate with MCU
•
HW Reset
•
SW Reset by Command 0x12
•
Wait 10ms
1. Power On
•
Supply VCI
•
Wait 10ms
4. Load Waveform LUT
•
Sense temperature by int/ext TS by Command 0x18
•
Load waveform LUT from OTP by Command 0x22, 0x20
or by MCU
•
Wait BUSY Low
5. Write Image and Drive Display Panel
•
Write image data in RAM by Command 0x4E, 0x4F,
0x24, 0x26
•
Set softstart setting by Command 0x0C
•
Drive display panel by Command 0x22, 0x20
•
Wait BUSY Low
END
6. Power Off
•
Deep sleep by Command 0x10
•
Power OFF
3. Send Initialization Code
•
Set gate driver output by Command 0x01
•
Set display RAM size by Command 0x11, 0x44, 0x45
•
Set panel border by Command 0x3C
Figure 9-1: Operation flow to drive display panel

<!-- Page 40 -->

SSD1680
Rev 0.14
P 40/46
Jun 2019
Solomon Systech
10 Absolute Maximum Rating
Table 10-1 : Maximum Ratings
Symbol
Parameter
Rating
Unit
VCI
Logic supply voltage
-0.5 to +6.0
V
VIN
Logic Input voltage
-0.5 to VDDIO+0.5
V
VOUT
Logic Output voltage
-0.5 to VDDIO+0.5
V
TOPR
Operation temperature range
-40 to +85
°C
TSTG
Storage temperature range
-65 to +150
°C
Maximum ratings are those values beyond which damages to the device may occur. Functional operation should be
restricted to the limits in the Electrical Characteristics tables or Pin Description section
This device contains circuitry to protect the inputs against damage due to high static voltages or electric fields;
however, it is advised that normal precautions be taken to avoid application of any voltage higher than maximum rated
voltages to this high impedance circuit. For proper operation it is recommended that VCI be constrained to the range
VSS < VCI. Reliability of operation is enhanced if unused input is connected to an appropriate logic voltage level (e.g.,
either VSS or VDDIO). Unused outputs must be left open. This device may be light sensitive. Caution should be taken to
avoid exposure of this device to any light source during normal operation. This device is not radiation protected.
11 Electrical Characteristics
The following specifications apply for:  VSS=0V, VCI=3.0V, VDD=1.8V, TOPR=25ºC.
Table 11-1: DC Characteristics
Symbol
Parameter
Applicable pin
Test Condition
Min.
Typ.
Max.
Unit
VCI
VCI operation voltage
VCI
2.2
3.0
3.7
V
VDD
VDD operation voltage
VDD
1.7
1.8
1.9
V
VCOM_DC
VCOM_DC output
voltage
VCOM
-3.0
-0.2
V
dVCOM_DC
VCOM_DC output
voltage deviation
VCOM
-200
200
mV
VCOM_AC
VCOM_AC output
voltage
VCOM
VSL +
VCOM_DC
VCOM_DC
VSH1+
VCOM_DC
V
VGATE
Gate output voltage
G0~G295
-20
+20
V
VGATE(p-p)
Gate output peak to
peak voltage
G0~G295
40
V
VSH1
Positive Source output
voltage
VSH1
+2.4
+15
+17
V
dVSH1
VSH1 output voltage
deviation
VSH1
From 2.4V to 8.8V
-100
100
mV
From 9.0V to 17V
-200
200
mV
VSH2
Positive Source output
voltage
VSH2
+2.4
+5
+17
V
dVSH2
VSH2 output voltage
deviation
VSH2
From 2.4V to 8.8V
-100
100
mV
From 9.0V to 17V
-200
200
mV
VSL
Negative Source output
voltage
VSL
-17
-15
-9
V
dVSL
VSL output voltage
deviation
VSL
-200
200
mV
VIH
High level input voltage
SDA, SCL, CS#,
D/C#, RES#, BS1,
M/S#, CL
0.8VDDIO
V
VIL
Low level input voltage
0.2VDDIO
V
VOH
High level output voltage SDA, BUSY, CL
IOH = -100uA
0.9VDDIO
V
VOL
Low level output voltage
IOL = 100uA
0.1VDDIO
V
VPP
OTP Program voltage
VPP
7.25
7.5
7.75
V

<!-- Page 41 -->

SSD1680
Rev 0.14
P 41/46
Jun 2019
Solomon Systech
Symbol
Parameter
Applicable pin
Test Condition
Min.
Typ.
Max.
Unit
Islp_VCI
Sleep mode current
VCI
- DC/DC off
- No clock
- No output load
- MCU interface
access
- RAM data access
20
35
uA
Idslp_VCI1
Current of deep sleep
mode 1
VCI
- DC/DC off
- No clock
- No output load
- No MCU interface
access
- Retain RAM data
but cannot access
the RAM
1
3
uA
Idslp_VCI2
Current of deep sleep
mode 2
VCI
- DC/DC off
- No clock
- No output load
- No MCU interface
access
- Cannot retain RAM
data
0.7
3
uA
Iopr_VCI
Operating Mode current
VCI
VCI=3.0V
Enable Clock and
Analog by Master
Activation Command
VGH=20V
VGL=-VGH
VSH1=15V
VSH2=5V
VSL=-15V
VCOM = -2V
No waveform
transitions.
No loading.
No RAM read/write
No OTP read /write
1000
uA
VGH
Operating Mode
Output Voltage
VGH
19.5
20
20.5
V
VSH1
VSH1
14.8
15
15.2
V
VSH2
VSH2
4.9
5
5.1
V
VSL
VSL
-15.2
-15
-14.8
V
VCOM
VCOM
-2.2
-2
-1.8
V
Table 11-2: Regulators Characteristics
Symbol
Parameter
Test Condition
Applicable pin
Min.
Typ.
Max.
Unit
IVSH
VSH1 current
VSH1 = +15V
VSH1
800
uA
IVSH1
VSH2 current
VSH2 = +5V
VSH2
800
uA
IVSL
VSL current
VSL = -15V
VSL
800
uA
IVCOM
VCOM current
VCOM = -2V
VCOM
100
uA

<!-- Page 42 -->

SSD1680
Rev 0.14
P 42/46
Jun 2019
Solomon Systech
12 AC Characteristics
12.1 Serial Peripheral Interface
The following specifications apply for: VDDIO - VSS = 2.2V to 3.7V, TOPR = 25°C, CL=20pF
Table 12-1 : Serial Peripheral Interface Timing Characteristics
Write mode
Symbol
Parameter
Min
Typ
Max
Unit
fSCL
SCL frequency (Write Mode)
20
MHz
tCSSU
Time CS# has to be low before the first rising edge of SCLK
60
ns
tCSHLD
Time CS# has to remain low after the last falling edge of SCLK
65
ns
tCSHIGH
Time CS# has to remain high between two transfers
100
ns
tSCLHIGH
Part of the clock period where SCL has to remain high
25
ns
tSCLLOW
Part of the clock period where SCL has to remain low
25
ns
tSISU
Time SI (SDA Write Mode) has to be stable before the next rising edge of SCL
10
ns
tSIHLD
Time SI (SDA Write Mode) has to remain stable after the rising edge of SCL
40
ns
Read mode
Symbol Parameter
Min
Typ
Max
Unit
fSCL
SCL frequency (Read Mode)
2.5
MHz
tCSSU
Time CS# has to be low before the first rising edge of SCLK
100
ns
tCSHLD
Time CS# has to remain low after the last falling edge of SCLK
50
ns
tCSHIGH
Time CS# has to remain high between two transfers
250
ns
tSCLHIGH Part of the clock period where SCL has to remain high
180
ns
tSCLLOW
Part of the clock period where SCL has to remain low
180
ns
tSOSU
Time SO(SDA Read Mode) will be stable before the next rising edge of SCL
50
ns
tSOHLD
Time SO (SDA Read Mode) will remain stable after the falling edge of SCL
0
ns
Note: All timings are based on 20% to 80% of VDDIO-VSS
Figure 12-1: SPI timing diagram

<!-- Page 43 -->

SSD1680
Rev 0.14
P 43/46
Jun 2019
Solomon Systech
13 Application Circuit
Figure 13-1: Schematic of SSD1680 application circuit
Table 13-1: Component list for SSD1680 application circuit
Part Name
Value
Requirements/Reference Part
C0-C1
1uF
X5R/X7R; Voltage Rating : 6V or 25V
C2-C7
1uF
0402/0603/0805; X5R/X7R; Voltage Rating : 25V
C8
0.47uF, 1uF
0603/0805; X7R; Voltage Rating : 25V
Note: Effective capacitance > 0.25uF @ 18V DC bias
R1
2.2 ohm
0402, 0603, 0805; 1% variation, ≥ 0.05W
D1-D3
Diode
MBR0530
1) Reverse DC voltage ≥ 30V
2) Io ≥ 500mA
3) Forward voltage ≤  430mV
Q1
NMOS
Si1304BDL/NX3008NBK
1)
Drain-Source breakdown voltage ≥ 30V
2)
Vgs(th) = 0.9V (Typ), 1.3V (Max)
3)
Rds on ≤ 2.1Ω @ Vgs = 2.5V
L1
47uH
CDRH2D18 / LDNP-470NC
Io= 500mA (Max)
U1
0.5mm ZIF socket
24pins, 0.5mm pitch
Remarks:
1)
The recommended component value and reference part in Table 13-1 is subject to change depending on panel
loading.
2)
Customer is required to review if the selected component value and part is suitable for their application.

<!-- Page 44 -->

SSD1680
Rev 0.14
P 44/46
Jun 2019
Solomon Systech
14 Package Information
14.1 Die Tray Dimensions for SSD1680Z
Figure 14-1 : SSD1680Z die tray information (unit: mm)

<!-- Page 45 -->

SSD1680
Rev 0.14
P 45/46
Jun 2019
Solomon Systech
14.2 Die Tray Dimensions for SSD1680Z8
Figure 14-2 : SSD1680Z8 die tray information (unit: mm)

<!-- Page 46 -->

SSD1680
Rev 0.14
P 46/46
Jun 2019
Solomon Systech
Solomon Systech reserves the right to make changes without notice to any products herein. Solomon Systech makes no warranty, representation
or guarantee regarding the suitability of its products for any particular purpose, nor does Solomon Systech assume any liability arising out of the
application or use of any product or circuit, and specifically disclaims any, and all, liability, including without limitation consequential or incidental
damages. “Typical” parameters can and do vary in different applications. All operating parameters, including “Typical” must be validated for each
customer application by the customer’s technical experts. Solomon Systech does not convey any license under its patent rights nor the rights of
others. Solomon Systech products are not designed, intended, or authorized for use as components in systems intended for surgical implant into
the body, or other applications intended to support or sustain life, or for any other application in which the failure of the Solomon Systech product
could create a situation where personal injury or death may occur. Should Buyer purchase or use Solomon Systech products for any such unintended
or unauthorized application, Buyer shall indemnify and hold Solomon Systech and its offices, employees, subsidiaries, affiliates, and distributors
harmless against all claims, costs, damages, and expenses, and reasonable attorney fees arising out of, directly or indirectly, any claim of personal
injury or death associated with such unintended or unauthorized use, even if such claim alleges that Solomon Systech was negligent regarding the
design or manufacture of the part.
The product(s) listed in this datasheet comply with Directive 2011/65/EU of the European Parliament and of the council of 8 June 2011 on the
restriction of the use of certain hazardous substances in electrical and electronic equipment and People’s Republic of China Electronic Industry
Standard GB/T 26572-2011 “Requirements for concentration limits for certain hazardous substances in electronic information products (电子电器产
品中限用物質的限用要求)”. Hazardous Substances test report is available upon request.
http://www.solomon-systech.com

---

# 4. GDEM0266T71WT Datasheet

> **Source file:** `GDEM0266T71WT.pdf`  
> Good Display — GDEM0266T71WT 2.66" e-paper display module (OCR-extracted)

<!-- Page 1 -->

2.66 inch
E-paper Display
GDEM0266T71WT 
 
Dalian Good Display Co., Ltd.
GOODISPLAY

<!-- Page 2 -->

GooDisplay GDEM0266T71WT

Product Specifications

BR BH

| Sunny c
Temperature ™ a
i wy

RB

ie il
Al alll

Customer Standard
Description 2.66” E-PAPER DISPLAY
Model Name GDEMO266T71WT
Date 2025/04/01
Revision 1.0
Design Engineering
Approval Check Design

ep ey Lay | ee

Zhongnan Building, No.18, Zhonghua West ST,Ganjingzi DST,Dalian, CHINA
Tel: +86-411-84619565
Email: info@good-display.com

Website: www.good-display.com

www.good-display.com 2/34 2.66 inch series

<!-- Page 3 -->

CONTENTS
7.
8.
9.
1.
Over View......................................................................................................................................
2.
Features ...........................................................................................................................................
3.
Mechanical Specification................................................................................................................
4.
Mechanical Drawing of EPD Module.............................................................................................
5.
Input/output Pin Assignment...........................................................................................................
6.
Electrical Characteristics.................................................................................................................
5
6
7
8
9
 
Command Table...............................................................................................................................
Block Diagram.................................................................................................................................
Typical Application Circuit with SPI Interface...............................................................................
6.1 Absolute Maximum Rating.......................................................................................................
6.2 Panel DC Characteristics...........................................................................................................
6.3 MCU Interface...........................................................................................................................
6.3.1 MCU Interface Selection........................................................................................................
6.3.2 MCU Serial Interface(4-wire SPI) .........................................................................................
6.3.3 MCU Serial Interface(3-wire SPI) ......................................................................................... 
6.3.4 Interface Timing.....................................................................................................................
10.
Typical Operating Sequence............................................................................................................
GDEM0266T71WT
www.good-display.com
3/34
2.66 inch series
9
5
14
16
24
25
26
12
11
11
11
10
GOODISPLAY

<!-- Page 4 -->

11.
Reliability Test................................................................................................................................
12.
Inspection Condition.......................................................................................................................
13.
Handling, Safety, and Environment Requirements.........................................................................
14.
Packaging........................................................................................................................................
28 
29 
33 
34 
GDEM0266T71WT
www.good-display.com
4/34
2.66 inch series
GOODISPLAY

<!-- Page 5 -->

GooDisplay GDEM0266T71WT

1. Over View

GDEM0266T71WT is an Active Matrix Electrophoretic Display (AM EPD), with interface and a
reference system design. The display is capable to display images at 1-bit white and black full display
capabilities. The 2.66 inch active area contains 152x296 pixels. The module is a TFT-array driving
electrophoresis display, with integrated circuits including gate driver, source driver, MCU interfece,
timing controller, oscillator, DC-DC, SRAM, LUT, VCOM. Module can be used in portable electronic
devices, such as Electronic Shelf Label (ESL) System.

2. Features

@ 152x296 pixels display

High contrast High reflectance

@ Ultra wide viewing angle Ultra low power consumption

Pure reflective mode

@Bi-stable display

@ Commercial temperature range

@ Landscape portrait modes

@ Hard-coat antiglare display surface

Ultra Low current deep sleep mode

On chip display RAM

@ Waveform can stored in On-chip OTP or written by MCU

Serial peripheral interface available

On-chip oscillator

On-chip booster and regulator control for generating VCOM, Gate and Source driving
voltage

2. "
1 C signal master interface to read external temperature sensor
Built-in temperature sensor

www.good-display.com 5/34 2.66 inch series

<!-- Page 6 -->

GooDisplay GDEM0266T71WT

3.Mechanical and Optical Specification

Parameter Specifications Unit Remark
Screen Size 2.66 Inch
Display Resolution 152(H)x296(V) Pixel DPI:125
Active Area 30.704*60.088 mm
Pixel Pitch 0.202 0.203 mm
Pixel Configuration Rectangle
Outline Dimension 36.30(H)*71.82 (V) x1.0(D) mm
Weight 4.740.5 g
Symbol | Parameter Conditions Min Typ. Max Units Notes
Black State L* value : 19 22 3-1
Black Ghosting AL : 1 : 3-1
ws White State L* value 66 67 = 3-1
White Ghosting AL - I - 3-1
R White Reflectivity White 30 34 - % 3-1
CR Contrast Ratio Indoor 15:1 20:1 - 3-1
3-2

GN 2Grey Level - - - -
A Temp:23 + 3°C
Life Humidity:55 + 10%RH

Syears 3-3

Notes: 3-1. Luminance meter: Eye-One Pro Spectrophotometer.
3-2. CR=Surface Reflectance with all white pixel/Surface Reflectance with all black pixels.
3-3. When the product is stored. The display screen should be kept white and face up.

www.good-display.com 6/34 2.66 inch series

<!-- Page 7 -->

GooDisplay GDEM0266T71WT

4.Mechanical Drawing of EPD Module

NOTE
1 DISPLAY NODULE 2. 66” ARRAY FOR EPD
, Sei 6807 EPD A 25.04.01
2 DRIVER IC:SSD168028 ANGLES:5"
3 RESOLUTION: 296gateX152source X=204mm
4 PIXEL SIZE: 0. 202mmX 0.203. mm Xx==0.20mm | GDEMO266T7INT mm 1/1

XXxX==0.20mm

www.good-display.com 7/34 2.66 inch series

<!-- Page 8 -->

GooDisplay GDEM0266T71WT

5. Input/output Pin Assignment

No. Name Vo Description Remark
1 NC Do not connect with other NC pins Keep Open
2 GDR O_ | N-Channel MOSFET Gate Drive Control
3 RESE I Current Sense Input for the Control Loop
4 NC NC | Do not connect with other NC pins Keep Open
5 VSH2 C_ | Positive Source driving voltage 2
6 TSCL O_ | I2C Interface to digital temperature sensor Clock pin Note 5-6
7 TSDA I/O | 12C Interface to digital temperature sensor Data pin Note 5-6
8 BSI I | Bus Interface selection pin Note 5-5
9 BUSY O | Busy state output pin Note 5-4
10 RES# I Reset signal input. Active Low. Note 5-3
ll D/C# I | Data /Command control pin Note 5-2
12 CS# I Chip select input pin Note 5-1
13 SCL I Serial Clock pin (SPI)

14 SDA VO _ | Serial Data pin (SPI)

Power Supply for interface logic pins It should be

Is VDDIO p connected with VCI

16 VCI P_ | Power Supply for the chip

17 VSS P| Ground
Core logic power pin VDD can be regulated internally

18 VDD C_ | from VCI. A capacitor should be connected between
VDD and VSS

19 VPP P |FOR TEST Keep Open

20 VSH1 C_ | Positive Source driving voltage

4 VGH Cc Power Supply pin for Positive Gate driving voltage and
VSH1

22 VSL C_ | Negative Source driving voltage

23 VGL c Power Supply pin for Negative Gate driving voltage

VCOM and VSL
24 VCOM C_ | VCOM driving voltage

www.good-display.com 8/34 2.66 inch series

<!-- Page 9 -->

GooDisplay GDEM0266T71WT

I= Input Pin, O =Output Pin, I/O = Bi-directional Pin (Input/output), P = Power Pin, C = Capacitor Pin

Note 5-1: This pin (CS#) is the chip select input connecting to the MCU. The chip is enabled for MCU
communication only when CS# is pulled LOW.

Note 5-2: This pin is (D/C#) Data/Command control pin connecting to the MCU in 4-wire SPI mode. When
the pin is pulled HIGH, the data at SDA will be interpreted as data. When the pin is pulled LOW,
the data at SDA will be interpreted as command.

Note 5-3: This pin (RES#) is reset signal input. The Reset is active low.

Note 5-4: This pin is Busy state output pin. When Busy is High, the operation of chip should not be
interrupted, command should not be sent. The chip would put Busy pin High when -Outputting
display waveform -Communicating with digital temperature sensor

Note 5-5: Bus interface selection pin.

BS1 State MCU Interface
L 4-lines serial peripheral interface(SPI) - 8 bits SPI
H 3- lines serial peripheral interface(SPI) - 9 bits SPI

6. Electrical Characteristics

6.1 Absolute Maximum Rating

Parameter Symbol Rating Unit
Logic supply voltage VCI -0.5 to +6.0 Vv
Logic Input voltage VIN -0.5 to VCI +0.5 Vv
Logic Output voltage VOUT -0.5 to VCI +0.5 Vv
Operating Temp range TOPR -25to +10 °C.
Operating Temp range max TOPRm -25 to +30 °C.
Storage Temp range TSTG -25 to+70 °C.
Optimal Storage Temp TSTGo 2343 °C.

Optimal Storage Humidity HSTGo 55410 %RH

Note:1. Maximum ratings are those values beyond which damages to the device may occur. Functional
operation should be restricted to the limits in the Panel DC Characteristics tables.

2. Due to the particle characteristics of FPL, we only guarantee that the bar code can be read from
10-30°C. The recommended operating temperature should be kept above -25-10°C.

www.good-display.com 9/34 2.66 inch series

<!-- Page 10 -->

GooDisplay GDEM0266T71WT

6.2 Panel DC Characteristics
The following specifications apply for: VSS=0V, VCI=3.0V, TOPR = -15°C.

Parameter Symbol Condition opptcable Min. | Typ. | Max. | Unit
Single ground Vss - - 0 - Vv
Logic supply voltage Vel - VCI 2.2 3.0 3.7 Vv
Core logic voltage Vpp VDD 1.7 1.8 19 Vv
High level input voltage Vin - - 0.8 Ver - - Vv
Low level input voltage Vit - - - - 0.2 Ver Vv
High level output voltage Vou IOH = -100uA. - 0.9 Ver - - Vv
Low level output voltage VoL IOL = 100uA : : : 0.1 Ver Vv
Typical power Pryp Vai =3.0V - - 13.5 - mW
Deep sleep mode Pstpy Vai =3.0V - - 0.003 - mW
Typical operating current | lopr_VCI Vai =3.0V - - 45 : mA
Image update time : -15°C : : 30 : sec
Typical peak current Iopr_VCI 2.2~3.1V 40 60 mA

DC/DC off
Sleep mode current Islp_Ver No clock : b 20 uA
No input load
Ram data retain
DC/DC off
Deep sleep mode current | Idslp_Vcr No cloclg - - 1 5 uA

No input load
Ram data not retain
Notes: 1. The typical power is measured with following transition from horizontal 2 scale pattern to vertical

a

2. The deep sleep power is the consumed power when the panel controller is in deep sleep mode.

2 scale pattern.

3. The listed electrical characteristics are only guaranteed under the controller & waveform provided
by DKE.
4. Electrical measurement: Tektronix oscilloscope - MDO3024,

Tektronix current probe - TCP0030A.

www.good-display.com 10/34 2.66 inch series

<!-- Page 11 -->

GooDisplay GDEM0266T71WT

6.3 MCU Interface
6.3.1 MCU Interface Selection
The pin assignment at different interface mode is summarized in Table 6-3-1. Different MCU
mode can be set by hardware selection on BS1 pins. The display panel only supports 4-wire SPI or

3-wire SPI interface mode.

Pin Name Data/Command Interface Control Signal

Bus interface SDA SCL CS# D/C# RES#
BSI=L_ 4-wire SPI SDA SCL CS# D/C# RES#
BSI=H_ 3-wire SPI SDA SCL CS# L RES#

6.3.2 MCU Serial Interface (4-wire SPI)
The serial interface consists of serial clock SCL, serial data SDA, D/C#, CS#. This interface

supports Write mode and Read mode.

Function CS# D/C# SCL
Write command L L t
Write data L H t

Note: { stands for rising edge of signal

In the write mode SDA is shifted into an 8-bit shift register on every rising edge of SCL in the
order of D7, D6, ... DO. The level of D/C# should be kept over the whole byte . The data byte in the
shift register is written to the Graphic Display Data RAM /Data Byte register or command Byte
register according to D/C# pin.

| [
oo
= TU

& PRA@@EE@@00O0

Parameter

Figure 6-1: Write procedure in 4-wire SPI mode

www.good-display.com 11/34 2.66 inch series

<!-- Page 12 -->

GooDisplay GDEM0266T71WT

In the Read mode:
1. After driving CS# to low, MCU need to define the register to be read.
2. SDA is shifted into an 8-bit shift register on every rising edge of SCL in the order of D7,
D6, ... DO with D/C# keep low.
3. After SCL change to low for the last bit of register, D/C# need to drive to high.
4. SDA is shifted out an 8-bit data on every falling edge of SCL in the order of D7, D6, ... DO.
5. Depending on register type, more than 1 byte can be read out. After all byte are read, CS#

need to drive to high to stop the read operation.

2 r

‘ W
Register Parameter

SDA
onions |X KEK ™ KE AE A)

SDA
ecg i}

Figure 6-2: Read procedure in 4-wire SPI mode

6.3.3 MCU Serial Interface (3-wire SPI)

The 3-wire serial interface consists of serial clock SCL, serial data SDA and CS#. This
interface also supports Write mode and Read mode.

The operation is similar to 4-wire serial interface while D/C# pin is not used. There are
altogether 9-bits will be shifted into the shift register on every ninth clock in sequence: D/C# bit, D7
to DO bit. The D/C# bit (first bit of the sequential data) will determine the following data byte in
the shift register is written to the Display Data RAM (D/C# bit = 1) or the command register (D/C#
bit = 0).

Function CS# D/C# SCL
Write command L Tie t
Write data L Tie t

Note: { stands for rising edge of signal

www.good-display.com 12/34 2.66 inch series

<!-- Page 13 -->

GooDisplay GDEM0266T71WT

am | [

SCL
SDA
(Write 0 } D7} D6 } DS } D4} D3} D2} D1} DOX 1 } D7
Mode)
Register Parameter
Figure 6-3: Write procedure in 3-wire SPI mode
In the Read mode:

1. After driving CS# to low, MCU need to define the register to be read.

2. D/C=0 is shifted thru SDA with one rising edge of SCL

3. SDA is shifted into an 8-bit shift register on every rising edge of SCL in the order of D7,
D6, ... DO.

4. D/C=1 is shifted thru SDA with one rising edge of SCL

5. SDA is shifted out an 8-bit data on every falling edge of SCL in the order of D7, D6, ... DO.

6. Depending on register type, more than | byte can be read out. After all byte are read, CS#

need to drive to high to stop the read operation.

c# | if

& pDOooOooooo ey

‘
SDA i \
Read - D7
Mode) i ;
i i

Figure 6-4: Read procedure in 3-wire SPI mode

www.good-display.com 13/34 2.66 inch series

<!-- Page 14 -->

GooDisplay GDEM0266T71WT

6.3.4 Interface Timing
The following specifications apply for: VSS=0V, VCI=3.0V, Torr =-15°C.

Changed Diagram

Serial Interface Timing Characteristics

(VCI - VSS = 2.2V to 3.7V, TOPR = -15°C, CL=20pF)

Write mode

Symbol |Parameter (Min |Typ. |Max |Unit
fSCL SCL frequency (Write Mode) 20 | MHz
tCSSU Time CS# has to be low before the first rising edge of SCLK 60 ns
'tCSHLD —_|Time CS# has to remain low after the last falling edge of SCLK 65 ns
tCSHIGH |Time CS# has to remain high between two transfers 100 ns
itSCLHIGH |Part of the clock period where SCL has to remain high 25 ns
tSCLLOW |Part of the clock period where SCL has to remain low 25 ns
iSISU sre SI (SDA Write Mode) has to be stable before the next rising edge o 10 ns
tSIHLD sare SI (SDA Write Mode) has to remain stable after the rising edge o 40 ns

www.good-display.com 14/34 2.66 inch series

<!-- Page 15 -->

GooDisplay GDEM0266T71WT

Read mode

‘Symbol |Parameter (Min |Typ. |Max |Unit
fSCL ISCL frequency (Read Mode) 2.5 | MHz
tCSSU Time CS# has to be low before the first rising edge of SCLK 100 ns
tCSHLD — |Time CS# has to remain low after the last falling edge of SCLK 50 ns
tCSHIGH |Time CS# has to remain high between two transfers 250 ns
poLiiG Part of the clock period where SCL has to remain high 180 ns
tSCLLOW JPart of the clock period where SCL has to remain low 180 ns
tSOSU Time SO(SDA Read Mode) will be stable before the next rising edge of SCL 50 ns
tSOHLD |Time SO (SDA Read Mode) will remain stable after the falling edge of SCL 0 ns

www.good-display.com 15/34 2.66 inch series

<!-- Page 16 -->

GooDisplay GDEM0266T71WT

7.Command Table

R/W#|D/c#| Hex| D7 | D6 | D5 | D4 | D3 | 2 | D1 | Do cemman Description

0 0 |01;0{|0]0)04} 01} 0} 0 | 1 |Driver  |Gate setting

o|1 A7| A6| A5|A4| A3 | A2| Al | Ao [Output Set A[8:0]-0127h

0 1 ololololololo las control Set B[8:0]=00h

o|1 o{|o[0]0 | 0 |B2/B1/ Bo

0 0 {03} 0}]0}]0)0]0]0) 1 | 1 \Gate SetGate Driving voltage

ololo Driving |A[4:0]=17h[POR],VGH at 20V[POR]

ol 4 A4|A3|A2|A1| Ao [voltage |VGH setting from 10V to 20V
control

0 0 }04}0;0/0;)0;0)/ 1 0 | 0 |Source  |Set Source Driving voltage

old ‘A7/A6|A5/A4/A3|A2/ Al | Ao [Priving |A[7:0}= 41h[POR],VSHI at 15V
voltage :0]=A Ch[POR],VSH2 at 5.4V

oj B7 | B6 | BS | B4 | B3 | B2 | BI | BO | ontrol = 32h[POR], VSL at -15V

of c7| ce} cs | c4]}c3 | c2| c1 | co

Initial —_|Program Initial Code Setting

Code ‘The command required CLKEN=1.
0 0 |08]0}0}]0}0)] 1] 0 | 0 | 0 {Setting [Refer to Register 0x22 for detail.

OTP BUSY pad will output high during

Program joperation

0 0 |09;}/0;/0;,0/0} 140) 0] 1 |Write Write Register for Initial Code Setting

of 1 A7| A6| A5| A4] A3 | A2| AT | Ao [Register |Selection
for Initial |A[7:0] ~ D[7:0]: Reserved

9 1 B7 | B6 | BS | B4 | B3 | B2 | BI | BO Code Details refer to Application Notes of Initial
of 1 7] co | cs | C4] C3 [C2] C1 | CO|setting [Code Setting
0 1 D7 | D6 | DS | D4| D3 | D2 | DI | DO
Read Read Register for Initial Code Setting
OA Register
0 0 0} 0} 0 {0 1) 0} 1 | O |for Initial
Code
Setting
0 0 |10]0}0};,0{1/)]0{ 04 0 | 0 |Deep Deep Sleep mode Control:
0 1 o/o}o}o}]o}0)]0] Ao Sleep A[1:0]: Description

mode 00 ~Normal Mode [POR]
01 Enter Deep Sleep Mode 1
11 Enter Deep Sleep Mode 2
After this command initiated, the chip will
enter Deep Sleep Mode, BUSY pad will
keep output high.
Remark:
To Exit Deep Sleep mode, User required
to send HWRESET to the driver

www.good-display.com 16/34 2.66 inch series

<!-- Page 17 -->

GooDisplay GDEM0266T71WT

0 oO /1l1)0}/0)]0)]14]0/)] 0) 0) 1 JData Define data entry sequence
Entry — |A[2:0] = 011 [POR]
mode A [1:0] = ID[1:0]
setting  |Address automatic increment / decrement
setting
The setting of incrementing or
decrementing of the address counter can
be made independently in each upper and
0 1 0} 0] 0} 0] 0 | A>} Ai} Ao lower bit of the address.
00 - Y decrement, X decrement,
01 - Y decrement, X increment,
10 - Y increment, X decrement,
11 - Y increment, X increment [POR]
A[2]=AM
Set the direction in which the address
counter is updated automatically after data
are written to the RAM.
AM= 0, the address counter is updated in
the X direction. [POR]
AM = 1, the address counter is updated in
the Y direction

www.good-display.com 17/34 2.66 inch series

<!-- Page 18 -->

GooDisplay GDEM0266T71WT

0 0 }0oc;}0;0}0);0)} 1 1 | 0 | 0 |Booster |Booster Enable with Phase 1, Phase 2 and Phase 3
Soft start |for soft start current and duration setting.
‘Control |A[7:0] -> Soft start setting for Phasel

= 8Bh [POR]

B[7:0] -> Soft start setting for Phase2
= 9Ch [POR]

|C[7:0] -> Soft start setting for Phase3
= 96h [POR]

D[7:0] -> Duration setting

= OFh [POR]

Bit Description of each byte:
A[6:0] / B[6:0] / C[6:0]:
Bit[6:4]

Driving Strength

Selection

000 1(Weakest)

001 2

010 3

Oll 4

100 5

101 6

110 7

111 8(Strongest)

Bit[3:0]

‘Min Off Time Setting of GDR
[ Time unit ]

0000

(0011

NA

0100 2.6

0101 = 3.2

0110 3.9
0 1 1 | A6| A5 | A4| A3 | A2} Al | AO oll 46

0 1 1 | B6| BS | B4| B3 | B2| BI | BO 1000 5.4

7 ; 1001 6.3

0 1 1 | C6} C5 | C4) C3 | C2} C1 | CO 1010 73

0 1 0 | 0 | DS) D4} D3) D2) D1 | DO 1011 8.4

1100 9.8

1101 11.5

1110 13.8

1111 16.5

'D[5:0]: duration setting of phase
'D[5:4]: duration setting of phase 3
D[3:2]: duration setting of phase 2
D[1:0]: duration setting of phase 1
Bit[ 1:0]

Duration of Phase
[Approximation]

00 10ms

01 20ms

10 30ms

11 40ms

www.good-display.com 18/34 2.66 inch series

<!-- Page 19 -->

GooDisplay GDEM0266T71WT

0 0 |12/ 0/0] 0); 140] 0] 1 | 0 |SWRES It resets the commands and parameters to
ET their S/W Reset default values except
R10h-Deep Sleep Mode
During operation, BUSY pad will output

high.
Note: RAM are unaffected by this
command.
0 0 |18]| 0] 0} 0] 1 4} 1 | 0 | 0 | O |Temperat|/Temperature Sensor Selection
ure A[7:0] = 48h [POR], external temperature sensor
9 ! AT] A6) AS | A4) A3] A2) Al | AO Sensor |A[7:0] = 80h Internal temperature sensor
Control

0 0 {1A} 0/0 {0} 1} 1] 0} 1 | O |Temperat|Write to temperature register.

oo}. A7|A6| AS] A4] A3 | A2| Al | AO Jere A[11:0] = 7FFh [POR]
Sensor
0} 1 B7| Bo | B5|B4] 0 | 0 | 0 | O [Control
(Write to
temperat
ure
register)|

0 0 |20/ 0/0] 1 {040} 0] 0 | 0 |Master |Activate Display Update Sequence
Activatio |The Display Update Sequence Option is located at
in R22h
User should not interrupt this operation to avoid
corruption of panel images.

0 0 |21/ 0/0] 1{) 040] 0 | 0] 1 {Display |RAM content option for Display Update
o [1 A7/A6| A5| A4] a3] a2] Al] AO date 1 AT: =o IpoR

ontro!
0 1 B7}0}0/0/0/0/0)]0 Red RAM option
Normal
Bypass RAM content as 0
Inverse RAM content
A[3:0] BW RAM option
0000 Normal
0100 Bypass RAM content as 0
1000 Inverse RAM content
B[7] Source Output Mode
0 Available Source from SO to S175
1 Available Source from S8 to S167

www.good-display.com 19/34 2.66 inch series

<!-- Page 20 -->

GooDisplay GDEM0266T71WT

0 0 |22) 0] 0) 1 | 0] 0 | 0] 1 | O Display [Display Update Sequence Option:
Update [Enable the stage for Master Activation
Control 2|A[7:0]= FFh (POR)
Operating sequence
Parameter
(in Hex)
Enable clock signal 80
Disable clock signal 01
Enable clock signal
Enable Analog
co.
Disable Analog
Disable clock signal
03
Enable clock signal
Load LUT with DISPLAY Mode |
Disable clock signal

0 fl AT |A6 JAS |A4 |A3 |A2 |Al |AO

91
Enable clock signal
Load LUT with DISPLAY Mode 2
Disable clock signal
99
Enable clock signal
Load temperature value
Load LUT with DISPLAY Mode |
Disable clock signal
BL
Enable clock signal
Load temperature value
Load LUT with DISPLAY Mode 2
Disable clock signal
BS
Enable clock signal
Enable Analog
Display with DISPLAY Mode 1
Disable Analog
Disable OSC
C7
Enable clock signal
Enable Analog
Display with DISPLAY Mode 2
Disable Analog
Disable OSC
CF
Enable clock signal
Enable Analog
Load temperature value
DISPLAY with DISPLAY Mode 1
Disable Analog
Disable OSC
FT
Enable clock signal
Enable Analog
Load temperature value
DISPLAY with DISPLAY Mode 2

www.good-display.com 20/34 2.66 inch series

<!-- Page 21 -->

GooDisplay GDEM0266T71WT

0 0 |24}0]0 1)/0]0)]1) 04] 0 {Write After this command, data entries will be

RAM written into the BW RAM until another
(Black —|command is written. Address pointers will
White) jadvance accordingly
/ RAM _ |For Write pixel:
0x24 ‘Content of Write RAM(BW) = 1

For Black pixel:

‘Content of Write RAM(BW) = 0

0 0 |26)0)0}1)0]0)] 1) 1 | 0 Write After this command, data entries will be
RAM written into the RED RAM until another
(RED) —|command is written. Address pointers will
/ RAM _ jadvance accordingly.
0x26) For Red pixel:
Content of Write RAM(YELLOW) = |
For non-Red pixel [Black or White]:
Content of Write RAM(YELLOW) = 0

0 0 }2cC;0;/0};, 1/04 1 1 | 0 | 0 |Write Write VCOM register from MCU interface
0 1 'VCOM__|A[7:0] = 00h [POR]
AT|A6| AS | A4| A3 | A2| Al | AO register
0 0 |2D;0}0]1)04} 1) 1) 04 1 JOTP Read Register for Display Option:
1|a ATIA6|AS|A4|A3|A2/ Al | Ao [Register |A[7:0]: VCOM OTP Selection

Read for |(Command 0x37, Byte A)

! ! B7 | B6 | BS | B4 | B3 | B2 | BI | BO Display |B[7:0]: VCOM Register

1 1 C7 | C6 | CS | C4} C3 | C2 | Cl | CO |Option —|(Command 0x2C)

tid D7| D6 | Ds | D4] D3 | D2 | D1 | DO C[7:0]~G[7:0]: Display Mode

ifa £7 | £6 | £5 | £4 | £3 | £2 | £1 | EO Ca? Bate B to Byte F)
tes.

tj F7 | F6 | FS | Fa | F3 | F2 | FI | FO H[7:0]~K[7:0}: Waveform Version

1 fd G7 | G6 | G5 | G4| G3 | G2| G1 | Go (Command 0x37, Byte G to Byte J)

1 1 H7 | H6 | H5 | H4| H3 | H2 | H1 | HO [4 bytes]

1] 17] 16 | 15 | 14] 13 | 12 | 11 | 10

1 1 J7 | J6 | JS | J4 | J3-| J2 | Jl | JO
1 1 K7| K6| K5 | K4| K3 | K2| K1 | KO

0 0 |2F/0;}0}1/0;/1)1)1 1 {Status Read IC status Bit [POR 0x01]
Bit Read |A[5]: HV Ready Detection flag [POR=0]
0: Ready
1: Not Ready
A[4]: VCI Detection flag [POR=0]
0: Normal
1: VCI lower than the Detect level
A[3]: [POR=0]
A[2]: Busy flag [POR=0]
0: Normal
1: BUSY
A[1:0]: Chip ID [POR=01]
Remark:
A[5] and A[4] status are not valid after
RESET, they need to be initiated by
command 0x14 and command 0x15
respectively

www.good-display.com 21/34 2.66 inch series

<!-- Page 22 -->

GooDisplay GDEM0266T71WT

0 0 |30/ 0} 0} 141) 0] 0] 0 | O |Program |Program OTP of Waveform Setting
WS OTP |The contents should be written into RAM
before sending this command.
The command required CLKEN=1.
Refer to Register 0x22 for detail.
BUSY pad will output high during

operation
0 0 |32}/0}0}f1414)0/)] 07) 1 | O {Write Write LUT register from MCU interface
0 1 A7| A6| A5| A4| A3| A2!] Al | AO [LUT [153 bytes], which contains the content of
register |VS[nX-LUTm], TP[nX], RP[n], SR[nXY],
0 1 B7 | B6 | BS | B4 | B3 | B2 | B1 | BO FR{[n] and XON[nXY]
0 1 Peedi fete feted: Refer to Session 6.7 WAVEFORM
0 1 pfa fafa fs fs fry: SETTING
0 1
0 1

0 0 |}39/0/}0}]1)]1)1/)]0/)/ 04 1 jOTP OTP program mode
program |A[1:0] = 00: Normal Mode [POR]
mode A[1:0] = 11: Internal generated OTP
programming voltage
Remark: User is required to EXACTLY
follow the reference code sequences

0 0 }3C/0;}0)1)]1t}]1})1)0)0 Select border waveform for VBD
A[7:0] = COh [POR], set VBD as HIZ.

www.good-display.com 22/34 2.66 inch series

<!-- Page 23 -->

GooDisplay GDEM0266T71WT

0 1 Az| Ao | As | As} 0 | 0 | Ai | Ao A [7:6] :Select VBD option
A[7:6] Select VBD as
00 GS Transition,
Defined in A[2] and
A[1:0]
Ol Fix Level,
Defined in A[5:4]
10 VCOM
1[POR] HizZ
‘A [5:4] Fix Level Setting for VBD
A[5:4] VBD level
00 VSS
Ol VSHI
10 VSL
11 VSH2
A[2] GS Transition control
A[2] GS Transition control
0 Follow LUT
(Output VCOM @ RED)
1 Follow LUT
A [1:0] GS Transition setting for VBD
A[1:0] VBD Transition
00 ~LUTO
01 LUTI
10 LUT2
11 LUT3

0 0 |44| 0] 1/0) 0} 0] 1 | 0 | 0 |Set RAM|Specify the start/end positions of the window
0 1 0] 0] 0 | As! A3| Ao} Ar | Ao X- address in the X direction by an address unit
address |A[4:0]: XSA[4:0], X Start, POR = 01h

9)! 0 | 0 | 0 | Bs) Bs) Bo | Bi} Bo |cioty — |pl4:0}: XEA[4:0], X End, POR = 13h

End

position
0 0 |45/ 0] 1] 0 04} 0} 1 | 0 | 1 |SetRam Specify the start/end positions of the window
0 1 A7| Ao | As | Ay] As | Ao | Ai | Ao /¥> address in the Y direction by an address unit

address |A[8:0]: YSA[8:0], Y Start, POR = 0127h

oj O10} 0/0] 0] 0} 0 [Astcct/ — {Bp8:0]: YEA[8:0], Y End, POR = 0000h
0 1 Bz | Be | Bs | Ba | Bs | Bz | Bi | Bo [End
0 1 0] 0 | 0 | 0] 0 | 0 | O | Bs position
0 0 |4E;0};1]0)0] 1 1 1 | 0 |Set RAM |Make initial settings for the RAM X address in
0 1 0101] 0] As] As} Az} Ar | Ao * the address counter (AC) |
address |A[4:0]: XAD[4:0], POR is 01h
counter
0 0 |4F/ 0} 1 ]0]04 1} 1 4} 1 | 1 |SetRAM)Make initial settings for the RAM Y address in
0 1 A7| Ae] As | As| A3 | A2| Ar | Ao ya fe address counter (A) oth
0 1 olololololololas address |A[8:0]: YAD[8:0], POR is 7

counter

www.good-display.com 23/34 2.66 inch series

<!-- Page 24 -->

GooDisplay GDEM0266T71WT

8.Block Diagram
- 12C bus PREVGL
Temperature Data & control bus (SPI EPD
Senser — DC-DC
or MCU Circur aad
Circuit I2C bus me Circuit
(Optional) EPD - se
Capacitor | | Power Circuit

Circuit

www.good-display.com 24/34 2.66 inch series

<!-- Page 25 -->

GooDisplay GDEM0266T71WT

9. Typical Application Circuit with SPI Interface

Dt D2 Connectort"24 yy

oR

— , = i ul vsH2
vel hibit > VGH
xe D3
a4
GOR iB
= 3 4
Rt
Part Name Value Reference Part Requirements for spare part
C4C6 luF XS5R/X7R;Voltage Rating:6v or 25v
cl ba g C5 luF 0402/0603/0805; X5R/X7R: Voltage Rating:25v
co luF 0603/0805; X7R; Voltage Rating:25v
NOTE: Effective capacitance >0.25uF @18v DC bias
RI 2.20hm 0402/0603/0805; 1% variation, =0.05W

1)Reverse DC Voltage=30V
D1 D2 D3 Diode MBR0530 2)lo2500mA
3)Forward voltage <430mV
1)Drain-Source breakdown voltage =30v
Ql NMOS Sil304BDL/NX3008NBK | 2)Vgs(th)=0.9v(Typ), 1.3v(Max)
3)rds on<2.1 2 @ Vgs=2.5v

Ll 47UH CDRH2D18/LDNP-470NC | 1) lo=500mA(max)

www.good-display.com 25/34 2.66 inch series

<!-- Page 26 -->

GooDisplay GDEM0266T71WT

10.Typical Operating Sequence
10.1 OTP Operation Flow

Power On(Apply VCI)

(Apply VCI)

Reset the EPD driver

|

Turn on the oscillator clock and

DC/DC regulator to generate the

drive voltage

|

Load image data and update

|
|

Power Off Enter into deep sleep |

www.good-display.com 26/34 2.66 inch series

<!-- Page 27 -->

GooDisplay GDEM0266T71WT

10.2 OTP Operation Reference Program Code

ACTION [ VALUE/DATA [ COMMENT.
POWER ON
delay [ 10ms
PIN CONFIG
RESE# low Hardware reset
dela 200us
RESE# high
delay 200us
Read busy pin Wait for busy low
Command 0x12 [ Software reset
Read busy pin Wait for busy low
SET VOLTAGE AND LOAD LUT
LOAD IMAGE AND UPDATE
Command 0x24 5624b_tes Load ima_e_152/8*296 BW.
Command 0x20
Read busy pin Wait for busy low
Command 0x10 [ Data 0X01 Enter deep sleep mode
POWER OFF

www.good-display.com 27/34 2.66 inch series

<!-- Page 28 -->

GooDisplay GDEM0266T71WT

11. Reliability Test
NO Test items Test condition
| Low-Temperature T =-25°C, 240 h
Storage Test in white pattern
2 High-Temperature T=+70°C, RH=40%, 240h
Storage Test in white pattern
3 High-Temperature Operation T=+25°C, 240h
4 Low-Temperature Operation T=-25°C, 240h
5 _ | High Temperature, High T=60°C, RH=80%, 240h
Humidity Storage Test in white pattern

1 cycle:[-25°C 30min]—[+60 °C 30 min] : 50 cycles

6 Temperature Cycle Test in white pattern

Air+/-4KV;Contact+/-2KV
Contact+/-2KV(HBM C:100pF;R:1.5k ohm)
Contact+/-200V(MM C:200pF;R:0 ohm)

(Naked EPD display,including IC and FPC area)

7 ESD Gun

Note: 1. Stay white pattern for storage and non-operation test.
2. Operation is black-white pattern, the interval is 150s.

www.good-display.com 28/34 2.66 inch series

<!-- Page 29 -->

GooDisplay GDEM0266T71WT

12.Inspection condition
12.1 Environment

Temperature: 23+3°C
Humidity: 55+10%RH
12.2 Illuminance

Brightness: 1200~ 1500LUX;distance:20-30CM;Angle:Relate 45°surround.
12.3 Inspect method

TFT
12.4 Display area

Zone B

Zone A

Viewing area PPC

Ic

12.5 Ghosting test method
Two-color ghosting is measured with following transition from horizontal 2 scale pattern to vertical 2
scale pattern. The listed optical characteristics are only guaranteed under the controller & waveform

provided by DKE.

20min 24h

1) Measurement Instruments: X-rite ilPro

2) Ghosting formula:

W ghosting: AL= Max (4 L(W-W, B-W)) - Min (A L(W-W B-W))
K ghosting: AL= Max (A L(W-B, B-B)) - Min( A L(W-B, B-B))

www.good-display.com 29/34 2.66 inch series

<!-- Page 30 -->

GooDisplay GDEM0266T71WT

12.6 Inspection standard

12.6.1 Electric inspection standard

Defect

NO. Ttem Standard
level

Method Scope

Display complete
Display uniform

@
Black/White

2 spots Ds0.25mm, Allowed
0.25mm<D<0.4mm. Visual
N<4 allowable inspection
D=>0.4mm is not allowed

MI
el, Visual/

L<0.4mm,W<0.Imm Inspection card | Zone A
Show negligible
3 | BIW lines 0.4mm<L< 1.0mm
0.lmm<W<0.4mm
NS<4 allowable
L>1.0mm ,W>0.4mm is not
allowed

1 Display MA

Visual

4 Ghost image Allowed in switching process MI : .
inspection

Flash spots/ Flash spots in switching, Allowed

5 Lareer FPL size | EPL size larger than viewing area, MI Visual/ Zone A
8 Allowed Inspection card | Zone B
6 Display All appointed displays are showed
wrong/Missing | correct Visual
MA eee Zone A
inspection

Short circuit/
7 Circuit break/ | Not Allow
Display abnormal

www.good-display.com 30/34 2.66 inch series

<!-- Page 31 -->

GooDisplay GDEM0266T71WT

12.6.2 Appearance inspection standard

NO. Item Standard Defect Method Scope
level
a
)w
B/W spots /
Forcien bodies pees MI inspection Zone A
Dents DS0.25mm negligible Pr
0.25mm<D<0.4mm NS<4
allowable
D>0.4mm is not allowed
Zone A
2 Glass crack Not Allow MA Visual Zone B
; ; / Microscope Zone A.
3 Dirty Allowed if can be removed MI Zone B
vy
X<3mm,Y<0.5mm And without
affecting the electrode is permissible
4 Chips/Scratch/ MI Visual Zone A
Edge crown / Microscope | Zone B
2mm<X or 2mm<Y Not Allow
—~ iit
—
Leng
W<0.1mm,L<5mm, No harm to the
electrodes and NS2__ allow
7 Visual Zone A
5 TFT Cracks MA / Microscope
Zone B
Not Allow
Dirty/ foreign Visual Zone A/
body Allowed if can be removed/ allow MI / Microscope | Zone B

FPC broken/ Visual
isual
Goldfingers MA / Microscope Zone B

xidation/ scratch
Not Allow

www.good-display.com 31/34 2.66 inch series

<!-- Page 32 -->

GooDisplay GDEM0266T71WT

=r

L<1.0mm,W<0.15mm __ negligible

1.0mm<L<4.0mm Visual
0.15mm<W<0.S5mm MI /Ruler | 70neB
N<4 allowable

L>4.0mm ,W>0.5mm is not

allowed

8 B/W Line

TFT edge bulge | TFT edge bulge:
9 /TFT chromatic X<3mm, Y<0.3mm_ Allowed MI
aberration TFT chromatic aberration :Allowed
D<0.25mm, allow
: 0.25mm<D<0.4mm ,n<4 allow .
Electrostatic Visual

1 : i ve .
0 point D>0.4mm is not allowed MI | Microscope Zone A

Visual Zone A
/ Microscope | Zone B

(nS8 items are allowed within 5 mm
in diameter)

PCB (Circuit area) damaged Not

PCB damaged/ ATL
11 Poor welding/ ow .
Curl PCB Poor welding Not Allow
PCB Curls1%
Edge Adhesives H<PS surface MI Visual
(Including protect film) Edge / Ruler
| adhesives seep in<1/2 Margin width Zone B
12 | Edge glue height/ | [ ength excluding
Edge glue bubble | :dge adhesives bubble: bubble
Width
<1/2 Margin width; Length
<0.5mm. n<5
B Protect film A scratch but not effect protect Visual
function, Allowed Inspection
Thickness <PS surface(With protect film):
Full cover the IC;
A Shape: Visual
14 Silicon glue | The width on the FPC < 0.5mm (Front)| MI Inspection
The width on the FPC<1.0mm (Back)
smooth surface, No obvious raised.
FPL
Warp degree cs 4
1S | (TET substrate) | —S> t MI Ruler
TFT
t=10mm
Color difference
in COM area Visual
16 (Silver point Allowed Inspection

area)

www.good-display.com 32/34 2.66 inch series

<!-- Page 33 -->

GooDisplay GDEM0266171WT

13. Handling, Safety and Environment Requirements

Warning

The display glass may break when it is dropped or bumped on a hard surface. Handle with
care. Should the display break, do not touch the electrophoretic material. In case of contact with
electrophoretic material, wash with water and soap.

Caution

The display module should not be exposed to harmful gases, such as
aalkaligases,whichcorrodeelectronic components. Disassembling the display module.

Disassembling the display module can cause permanent damage and invalidates the warranty
agreements.

Observe general precautions that are‘common to handling delicate electronic components. The glass
can break and front surfaces can easily be damaged. Moreover the display is sensitive to static
electricity and other rough environmental conditions.

Data sheet status

Product specification This data sheet contains final product specifications.

Limiting values

Limiting values given are in accordance with the Absolute Maximum Rating System (IEC
134).Stress above one or more of the limiting values may cause permanent damage to the device.
These are stress ratings only and operation of the device at these or at any other conditions above
those given in the Characteristics sections of the specification is not implied. Exposure to limiting
values for extended periods may affect device reliability.

Application information

Where application information is given, it is advisory and does not form part of the specification.

www.good-display.com 33/34 2.66 inch series

<!-- Page 34 -->

GooDisplay GDEM0266T71WT

14. Packaging

EPD PACKING INSTRUCTION

DKE-QS. D-010

P/N Customer Code Ref. P/N Type | PKG Method | Marking Surface Marks Pull Tape
GLASS Blister BACK None YES:

Packing Materials List 18PCS/LAYER, 20LAYER/CTN, TOTAL 360PCS/CTN.
List Model Materials Q'ty Unie Pull tape:
Carton 7# 417%362#229 mm |corrugate’ 1 | Piece
Inner Carton 7#(INVER) 4008243 #95 nm corrugate) 2 | Piece a =
Blister PET 22 Piece
Thin foam | 270. 46%267.94"(TL. 5-1.8)mm — EPE 20 Piece
mnie 150959040. 075 2 | Piece
Foam board EPE 3 Piece
PULL TAPE 16#5%*T0. 05 360 Piece
Detail:
. . The blister box is rotated
Blister box for placement
Note: there are 20 layers of products, ba Mir ister 7 sisi
divided into 2 inner boxes, and an empty Thin foam = vacuum bag
blister box is placed on the top of each Blister €
inner box, so the number of blister boxes N YA
is 22 Pex boerd aed with rubber band
For 1 1sto 7e IER cARTON
(es ee ee OE INNER BOX LABEL A+
~ > Wa
a0 0007000 1 ( ¢ Va ance cao
$ a :

PUT THO 7H OER CARTON
Ifo Te carton

Cone
p00

Erni
ps

7 carton

Packing belt

oouo%

Ar rear

QUANTITY: 18PCS a>

www.good-display.com 34/34 2.66 inch series

---

# PART II — BOM PART DATASHEETS

# BOM Part Datasheets — Combined Reference

_Compiled 2026-07-31. Full-text extraction of the component (BOM) datasheets. Several JLCPCB part numbers share one generic manufacturer catalog (all resistors, all MLCCs) — these are deduplicated below and the covered parts are listed together. Files marked (OCR) were image-based and machine-read._

## Coverage vs. BOM table

| Part / role | JLCPCB | Value | Datasheet present? |
|---|---|---|---|
| MCU ESP32-C3-MINI-1-N4 | C2838502 | — | Yes — in first combined file (esp32-c3-mini-1) |
| Charger MCP73871-2CC | C5121473 | — | Yes |
| Gauge MAX17048G+T10 | C2682616 | — | Yes |
| USB-C TYPE-C-31-M-12 | C165948 | — | Yes (OCR) |
| FPC AFC07-S24ECA-00 | C262643 | — | Yes |
| Regulator AP2112K-3.3 | C51118 | — | Yes |
| NFC NT3H2111W0FHKH | C710403 | — | Yes (file named by part) |
| Resistor 10k | C17414 | 10k | Yes |
| Resistor 0 | C21189 | 0 | Yes |
| Resistor 5.1K | C23186 | 5.1K | **No separate file** — same Uniroyal catalog as C17414 |
| Resistor 3.3K | C22978 | 3.3K | **No separate file** — same Uniroyal catalog as C17414 |
| Resistor 24K | C23352 | 24K | Yes |
| Resistor 470 | C23179 | 470 | Yes |
| Resistor 2.2 | C17521 | 2.2 | Yes |
| Cap 0.1uF | C28233 | 0.1uF | Yes |
| Cap 10uF | C19702 | 10uF | Yes |
| Cap 1uF | C28323 | 1uF | Yes |
| Cap 4.7uF | C19666 | 4.7uF | Yes |
| Cap 220nF | C21120 | 220nF | Yes |
| Cap TBD (C14) | C1653 | TBD | Yes |
| Cap 1uF X5R | C15849 | 1uF X5R | Yes |
| LED red D2/D3/D4 | C2286 | RED | Yes |
| NMOS SI1304BDL | C7419947 | — | Yes (OCR) |
| Inductor CDRH2D18 | C2454210 | 47µH | Yes |
| Schottky MBR0530 (×3) | C77336 | — | Yes |
| Tactile SW-01/SW-02 | C720477 | — | Yes (OCR) |

**Missing files:** `C23186` (5.1K) and `C22978` (3.3K) — but both are the *same* Uniroyal thick-film chip-resistor catalog already included via C17414, so the datasheet content is effectively covered; you only lack the JLC-specific PDFs.

## Contents

1. MCP73871 — Li-Ion/Li-Po Charge Management + Load Sharing
2. MAX17048/MAX17049 — Fuel Gauge
3. AP2112 — 600mA CMOS LDO Regulator
4. NT3H2111/2211 — NTAG I2C plus (NFC)
5. AFC07-S24ECA-00 — 24-pin FPC Connector
6. TYPE-C-31-M-12 — USB-C Receptacle (OCR)
7. SI1304BDL — N-Channel MOSFET (OCR)
8. CDRH2D18/LD — SMD Power Inductor
9. MBR0530 — Schottky Barrier Diode
10. 0603 Red LED — Kuangtong (approval doc)
11. Tactile Switch SW-01/SW-02 (OCR)
12. Uniroyal Thick Film Chip Resistors (0805) — generic catalog
13. Uniroyal Thick Film Chip Resistors — 0-ohm jumper
14. MLCC Capacitor Catalog — generic (0805 X5R/X7R)

---

# 1. MCP73871 — Li-Ion/Li-Po Charge Management + Load Sharing

> **Role:** Charger — MCP73871-2CC  
> **Covers:** `C5121473` (Charger)

<!-- Page 1 -->

 2008-2022 Microchip Technology Inc. and its subsidiaries
DS20002090F-page 1
MCP73871
Features
• Integrated System Load Sharing and Battery
Charge Management
- Simultaneously Power the System and
Charge the Li-Ion Battery
- Voltage Proportional Current Control (VPCC)
ensures system load has priority over Li-Ion
battery charge current
- Low-Loss Power-Path Management with
Ideal Diode Operation
• Complete Linear Charge Management Controller
- Integrated Pass Transistors
- Integrated Current Sense
- Integrated Reverse Discharge Protection
- Selectable Input Power Sources: USB Port or
AC-DC Wall Adapter
• Preset High Accuracy Charge Voltage Options:
- 4.10V, 4.20V, 4.35V or 4.40V
- ±0.5% Regulation Tolerance
• Constant Current/Constant Voltage (CC/CV)
Operation with Thermal Regulation
• Maximum 1.8A Total Input Current Control
• Resistor Programmable Fast Charge Current
Control: 50 mA to 1A
• Resistor Programmable Termination Set Point
• Selectable USB Input Current Control
- Absolute Maximum: 100 mA (L)/500 mA (H)
• Automatic Recharge
• Automatic End-of-Charge Control
• Safety Timer With Timer Enable/Disable Control
• 0.1C Preconditioning for Deeply Depleted Cells
• Battery Cell Temperature Monitor
• Undervoltage Lockout (UVLO)
• Low Battery Status Indicator (LBO)
• Power Good Status Indicator (PG)
• Charge Status and Fault Condition Indicators
• Numerous Selectable Options Available for a
Variety of Applications:
- Refer to Section 1.0 “Electrical
Characteristics” for Selectable Options
- Refer to the Product Identification System
for Standard Options
• Temperature Range: -40°C to +85°C
• Packaging: 20-Lead QFN (4 mm x 4 mm)
Applications
• GPSs/Navigators
• PDAs and Smart Phones
• Portable Media Players and MP3 Players
• Digital Cameras
• Bluetooth® Headsets
• Portable Medical Devices
• Charge Cradles/Docking Stations
• Toys
Description
The MCP73871 device is a fully integrated linear
solution for system load sharing and Li-Ion/Li-Polymer
battery charge management with AC-DC wall adapter
and USB port power sources selection. It is also
capable of autonomous power source selection
between input and battery. Along with its small physical
size, the low number of required external components
makes
the
device
ideally
suited
for
portable
applications.
The MCP73871 device automatically obtains power for
the system load from a single-cell Li-Ion battery or an
input power source (AC-DC wall adapter or USB port).
The MCP73871 device specifically adheres to the
current drawn limits governed by the USB specification.
With an AC-DC wall adapter providing power to the
system, an external resistor sets the magnitude of 1A
maximum charge current while supporting up to 1.8A
total current for system load and battery charge
current.
The
MCP73871
device
employs
a
constant
current/constant voltage (CC/CV) charge algorithm
with
selectable
charge
termination
point.
To
accommodate new and emerging battery charging
requirements, the constant voltage regulation is fixed
with four available options: 4.10V, 4.20V, 4.35V or
4.40V. The MCP73871 device also limits the charge
current based on the die temperature during high
power or high ambient conditions. This thermal
regulation optimizes the charge cycle time while
maintaining device reliability.
The MCP73871 device includes a low battery indicator,
a power good indicator and two charge status
indicators that allow for outputs with LEDs or
communication
with
host
microcontrollers.
The
MCP73871 device is fully specified over the ambient
temperature range of -40°C to +85°C.
Stand-Alone System Load Sharing and Li-Ion/Li-Polymer Battery Charge
Management Controller

<!-- Page 2 -->

MCP73871
DS20002090F-page 2
 2008-2022 Microchip Technology Inc. and its subsidiaries
Package Types
Typical Application Circuit
IN
 STAT1/LBO
PG
THERM
STAT2
PROG1
IN
OUT
OUT
CE
SEL
PROG3
TE
VBAT
VBAT
VPCC
VSS
VSS
VBAT_SENSE
2
EP
20
1
19 18 17
3
4
12
11
10
9
5
6
7
8
13
14
15
16
21
PROG2
MCP73871
20-Lead QFN*
* Includes Exposed Thermal Pad (EP); see Table 3-1.
STAT1
LBO
IN
OUT
PG
VBAT
Single-Cell
Li-Ion Battery
7
1, 20
8
18, 19
10 µF
10, 11, EP
AC-DC Adapter
         or
    USB Port
STAT2
THERM
VSS
PROG1
PROG3 12
13 RPROG1
6
5
14, 15, 16
470
470
470
2
4.7 µF
System
Load
SEL
TE
PROG2
Hi
Low
Hi
Low
Hi
Low
3
4
9
RPROG3
VPCC
NTC
10 k
Hi
Low
17 CE
4.7 µF
MCP73871 Typical Application

<!-- Page 3 -->

 2008-2022 Microchip Technology Inc. and its subsidiaries
DS20002090F-page 3
MCP73871
Functional Block Diagram
STAT1
PROG1
VBAT
G = 0.001
VSS
Direction
Control
TERM
+
-
+
-
LTVT
+
-
HTVT
THERM
50 µA
UVLO,
REFERENCE,
CHARGE
CONTROL,
TIMER,
AND
STATUS
LOGIC
STAT2
PG
Direction
Control
PROG2
IN
+
-
CURRENT
LIMIT
VREF
+
-
CURRENT
LIMIT
VREF/2

PROG3
+
-
CA
VREF
PRECONDITION
+
-
VREF
+
-
VA
VREF
VREF
SEL
OUT
VREF
TE
0.2
0.2
Ideal
Diode,
Synchronous
Switch
CHRG
+
-
VREF
+
-
VREF
VPCC
CE
VBAT_SENSE
G = 0.001
G = 0.001
G = 0.001
VREF (1.21V)
361k
190k
7k
89k

<!-- Page 4 -->

MCP73871
DS20002090F-page 4
 2008-2022 Microchip Technology Inc. and its subsidiaries
1.0
ELECTRICAL CHARACTERISTICS
Absolute Maximum Ratings(†)
VIN.....................................................................................................................................................................................................7.0V
All Inputs and Outputs w.r.t. .................................................................................................................................VSS–0.3V to VDD+0.3V
(VDD = VIN or VBAT)
Maximum Junction Temperature, TJ ............................................................................................................................. Internally Limited
Storage temperature ..................................................................................................................................................... –65°C to +150°C
ESD protection on all pins
Human Body Model (1.5 k in Series with 100 pF)4 kV
Machine Model (200 pF, No Series Resistance)..............................................................................................................................300V
†
Notice: Stresses above those listed under “Maximum Ratings” may cause permanent damage to the
device. This is a stress rating only and functional operation of the device at those or any other conditions
above those indicated in the operational listings of this specification is not implied. Exposure to maximum
rating conditions for extended periods may affect device reliability.
DC CHARACTERISTICS
Electrical Specifications: Unless otherwise indicated, all limits apply for VIN = VREG + 0.3V to 6V, TA = -40°C to +85°C.
Typical values are at +25°C, VIN = [VREG (typical) + 1.0V]
Parameters
Sym
Min
Typ
Max
Units
Conditions
Supply Input
Supply Voltage
VIN
VREG + 0.3V
—
6
V
Supply Current
ISS
—
2500
3750
µA
Charging
—
260
350
µA
Charge Complete
—
180
300
µA
Standby
—
28
50
µA
Shutdown
(VDD < VBAT – 100 mV or
VDD < VSTOP)
UVLO Start Threshold
VSTART
VREG + 0.05V
VREG + 0.15V
VREG + 0.25V
V
VDD = Low-to-High
UVLO Stop Threshold
VSTOP
VREG – 0.07V
VREG + 0.07V
VREG + 0.17V
V
VDD = High-to-Low
UVLO Hysteresis
VHYS
—
90
—
mV
Voltage Regulation (Constant Voltage Mode)
Regulated
Charge Voltage
VREG
4.080
4.10
4.121
V
VDD = [VREG(typical) + 1V]
IOUT = 10 mA
TA = -5°C to +55°C
4.179
4.20
4.221
V
4.328
4.35
4.372
V
4.378
4.40
4.422
V
Regulated Charge
Voltage Tolerance
VRTOL
–0.5
—
+0.5
%
TA = +25°C
–0.75
—
+0.75
%
TA = -5°C to +55°C
Line Regulation
VBAT/VBAT)
/
VDD|
—
0.08
0.20
%/V
VDD = [VREG(typical) + 1V] to 6V
IOUT = 10 mA
Load Regulation
VBAT/VBAT|
—
0.08
0.18
%
IOUT = 10 mA to 150 mA
VDD = [VREG(typical) + 1V]
Supply Ripple
Attenuation
PSRR
—
-47
—
dB
IOUT = 10 mA, 1 kHz
—
-40
—
dB
IOUT = 10 mA, 10 kHz
Note
1:
The value is ensured by design and not production tested.
2:
The maximum available charge current is also limited by the value set at PROG1 input.

<!-- Page 5 -->

 2008-2022 Microchip Technology Inc. and its subsidiaries
DS20002090F-page 5
MCP73871
Current Regulation (Fast Charge Constant Current Mode)
AC-Adapter
Fast Charge
Current
IREG
90
100
110
mA
PROG1 = 10 k
TA = -5°C to +55°C, SEL = High
900
1000
1100
mA
PROG1 = 1 k
TA = -5°C to +55°C, SEL = High
USB Fast Charge
Current
IREG
80
90
100
mA
PROG2 = Low, SEL = Low,
(Note 2)
TA = -5°C to +55°C
400
450
500
mA
PROG2 = High, SEL = Low,
(Note 2)
TA = -5°C to +55°C
Input Current Limit Control (ICLC)
USB-Port Supply
Current Limit
ILIMIT_USB
80
90
100
mA
PROG2 = Low, SEL = Low
TA = -5°C to +55°C
400
450
500
mA
PROG2 = High, SEL = Low
TA = -5°C to +55°C
AC-DC Adapter Current
Limit
ILIMIT_AC
1500
1650
1800
mA
SEL = High, TA = -5°C to +55°C
Voltage Proportional Charge Control (VPCC - Input Voltage Regulation)
VPCC Input Threshold
VVPCC
—
1.23
—
V
IOUT = 10 mA
TA = -5°C to +55°C
VPCC Input Threshold
Tolerance
VRTOL
–3
—
+3
%
Input Leakage Current
ILK
—
0.01
1
µA
VVPCC = VDD
Precondition Current Regulation (Trickle Charge Constant Current Mode)
Precondition Current
Ratio
IPREG/IREG
7.5
10
12.5
%
PROG1 = 1.0 k to 10 k
TA = -5°C to +55°C
Precondition Current
Threshold Ratio
VPTH/VREG
69
72
75
%
VBAT Low-to-High
Precondition Hysteresis
VPHYS
—
105
—
mV
VBAT High-to-Low
Automatic Charge Termination Set Point
Charge Termination
Current Ratio
ITERM
75
100
125
mA
PROG3 = 10 k
TA = -5°C to +55°C
7.5
10
12.5
mA
PROG3 = 100 k
TA = -5°C to +55°C
Automatic Recharge
Recharge Voltage
Threshold Ratio
VRTH
VREG – 0.21V
VREG – 0.15V
VREG – 0.09V
V
VBAT High-to-Low
IN-to-OUT Pass Transistor ON-Resistance
ON-Resistance
RDS_ON
—
200
—
m
VDD = 4.5V, TJ = 105°C
Charge Transistor ON-Resistance
DC CHARACTERISTICS (CONTINUED)
Electrical Specifications: Unless otherwise indicated, all limits apply for VIN = VREG + 0.3V to 6V, TA = -40°C to +85°C.
Typical values are at +25°C, VIN = [VREG (typical) + 1.0V]
Parameters
Sym
Min
Typ
Max
Units
Conditions
Note
1:
The value is ensured by design and not production tested.
2:
The maximum available charge current is also limited by the value set at PROG1 input.

<!-- Page 6 -->

MCP73871
DS20002090F-page 6
 2008-2022 Microchip Technology Inc. and its subsidiaries
ON-Resistance
RDSON_
—
200
—
m
VDD = 4.5V, TJ = 105°C
BAT-to-OUT Pass Transistor ON-Resistance
ON-Resistance
RDS_ON
—
200
—
m
VDD = 4.5V, TJ = 105°C
Battery Discharge Current
Output Reverse
Leakage Current
IDISCHARGE
—
30
40
µA
Shutdown
(VBAT < VDD < VUVLO)
—
30
40
µA
Shutdown (0 < VDD < VBAT)
—
30
40
µA
VBAT = Power Out, No Load
—
–6
–13
µA
Charge Complete
Status Indicators - STAT1 (LBO), STAT2, PG
Sink Current
ISINK
—
16
35
mA
Low Output Voltage
VOL
—
0.4
1
V
ISINK = 4 mA
Input Leakage Current
ILK
—
0.01
1
µA
High Impedance, VDD on pin
Low Battery Indicator (LBO)
Low Battery Detection
Threshold
VLBO
—
Disable
—
VBAT > VIN, PG = High-Z
TA = -5°C to +55°C
2.85
3.0
3.15
V
2.95
3.1
3.25
V
3.05
3.2
3.35
V
Low Battery Detection
Hysteresis
VLBO_HYS
—
150
—
mV
VBAT Low-to-High
PROG1 Input (PROG1)
Charge Impedance
Range
RPROG
1
—
20
k
PROG3 Input (PROG3)
Termination Impedance
Range
RPROG
5
—
100
k
PROG2 Input (PROG2)
Input High Voltage Level
VIH
1.8
—
—
V
Input Low Voltage Level
VIL
—
—
0.8
V
Input Leakage Current
ILK
—
0.01
1
µA
VPROG2 = VDD
Timer Enable (TE)
Input High Voltage Level
VIH
1.8
—
—
V
Note 1
Input Low Voltage Level
VIL
—
—
0.8
V
Note 1
Input Leakage Current
ILK
—
0.01
1
µA
VTE = VDD
DC CHARACTERISTICS (CONTINUED)
Electrical Specifications: Unless otherwise indicated, all limits apply for VIN = VREG + 0.3V to 6V, TA = -40°C to +85°C.
Typical values are at +25°C, VIN = [VREG (typical) + 1.0V]
Parameters
Sym
Min
Typ
Max
Units
Conditions
Note
1:
The value is ensured by design and not production tested.
2:
The maximum available charge current is also limited by the value set at PROG1 input.

<!-- Page 7 -->

 2008-2022 Microchip Technology Inc. and its subsidiaries
DS20002090F-page 7
MCP73871
Chip Enable (CE)
Input High Voltage Level
VIH
1.8
—
—
V
Input Low Voltage Level
VIL
—
—
0.8
V
Input Leakage Current
ILK
—
0.01
1
µA
VCE = VDD
Input Source Selection (SEL)
Input High Voltage Level
VIH
1.8
—
—
V
Input Low Voltage Level
VIL
—
—
0.8
V
Input Leakage Current
ILK
—
0.01
1
µA
VSEL = VDD
Thermistor Bias
Thermistor Current
Source
ITHERM
47
50
53
µA
2 k< RTHERM < 50 k
Thermistor Comparator
Upper Trip Threshold
VT1
1.20
1.24
1.26
V
VT1 Low-to-High
Upper Trip Point
Hysteresis
VT1HYS
—
-40
—
mV
Lower Trip Threshold
VT2
0.23
0.25
0.27
V
VT2 High-to-Low
Lower Trip Point
Hysteresis
VT2HYS
—
40
—
mV
Thermal Shutdown
Die Temperature
TSD
—
150
—
C
Die Temperature
Hysteresis
TSDHYS
—
10
—
C
DC CHARACTERISTICS (CONTINUED)
Electrical Specifications: Unless otherwise indicated, all limits apply for VIN = VREG + 0.3V to 6V, TA = -40°C to +85°C.
Typical values are at +25°C, VIN = [VREG (typical) + 1.0V]
Parameters
Sym
Min
Typ
Max
Units
Conditions
Note
1:
The value is ensured by design and not production tested.
2:
The maximum available charge current is also limited by the value set at PROG1 input.

<!-- Page 8 -->

MCP73871
DS20002090F-page 8
 2008-2022 Microchip Technology Inc. and its subsidiaries
AC CHARACTERISTICS
Electrical Specifications: Unless otherwise indicated, all limits apply for VIN = 4.6V to 6V.
Typical values are at +25°C, VDD = [VREG (typical) + 1.0V]
Parameters
Sym
Min
Typ
Max
Units
Conditions
UVLO Start Delay
tSTART
—
—
5
ms
VDD Low-to-High
Current Regulation
Transition Time Out of Precondition
tDELAY
—
—
10
ms
VBAT < VPTH to VBAT > VPTH
Current Rise Time Out of Precondition
tRISE
—
—
10
ms
IOUT Rising to 90% of IREG
Precondition Comparator Filter Time
tPRECON
0.4
1.3
3.2
ms
Average VBAT Rise/Fall
Termination Comparator Filter Time
tTERM
0.4
1.3
3.2
ms
Average IOUT Falling
Charge Comparator Filter Time
tCHARGE
0.4
1.3
3.2
ms
Average VBAT Falling
Thermistor Comparator Filter Time
tTHERM
0.4
1.3
3.2
ms
Average THERM Rise/Fall
Elapsed Timer
Elapsed Timer Period
tELAPSED
—
0
—
Hours
3.6
4.0
4.4
Hours
5.4
6.0
6.6
Hours
7.2
8.0
8.8
Hours
Status Indicators
Status Output Turn-off
tOFF
—
—
500
µs
ISINK = 1 mA to 0 mA
Status Output Turn-on
tON
—
—
500
µs
ISINK = 0 mA to 1 mA
Note
1:
Internal safety timer is tested based on internal oscillator frequency measurement.
TEMPERATURE SPECIFICATIONS
Electrical Specifications: Unless otherwise indicated, all limits apply for VIN = 4.6V to 6V.
Typical values are at +25°C, VDD = [VREG (typical) + 1.0V]
Parameters
Sym
Min
Typ
Max
Units
Conditions
Temperature Ranges
Specified Temperature Range
TA
-40
—
+85
°C
Operating Temperature Range
TJ
-40
—
+125
°C
Storage Temperature Range
TA
-65
—
+150
°C
Thermal Package Resistances
Thermal Resistance, 20LD-QFN, 4x4
JA
—
50
—
°C/W
4-Layer JC51-7 Standard Board,
Natural Convection
JC
—
8
—
—

<!-- Page 9 -->

 2008-2022 Microchip Technology Inc. and its subsidiaries
DS20002090F-page 9
MCP73871
2.0
TYPICAL PERFORMANCE CURVES
Note: Unless otherwise indicated, VIN = [VREG(typical) + 1V], IOUT = 10 mA and TA = +25°C, Constant Voltage mode.
FIGURE 2-1:
Battery Regulation Voltage
(VBAT) vs. Supply Voltage (VDD).
FIGURE 2-2:
Battery Regulation Voltage
(VBAT) vs. Ambient Temperature (TA).
FIGURE 2-3:
Charge Current (IOUT) vs.
Programming Resistor (RPROG).
FIGURE 2-4:
Charge Current (IOUT) vs.
Battery Regulation Voltage (VBAT).
FIGURE 2-5:
Output Leakage Current
(IDISCHARGE) vs. Ambient Temperature (TA).
FIGURE 2-6:
Output Leakage Current
(IDISCHARGE) vs. Battery Regulation Voltage
(VBAT).
Note:
The graphs and tables provided following this note are a statistical summary based on a limited number of
samples and are provided for informational purposes only. The performance characteristics listed herein
are not tested or guaranteed. In some graphs or tables, the data presented may be outside the specified
operating range (e.g., outside specified power supply range) and therefore outside the warranted range.
4.176
4.184
4.192
4.200
4.208
4.216
4.224
4.232
4.240
4.6
4.9
5.1
5.4
5.6
5.9
Supply Voltage (V)
Battery Regulation Voltage (V)
Temperature = +25°C
IOUT= 100 mA
IOUT= 500 mA
IOUT= 900 mA
IOUT= 10 mA
4.190
4.198
4.206
4.214
4.222
4.230
4.238
-45
-30
-15
0
15
30
45
60
75
90
Ambient Temperature (°C)
Battery Regulation Voltage (V)
IOUT = 10 mA
IOUT = 100 mA
IOUT = 500 mA
IOUT = 1000 mA
0
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
0
0.5
1
1.5
2
2.5
3
3.5
4
4.5
0
0.2
0.4
0.6
0.8
1
Time (Minute)
Charge Voltage (V)
0
0.2
0.4
0.6
0.8
1
1.2
1.4
1.6
1.8
2
Charge Current (A)
Preconditioning
Preconditioning Threshold Voltage
Fast Charge (Constant Current)
MCP73871
VDD = 5.2V
RPROG1 = 1 kΩ
RPROG3 = 25 kΩ

<!-- Page 14 -->

MCP73871
DS20002090F-page 14
 2008-2022 Microchip Technology Inc. and its subsidiaries
3.0
PIN DESCRIPTION
The descriptions of the pins are listed in Table 3-1.
3.1
Power Supply Input (IN - also
referred to as VIN)
A
supply
voltage
of
VREG + 0.3V
to
6V
is
recommended. Bypass to VSS with a minimum of
4.7 µF.
3.2
System Output Terminal (OUT -
also referred to as VOUT)
The MCP73871 device powers the system via output
terminals while independently charging the battery.
This feature reduces the charge and discharge cycles
on the battery, allowing proper charge termination and
the system to run with an absent or defective battery
pack. It also gives the system priority on input power,
allowing the system to power-up with deeply depleted
battery packs. Bypass to VSS with a minimum of 4.7 µF
is recommended.
3.3
Voltage Proportional Charge
Control (VPCC)
If the voltage on the IN pin drops to a preset value
determined by the threshold established at the VPCC
input due to a limited amount of input current or input
source impedance, the battery charging current is
reduced. If possible, further demand from the system is
supported by the battery. To enable this feature, simply
supply 1.23V or greater to the VPCC pin. This feature
can be disabled by connecting the VPCC pin to IN.
For example, a system is designed with a 5.5V rated
DC power supply with ±0.5V tolerance. The worst
condition of 5V is selected, which is used to calculate
the VPCC supply voltage with divider.
TABLE 3-1:
PIN FUNCTION TABLE
Pin
Number
Symbol
I/O
Function
1, 20
OUT
O
System Output Terminal
2
VPCC
I
Voltage proportional charge control
3
SEL
I
Input type selection (low for USB port, high for AC-DC adapter)
4
PROG2
I
USB port input current limit selection when SEL = Low
(Low = 100 mA, High = 500 mA)
5
THERM
I/O
Thermistor monitoring input and bias current
6
PG
O
Power Good Status Output (Open-Drain)
7
STAT2
O
Charge Status Output 2 (Open-Drain)
8
STAT1/LBO
O
Charge Status Output 1 (Open-Drain). Low battery output indicator when
VBAT > VIN
9
TE
I
Timer Enable; Enables Safety Timer when active-low
10, 11, EP
VSS
—
Battery Management 0V Reference. EP (Exposed Thermal Pad).
There is an internal electrical connection between the exposed thermal pad and
VSS. The EP must be connected to the same potential as the VSS pin on the
Printed Circuit Board (PCB)
12
PROG3
I/O
Termination set point for both AC-DC adapter and USB port
13
PROG1
I/O
Fast charge current regulation setting with SEL = high. Preconditioning set point
for both USB port and AC-DC adapter
14, 15
VBAT
I/O
Battery Positive Input and Output connection
16
VBAT_SENSE
I/O
Battery Voltage Sense
17
CE
I
Device Charge Enable; Enabled when CE = high
18, 19
IN
I
Power Supply Input
Legend:
I = Input, O = Output, I/O = Input/Output
Note:
To ensure proper operation, the input pins must not allow floating and should always tie to either high or low.

<!-- Page 15 -->

 2008-2022 Microchip Technology Inc. and its subsidiaries
DS20002090F-page 15
MCP73871
The voltage divider equation is shown below:
EQUATION 3-1:
The calculated R1 equals 337.2 kwhen 110 k is
selected for R2. The 330 k resistor is selected for R1
to build the voltage divider for VPCC.
FIGURE 3-1:
Voltage Divider Example.
3.4
Input Source Type Selection (SEL)
The input source type selection (SEL) pin is used to
select the input power source for the input current limit
control feature. With the SEL input high, the
MCP73871 device is capable of providing 1.65 (typical)
total amperes to be shared by the system load and Li-
Ion battery charging. The MCP73871 device limits the
input current up to 1.8A. When SEL active-low, the
input source is designed to provide system power and
Li-Ion battery charging from a USB Port input while
adhering to the current limits governed by the USB
specification.
3.5
Battery Management 0V Reference
(VSS)
Connect to the negative terminal of the battery, system
load and input supply.
3.6
Battery Charge Control Output
(VBAT)
Connect to positive terminal of the Li-Ion/Li-Polymer
battery. Bypass to VSS with a minimum of 4.7 µF to
ensure loop stability when the battery is disconnected.
3.7
Battery Voltage Sense
(VBAT_SENSE)
Connect to the positive terminal of the battery. A
precision internal voltage sense regulates the final
voltage on this pin to VREG.
3.8
Charge Current Regulation Set
(PROG1)
The maximum constant charge current is set by placing
a resistor from PROG1 to VSS. PROG1 sets the
maximum constant charge current for both the AC-DC
adapter and USB port. However, the actual charge
current is based on the input source type and the
system load requirement.
3.9
USB-Port Current Regulation Set
(PROG2)
The MCP73871 device USB-Port current regulation set
input (PROG2) is a digital input selection. A logic Low
selects a one unit load input current from the USB port
(100 mA) while a logic high selects a five unit load input
current from the USB port (500 mA).
3.10
Charge Status Output 1 (STAT1)
STAT1 is an open-drain logic output for connection to
an LED for charge status indication. Alternatively, a
pull-up resistor can be applied for interfacing to a host
microcontroller. Refer to Table 5-1 for a summary of the
status output during a charge cycle.
3.11
Charge Status Output 2 (STAT2)
STAT2 is an open-drain logic output for connection to
an LED for charge status indication. Alternatively, a pull
up resistor can be applied for interfacing to a host
microcontroller. Refer to Table 5-1 for a summary of the
status output during a charge cycle.
3.12
Power Good (PG)
The power good (PG) is an open-drain logic output for
input power supply indication. The PG output is low
whenever the input to the MCP73871 device is above
the UVLO threshold and greater than the battery
voltage. The PG output may be used with an LED or as
an interface to a host microcontroller to signal when an
input power source is supplying power to the system
and the battery. Refer to Table 5-1 for a summary of the
status output during a charge cycle.
VVPCC
R2
R1
R2
+
------------------




VIN
1.23V
=

=
1.23V
110k
110k
R1
+
-----------------------------




5V

=
R1
337.2k
=
330 k
110 k
VIN
VPCC

<!-- Page 16 -->

MCP73871
DS20002090F-page 16
 2008-2022 Microchip Technology Inc. and its subsidiaries
3.13
Low Battery Output (LBO)
STAT1 also serves as low battery output (LBO) if the
selected MCP73871 is equipped with this feature. It
provides an indication to the system or end user when
the Li-Ion battery voltage level is low. The LBO feature
is enabled when the system is running from the Li-Ion
battery. The LBO output may be used with an LED or
as an interface to a host microcontroller to signal when
the system is operating from the battery and the battery
is running low on charge. Refer to Table 5-1 for a
summary of the status output during a charge cycle.
3.14
Timer Enable (TE)
The timer enable (TE) feature is used to enable or
disable the internal timer. A low signal enables and a
high signal disables the internal timer on this pin. The
TE input can be used to disable the timer when the sys-
tem load is substantially limiting the available supply
current to charge the battery. The TE input is
compatible with 1.8V logic. The TE signal asserted low
will stop the timer but not Reset it. The timer can be
reset by cycling the CE pin. The second character of
the operational output options code indicates the Timer
interval: A = disable, B = 4 hours, C = 6 hours and D =
8 hours.
3.15
Battery Temperature Monitor
(THERM)
The MCP73871 device continuously monitors battery
temperature during a charge cycle by measuring the
voltage between the THERM and VSS pins. An internal
50 µA current source provides the bias for most
common 10 k Negative Temperature Coefficient
(NTC) thermistors. The MCP73871 device compares
the voltage at the THERM pin to factory set thresholds
of 1.24V and 0.25V, typically. Once a voltage outside
the thresholds is detected during a charge cycle, the
MCP73871 device immediately suspends the charge
cycle. The charge cycle resumes when the voltage at
the THERM pin returns to the normal range. The
charge temperature window can be set by placing fixed
value resistors in series-parallel with a thermistor.
Refer to Section 6.0 “Applications” for calculations
of resistance values.
3.16
Charge Enable (CE)
With the CE input Low, the Li-Ion battery charger
feature of the MCP73871 is disabled. The charger
feature is enabled when CE is active-high. Allowing the
CE pin to float during the charge cycle may cause
system instability. The CE input is compatible with 1.8V
logic. Refer to Section 6.0 “Applications” for various
applications in designing with CE features.
3.17
Exposed Thermal Pad (EP)
An internal electrical connection exists between the
Exposed Thermal Pad (EP) and the VSS pin. They must
be connected to the same potential on the Printed
Circuit Board (PCB).
Note:
The built-in safety timer is available for the
following options: 4 HR, 6 HR and 8 HR.

<!-- Page 17 -->

 2008-2022 Microchip Technology Inc. and its subsidiaries
DS20002090F-page 17
MCP73871
4.0
DEVICE OVERVIEW
The MCP73871 device is a simple but fully integrated
linear charge management controller with system load
sharing feature. Figure 4-1 depicts the operational flow
algorithm.
FIGURE 4-1:
MCP73871 Device Flow Chart.
SHUTDOWN MODE *
 VDD < VUVLO
 VDD < VBAT
STAT1 = Hi-Z
STAT2 = Hi-Z
PG = Hi-Z
PRECONDITIONING  MODE
Charge Current = IPREG
STAT1 = LOW
STAT2 = Hi-Z
PG = LOW
Timer Reset
CONSTANT VOLTAGE MODE
Charge Voltage = VREG
STAT1 = LOW
PG = LOW
VBAT > VPTH
CHARGE COMPLETE MODE
No Charge Current
STAT1 = Hi-Z
STAT2 = LOW
PG = LOW
Timer Reset
IBAT < ITERM
Timer Expired
VBAT < VPTH
STANDBY MODE *
VBAT > (VREG + 100 mV)
CE = LOW
STAT1 = Hi-Z
STAT2 = Hi-Z
PG = LOW
* Continuously Monitored
TEMPERATURE FAULT
No Charge Current
STAT1 = LOW
STAT2 = LOW
PG = LOW
Timer Suspended
TIMER FAULT
No Charge Current
STAT1 = LOW
STAT2 = LOW
PG = LOW
Timer Expired
LBO *
VIN < VBAT
STAT1 = LOW
STAT2 = Hi-Z
PG = Hi-Z
VBAT > VPTH
STAT2 = Hi-Z
Timer Reset
FAST CHARGE MODE
Charge Current = IREG
STAT1 = LOW
STAT2 = Hi-Z
PG = LOW
Timer Enabled

<!-- Page 18 -->

MCP73871
DS20002090F-page 18
 2008-2022 Microchip Technology Inc. and its subsidiaries
Table 4-1 shows the chip behavior based upon the operating conditions.
TABLE 4-1:
CHIP BEHAVIOR REFERENCE TABLE
4.1
UnderVoltage Lockout (UVLO)
An internal undervoltage lockout (UVLO) circuit
monitors the input voltage and keeps the charger in
shutdown mode until the input supply rises above the
UVLO threshold.
In the event a battery is present when the input power
is applied, the input supply must rise approximately
100 mV above the battery voltage before the
MCP73871 device becomes operational.
The UVLO circuit places the device in Shutdown mode
if the input supply falls to within approximately 100 mV
of the battery voltage.
The UVLO circuit is always active. At any time the input
supply is below the UVLO threshold or falls within
approximately 100 mV of the voltage at the VBAT pin,
the MCP73871 device is placed in Shutdown mode.
During any UVLO condition, the battery reverse
discharge current is less than 2 µA.
4.2
System Load Sharing
The system load sharing feature gives the system
output pin (OUT) priority, allowing the system to power-
up with deeply depleted battery packs.
With the SEL input active-low, the MCP73871 device is
designed to provide system power and Li-Ion battery
charging from a USB input while adhering to the current
limits governed by the USB specification.
With the SEL input active-high, the MCP73871 device
limits the total supply current to 1.8A (system power
and charge current combined).
FIGURE 4-2:
System Load Sharing
Diagram.
VIN ? VBAT
VIN > 2V
VIN > UVLO
CE
VBAT ? VOUT
State
Bias + VREF
Thermal
Block
Synchronous
Diode
System Power FET
(Figure 4-2)
Charge
1
VBAT > VIN
0
0
0
—
Shutdown
OFF
OFF
2
1
Battery
powered
system
ON
3
VIN > VBAT
0
0
X
—
Shutdown
OFF
4
VIN > VBAT
1
0
0
—
Shutdown
ON
OFF
OFF
5
1
Battery
powered
system
ON
6
1
0
VBAT < VOUT
Standby
ON
OFF
ON
OFF
7
VBAT > VOUT
IN + BAT
powered
system
ON
8
1
VBAT < VOUT
IN powered,
Charge
possible
OFF
ON/OFF
9
VBAT > VOUT
IN + BAT
powered
system
ON
OFF
0.2
Ideal
Diode,
Synchronous
Switch
Direction
Control
0.2
Current
Limit
Direction
Control
Charge
FET
System
Power
FET
VBAT
IN
OUT
Charge
Control

<!-- Page 19 -->

 2008-2022 Microchip Technology Inc. and its subsidiaries
DS20002090F-page 19
MCP73871
4.3
Charge Qualification
For a charge cycle to begin, all UVLO conditions must
be met and a battery or output load must be present.
A charge current programming resistor must be
connected from PROG1 to VSS when SEL = high.
When SEL = low, PROG2 needs to be tied high or low
for proper operation.
4.4
Preconditioning
If the voltage at the VBAT pin is less than the
preconditioning threshold, the MCP73871 device
enters a preconditioning mode. The preconditioning
threshold is factory set. Refer to Section 1.0
“Electrical
Characteristics”
for
preconditioning
threshold options.
In this mode, the MCP73871 device supplies 10% of
the fast charge current (established with the value of
the resistor connected to the PROG1 pin) to the
battery.
When the voltage at the VBAT pin rises above the
preconditioning threshold, the MCP73871 device
enters the Constant Current (fast charge) mode.
4.5
Constant Current Mode – Fast
Charge
During the Constant Current mode, the programmed
charge current is supplied to the battery or load. The
charge current is established using a single resistor
from PROG1 to VSS. The program resistor and the
charge current are calculated using the following
equation:
EQUATION 4-1:
Constant Current mode is maintained until the voltage
at the VBAT pin reaches the regulation voltage, VREG.
When Constant Current mode is invoked, the internal
timer is reset.
4.5.1
TIMER EXPIRED DURING
CONSTANT CURRENT - FAST
CHARGE MODE
If the internal timer expires before the recharge voltage
threshold is reached, a timer fault is indicated and the
charge cycle terminates. The MCP73871 device
remains in this condition until the battery is removed. If
the battery is removed, the MCP73871 device enters
the Standby mode where it remains until a battery is
reinserted.
4.6
Constant Voltage Mode
When the voltage at the VBAT pin reaches the
regulation voltage, VREG, constant voltage regulation
begins. The regulation voltage is factory set to 4.10V
or 4.20V with a tolerance of ±0.5%.
4.7
Charge Termination
The Constant Voltage mode charge cycle terminates
either when the average charge current diminishes
below a threshold established by the value of the
resistor connected from PROG3 to VSS or when the
internal charge timer expires. When the charge cycle
terminates due to a fully charged battery, the charge
current is latched off and the MCP73871 device enters
the Charge Complete mode. A 1 ms filter time on the
termination comparator ensures that transient load
conditions do not result in premature charge cycle
termination. The timer period is factory set and can be
disabled.
Refer
to
Section 1.0
“Electrical
Characteristics” for timer period options.
The program resistor and the charge current are
calculated using the following equation:
EQUATION 4-2:
The recommended PROG3 resistor values are
between 5 k and 100 k.
4.8
Automatic Recharge
The MCP73871 device continuously monitors the
voltage at the VBAT pin in the Charge Complete mode.
If the voltage drops below the recharge threshold,
another charge cycle begins and current is supplied
again to the battery or load. The recharge threshold is
factory
set.
Refer
to
Section 1.0
“Electrical
Characteristics” for recharge threshold options.
IREG
1000V
RPROG1
-------------------
=
Where:
RPROG
=
kilo-ohms (k
IREG
=
milliampere (mA)
Note:
Charge
termination
and
automatic
recharge
features
avoid
constantly
charging Li-Ion batteries, resulting in
prolonged battery life while maintaining
full cell capacity.
ITERMINATION
1000V
RPROG3
-------------------
=
Where:
RPROG
=
kilo-ohms (k
IREG
=
milliampere (mA)

<!-- Page 20 -->

MCP73871
DS20002090F-page 20
 2008-2022 Microchip Technology Inc. and its subsidiaries
4.9
Thermal Regulation
The MCP73871 device limits the charge current based
on the die temperature. The thermal regulation
optimizes the charge cycle time while maintaining
device reliability. Figure 4-3 depicts the thermal
regulation for the MCP73871 device. Refer to
Section 1.0 “Electrical Characteristics” for thermal
package resistances and Section 6.1.1.2 “Thermal
Considerations” for calculating power dissipation.
.
FIGURE 4-3:
Thermal Regulation.
4.10
Thermal Shutdown
The MCP73871 device suspends charge if the die
temperature exceeds 150°C. Charging resumes when
the die temperature has cooled by approximately 10°C.
The thermal shutdown is a secondary safety feature in
the event that there is a failure within the thermal
regulation circuitry.
4.11
Temperature Qualification
The MCP73871 device continuously monitors battery
temperature during a charge cycle by measuring the
voltage between the THERM and VSS pins. An internal
50 µA current source provides the bias for most
common 10 k NTC thermistors. The MCP73871
device compares the voltage at the THERM pin to
factory set thresholds of 1.24V and 0.25V, typically.
Once a voltage outside the thresholds is detected
during a charge cycle, the MCP73871 device
immediately
suspends
the
charge
cycle.
The
MCP73871 device suspends charging by turning off
the charge pass transistor and holding the timer value.
The charge cycle resumes when the voltage at the
THERM pin returns to the normal range.
4.12
Voltage Proportional Charge
Control (VPCC)
If the voltage on the IN pin drops to a preset value
determined by the threshold established at the VPCC
input due to a limited amount of input current or input
source impedance, the battery charging current is
reduced. The VPCC control tries to reach a steady
state condition where the system load has priority and
the battery is charged with the remaining current.
Therefore, if the system demands more current than
the input can provide, the ideal diode becomes
forward-biased and the battery may supplement the
input current to the system load.
The VPCC sustains the system load as its highest
priority. It does this by reducing the noncritical charge
current while maintaining the maximum power output of
the adapter. Further demand from the system is
supported by the battery, if possible.
The VPCC feature functions identically for USB port or
AC-DC adapter inputs. This feature can be disabled by
connecting the VPCC to IN pin.
4.13
Input Current Limit Control (ICLC)
If the input current threshold is reached, then the
battery charging current is reduced. The ICLC tries to
reach a steady state condition where the system load
has priority and the battery is charged with the
remaining current. No active control limits the current
to the system. Therefore, if the system demands more
current than the input can provide or the ICLC is
reached, the ideal diode becomes forward biased and
the battery may supplement the input current to the
system load.
The ICLC sustains the system load as its highest
priority. This is done by reducing the non-critical charge
current while adhering to the current limits governed by
the USB specification or the maximum AC-DC adapter
current supported. Further demand from the system is
supported by the battery, if possible.
FIGURE 4-4:
Input Current Limit Control -
USB Port.

&KDUJH&XUUHQW
P$

-XQFWLRQ7HPSHUDWXUH
&

9'' 9
5352* Nȍ
-200
-100
0
100
200
300
400
500
600
700
0
100
200
300
400
500
600
700
Load Current (mA)
Current (mA)
Input Current
Battery Current
Load Current
Ideal
Diode

<!-- Page 21 -->

 2008-2022 Microchip Technology Inc. and its subsidiaries
DS20002090F-page 21
MCP73871
5.0
DETAILED DESCRIPTION
5.1
Analog Circuitry
5.1.1
LOAD SHARING AND LI-ION
BATTERY MANAGEMENT INPUT
SUPPLY (VIN)
The VIN input is the input supply to the MCP73871
device. The MCP73871 device can be supplied by
either AC Adapter (VAC) or USB Port (VUSB) with SEL
pin. The MCP73871 device automatically powers the
system with the Li-Ion battery when the VIN input is not
present.
5.1.2
FAST CHARGE CURRENT
REGULATION SET (PROG1)
For the MCP73871 device, the charge current
regulation can be scaled by placing a programming
resistor (RPROG1) from the PROG1 pin to VSS. The
program resistor and the charge current are calculated
using the following equation:
EQUATION 5-1:
The fast charge current is set for maximum charge
current from AC-DC adapter and USB port. The
preconditioning current is 10% (0.1C) of the fast charge
current.
5.1.3
BATTERY CHARGE CONTROL
OUTPUT (VBAT)
The battery charge control output is the drain terminal
of an internal P-channel MOSFET. The MCP73871
device
provides
constant
current
and
voltage
regulation to the battery pack by controlling this
MOSFET in the linear region. The battery charge
control output should be connected to the positive
terminal of the battery pack.
5.1.4
TEMPERATURE QUALIFICATION
(THERM)
The MCP73871 device continuously monitors battery
temperature during a charge cycle by measuring the
voltage between the THERM and VSS pins. An internal
50 µA current source provides the bias for most
common
10 k
NTC
or
Positive Temperature
Coefficient (PTC) thermistors.The current source is
controlled,
avoiding
measurement
sensitivity
to
fluctuations in the supply voltage (VDD). The
MCP73871 device compares the voltage at the
THERM pin to factory set thresholds of 1.24V and
0.25V, typically. Once a voltage outside the thresholds
is detected during a charge cycle, the MCP73871
device immediately suspends the charge cycle.
The MCP73871 device suspends the charge by turning
off the pass transistor and holding the timer value. The
charge cycle resumes when the voltage at the THERM
pin returns to the normal range.
If temperature monitoring is not required, place a
standard 10 k resistor from THERM to VSS.
5.2
Digital Circuitry
5.2.1
STATUS INDICATORS AND POWER
GOOD (PG)
The charge status outputs have two different states:
Low-Impedance (L) and High-Impedance (High-Z).
The charge status outputs can be used to illuminate
LEDs. Optionally, the charge status outputs can be
used as an interface to a host microcontroller. Table 5-
1 summarizes the state of the status outputs during a
charge cycle.
TABLE 5-1:
STATUS OUTPUTS
IREG
1000V
RPROG1
-------------------
=
Where:
RPROG
=
kilo-ohms (k
IREG
=
milliampere (mA)
CHARGE CYCLE STATE
STAT1
STAT2
PG
Shutdown (VDD = VBAT)
High-Z
High-Z
High-Z
Shutdown (VDD = IN)
High-Z
High-Z
L
Shutdown (CE = L)
High-Z
High-Z
L
Preconditioning
L
High-Z
L
Constant Current
L
High-Z
L
Constant Voltage
L
High-Z
L
Charge Complete - Standby
High-Z
L
L
Temperature Fault
L
L
L
Timer Fault
L
L
L
Low Battery Output
L
High-Z
High-Z
No Battery Present
High-Z
High-Z
L
No Input Power Present
High-Z
High-Z
High-Z

<!-- Page 22 -->

MCP73871
DS20002090F-page 22
 2008-2022 Microchip Technology Inc. and its subsidiaries
5.2.2
AC-DC ADAPTER AND USB PORT
POWER SOURCE REGULATION
SELECT (SEL)
With the SEL input low, the MCP73871 device is
designed to provide system power and Li-Ion battery
charging from a USB input while adhering to the current
limits governed by the USB specification. The host
microcontroller has the option to select either
a 100 mA (L) or a 500 mA (H) current limit based on
the PROG2 input. With the SEL input high, the
MCP73871 device limits the input current to 1.8A. The
programmed charge current is established using a
single resistor from PROG1 to VSS when driving SEL
high.
5.2.3
USB PORT CURRENT
REGULATION SELECT (PROG2)
Driving the PROG2 input to a logic low selects the low
USB port source current setting (maximum 100 mA).
Driving the PROG2 input to a logic high selects the high
USB port source current setting (maximum 500 mA).
5.2.4
POWER GOOD (PG)
The power good (PG) option is a pseudo open-drain
output. The PG output can sink current, but not source
current. The PG output must not be pulled up higher
than VIN because there is a diode path back to VIN. The
PG output is low whenever the input to the MCP73871
device is above the UVLO threshold and greater than
the battery voltage. The PG output can be used as an
indication to the system that an input source other than
the battery is supplying power.
5.2.5
TIMER ENABLE (TE) OPTION
The timer enable (TE) input option is used to enable or
disable the internal timer. A low signal on this pin
enables the internal timer and a high signal disables
the internal timer. The TE input can be used to disable
the timer when the charger is supplying current to
charge the battery and power the system load. The TE
input is compatible with 1.8V logic.

<!-- Page 23 -->

 2008-2022 Microchip Technology Inc. and its subsidiaries
DS20002090F-page 23
MCP73871
6.0
APPLICATIONS
The MCP73871 device is designed to operate in
conjunction
with
a
host
microcontroller
or
in
stand-alone applications. The MCP73871 device
provides the preferred charge algorithm for Lithium-Ion
and Lithium-Polymer cells. The algorithm uses
Constant Current mode followed by Constant Voltage
mode. Figure 6-1 depicts a typical stand-alone
MCP73871 application circuit, while Figure 6-2 and
Figure 6-3 depict the accompanying charge profile.
FIGURE 6-1:
MCP73871 Typical Stand-Alone Application Circuit with VPCC.

FIGURE 6-2:
Typical Charge Profile
(1000 mAh Battery).

FIGURE 6-3:
Typical Charge Profile in
Preconditioning (1000 mAh Battery).
STAT1
LBO
IN
OUT
PG
VBAT
Single-Cell
Li-Ion Battery
7
1, 20
8
18, 19
10 µF
10, 11, EP
5V AC-DC Adapter
or
USB Port
STAT2
THERM
VSS
PROG1
PROG3 12
13 RPROG1
6
5
14, 15, 16
470
470
470
2
4.7 µF
System
Load
SEL
TE
PROG2
Hi
Low
Hi
Low
Hi
Low
3
4
9
RPROG3
VPCC
NTC
10 k
Hi
Low
17 CE
4.7 µF
330 k
110 k
MCP73871 Device Typical Application
SMAJ5.0A/AC
0
0.5
1
1.5
2
2.5
3
3.5
4
4.5
0
10
20
30
40
50
60
70
80
Time (Minute)
Charge Voltage (V)
0
0.2
0.4
0.6
0.8
1
1.2
1.4
1.6
1.8
2
Charge Current (A)
MCP73871
VDD = 5.2V
RPROG1 = 1 kΩ
RPROG3 = 25 kΩ
0
0.5
1
1.5
2
2.5
3
3.5
4
4.5
0
0.2
0.4
0.6
0.8
1
Time (Minute)
Charge Voltage (V)
0
0.2
0.4
0.6
0.8
1
1.2
1.4
1.6
1.8
2
Charge Current (A)
Preconditioning
Preconditioning Threshold Voltage
Fast Charge (Constant Current)
MCP73871
VDD = 5.2V
RPROG1 = 1 kΩ
RPROG3 = 25 kΩ

<!-- Page 24 -->

MCP73871
DS20002090F-page 24
 2008-2022 Microchip Technology Inc. and its subsidiaries
6.1
Application Circuit Design
Due to the low efficiency of linear charging, the most
important factors are thermal design and cost, which
are a direct function of the input voltage, output current
and thermal impedance between the battery charger
and the ambient cooling air. The worst-case situation is
when
the
device
has
transitioned
from
the
Preconditioning mode to the Constant Current mode. In
this situation, the battery charger has to dissipate the
maximum power. A trade-off must be made between
the charge current, cost and thermal requirements of
the charger.
6.1.1
COMPONENT SELECTION
Selection of the external components in Figure 6-1 is
crucial to the integrity and reliability of the charging
system. The following discussion is intended as a guide
for the component selection process.
6.1.1.1
Charge Current
The preferred fast charge current for Lithium-Ion cells
should always follow references and guidances from
battery manufacturers. For example, a 1000 mAh
battery pack has a preferred fast charge current of
0.7C. Charging at 700 mA provides the shortest charge
cycle times without degradation to the battery pack
performance or life.
6.1.1.2
Thermal Considerations
The worst-case power dissipation in the battery
charger occurs when the input voltage is at the
maximum and the device has transitioned from the
Preconditioning mode to the Constant Current mode. In
this case, the power dissipation is:
EQUATION 6-1:
For example, if VREG = 4.2V and VPTH/VREG = 69%,
power dissipation with a 5V, ±10% input voltage source
and 500 mA, ±10% fast charge current is:
EXAMPLE 6-1:
This power dissipation with the battery charger in the
QFN-20 package causes thermal regulation to enter as
depicted. Alternatively, the 4 mm x 4 mm DFN package
could be utilized to reduce heat by adding vias on the
exposed pad.
6.1.1.3
External Capacitors
The MCP73871 device is stable with or without a
battery load. To maintain good AC stability in the
Constant Voltage mode, a minimum capacitance of
4.7 µF is recommended to bypass the VBAT pin to VSS.
This capacitance provides compensation when there is
no battery load. In addition, the battery and
interconnections appear inductive at high frequencies.
These elements are in the control feedback loop during
Constant Voltage mode. Therefore, the bypass
capacitance may be necessary to compensate for the
inductive nature of the battery pack.
Virtually any good quality output filter capacitor can be
used, regardless of the capacitor’s minimum Effective
Series Resistance (ESR) value. The actual value of the
capacitor (and its associated ESR) depends on the
output load current. A 4.7 µF ceramic, tantalum or
aluminum electrolytic capacitor at the output is usually
sufficient to ensure stability for charge currents up to
1000 mA.
6.1.1.4
Reverse-Blocking Protection
The MCP73871 device provides protection from a
faulted or shorted input. Without the protection, a
faulted or shorted input would discharge the battery
pack through the body diode of the internal pass
transistor.
6.1.1.5
Temperature Monitoring
The charge temperature window can be set by placing
fixed value resistors in series-parallel with a thermistor.
The resistance values of RT1 and RT2 can be calculated
with the following equations to set the temperature
window of interest.
For NTC thermistors:
EQUATION 6-2:
PowerDissipation
VDDMAX
VPTHMIN
–


IREGMAX

=
Where:
VDDMAX
=
the maximum input voltage
IREGMAX
=
the maximum fast charge current
VPTHMIN
=
the minimum transition threshold
voltage
PowerDissipation
5.5V
2.89V
–


550mA

1.44W
=
=
24k
RT1
RT2
RCOLD

RT2
R
+
COLD
---------------------------------
+
=
5k
RT1
RT2
RHOT

RT2
R
+
HOT
-----------------------------
+
=
Where:
RT1
=
the fixed series resistance
RT2
=
the fixed parallel resistance
RCOLD
=
the thermistor resistance at the
lower temperature of interest
RHOT
=
the thermistor resistance at the
upper temperature of interest

<!-- Page 25 -->

 2008-2022 Microchip Technology Inc. and its subsidiaries
DS20002090F-page 25
MCP73871
For example, by utilizing a 10 k at 25°C NTC
thermistor with a sensitivity index, , of 3892, the
charge temperature range can be set to 0-50°C by
placing a 1.54 k resistor in series (RT1), and a
69.8 k resistor in parallel (RT2) with the thermistor.
6.1.1.6
Charge Status Interface
A status output provides information on the state of
charge. The output can be used to illuminate external
LEDs or interface to a host microcontroller. Refer to
Table 5-1 for a summary of the state of the status
output during a charge cycle.
6.1.1.7
System Load Current
The preferred discharge current for Lithium-Ion cells
should always follow references and guidance from
battery manufacturers. The recommended system
load should be the lesser of 1.0 amperes or the
maximum discharge rate of the selected Lithium-Ion
cell. This limits the safety concerns of power
dissipation
and
exceeding
the
manufacturer’s
maximum discharge rate of the cell.
The ideal diode between VBAT and OUT is designed to
drive a maximum current up to 2A. The built-in thermal
shutdown protection may turn the MCP73871 device
off with high current.
6.1.1.8
Input Overvoltage Protection (IOVP)
The input overvoltage protection must be used when
the input power source is hot-pluggable. This includes
USB cables and wall-type power supplies. The cabling
of these supplies acts as an inductor. When the
supplies are connected/disconnected from the system,
large voltage transients are created and this may
damage the system circuitry. These transients should
be snubbed out. A unidirectional or bidirectional
transzorb connected from the V+ input supply connec-
tor to the 0V ground reference will snub the transients.
An example can be seen in Figure 6-1.
6.2
PCB Layout Issues
For optimum voltage regulation, it is recommended to
place the battery pack closest to the device’s VBAT and
VSS pins to minimize voltage drops along the high
current-carrying PCB traces.
If the PCB layout is used as a heat sink, adding many
vias in the heat sink pad can help conduct more heat to
the PCB backplane, thus reducing the maximum
junction temperature.

<!-- Page 26 -->

MCP73871
DS20002090F-page 26
 2008-2022 Microchip Technology Inc. and its subsidiaries
7.0
PACKAGING INFORMATION
7.1
Package Marking Information
20-Lead QFN (4 x 4 x 0.9 mm)
Example
Legend:
XX...X
Customer-specific information
Y
Year code (last digit of calendar year)
YY
Year code (last 2 digits of calendar year)
WW
Week code (week of January 1 is week ‘01’)
NN
Alphanumeric traceability code
Pb-free JEDEC designator for Matte Tin (Sn)
*
This package is Pb-free. The Pb-free JEDEC designator (
)
can be found on the outer packaging for this package.
3
e
3
e
Note:
In the event the full Microchip part number cannot be marked on one line, it will
be carried over to the next line, thus limiting the number of available
characters for customer-specific information.
73871
1AA
I/ML
203256
3
e

<!-- Page 27 -->

 2008-2022 Microchip Technology Inc. and its subsidiaries
DS20002090F-page 27
MCP73871
B
A
0.15 C
0.15 C
0.10
C A B
0.05
C
(DATUM B)
(DATUM A)
C
SEATING
PLANE
NOTE 1
N
2X
TOP VIEW
SIDE VIEW
BOTTOM VIEW
NOTE 1
1
2
N
0.10
C A B
0.10
C A B
0.10 C
0.08 C
Microchip Technology Drawing  C04-126-ML Rev D Sheet 1 of 2
D
E
A
(A3)
20X b
e
2X
D2
E2
K
L
20X
A1
For the most current package drawings, please see the Microchip Packaging Specification located at
http://www.microchip.com/packaging
Note:
20-Lead Plastic Quad Flat, No Lead Package (ML) - 4x4 mm Body [QFN]
Also called VQFN
1
2

<!-- Page 28 -->

MCP73871
DS20002090F-page 28
 2008-2022 Microchip Technology Inc. and its subsidiaries

Microchip Technology Drawing  C04-126-ML Rev D Sheet 2 of 2
Number of Terminals
Overall Height
Terminal Width
Overall Width
Terminal Length
Exposed Pad Width
Terminal Thickness
Pitch
Standoff
Units
Dimension Limits
A1
A
b
E2
A3
e
L
E
N
0.50 BSC
0.20 REF
2.60
0.30
0.18
0.80
0.00
0.25
0.40
2.70
0.90
0.02
4.00 BSC
MILLIMETERS
MIN
NOM
20
2.80
0.50
0.30
1.00
0.05
MAX
K
-
0.20
-
REF: Reference Dimension, usually without tolerance, for information purposes only.
BSC: Basic Dimension. Theoretically exact value shown without tolerances.
1.
2.
3.
Notes:
Pin 1 visual index feature may vary, but must be located within the hatched area.
Package is saw singulated
Dimensioning and tolerancing per ASME Y14.5M
Terminal-to-Exposed-Pad
20-Lead Plastic Quad Flat, No Lead Package (ML) - 4x4 mm Body [QFN]
For the most current package drawings, please see the Microchip Packaging Specification located at
http://www.microchip.com/packaging
Note:
Also called VQFN
Overall Length
Exposed Pad Length
D
D2
2.60
4.00 BSC
2.70
2.80

<!-- Page 29 -->

 2008-2022 Microchip Technology Inc. and its subsidiaries
DS20002090F-page 29
MCP73871
RECOMMENDED LAND PATTERN
Dimension Limits
Units
C2
Optional Center Pad Width
Contact Pad Spacing
Optional Center Pad Length
Contact Pitch
Y2
X2
2.80
2.80
MILLIMETERS
0.50 BSC
MIN
E
MAX
4.00
Contact Pad Length (X20)
Contact Pad Width (X20)
Y1
X1
0.80
0.30
Microchip Technology Drawing C04-2126-ML Rev D
NOM
20-Lead Plastic Quad Flat, No Lead Package (ML) - 4x4 mm Body [QFN]
SILK SCREEN
1
2
20
C1
C2
E
X1
Y1
G1
Y2
X2
C1
Contact Pad Spacing
4.00
Contact Pad to Center Pad (X16)
G1
0.20
Thermal Via Diameter
V
Thermal Via Pitch
EV
0.30
1.00
ØV
EV
EV
BSC: Basic Dimension. Theoretically exact value shown without tolerances.
Notes:
Dimensioning and tolerancing per ASME Y14.5M
For best soldering results, thermal vias, if used, should be filled or tented to avoid solder loss during
reflow process
1.
2.
For the most current package drawings, please see the Microchip Packaging Specification located at
http://www.microchip.com/packaging
Note:
Also called VQFN

<!-- Page 30 -->

MCP73871
DS20002090F-page 30
 2008-2022 Microchip Technology Inc. and its subsidiaries
NOTES:

<!-- Page 31 -->

 2008-2022 Microchip Technology Inc. and its subsidiaries
DS20002090F-page 31
MCP73871
APPENDIX A:
REVISION HISTORY
Revision F (February 2022)
• Updated Table 4-1 to improve clarity (“IOUT”
replaced with “System Power FET”).
• Updated document layout.
• Updated Section 7.0 “Packaging Information”
drawings and information.
• Updated Product Identification System.
Revision E (April 2019)
• Updated DC CHARACTERISTICS table.
• Updated Figure 2-14, Figure 2-15, Figure 2-16,
and Figure 4-3.
• Updated Section 3.14 “Timer Enable (TE)”.
• Updated Section 6.1.1.2 “Thermal
Considerations” and Equation 6-2.
Revision D (February 2018)
• Corrected Figure 2-26.
• Added Figure 2-27.
• Updated Figure 6-1.
• Added Section 6.1.1.8 “Input Overvoltage
Protection (IOVP)”.
• Minor typographical edits.
Revision C (September 2013)
• Updated Functional Block Diagram.
• Added Table 4-1 in Section 4.0 “Device
Overview”.
• Updated Section 7.0 “Packaging Information”.
• Minor grammatical and editorial corrections.
Revision B (May 2009)
• Updated the QFN-20 package drawing.
• Updated Equation 4-1.
• Updated Section 4.7 “Charge Termination” and
Equation 4-2.
• Updated Equation 5-1.
Revision A (July 2008)
• Original Release of this Document.

<!-- Page 32 -->

MCP73871
DS20002090F-page 32
 2008-2022 Microchip Technology Inc. and its subsidiaries
NOTES:

<!-- Page 33 -->

 2008-2022 Microchip Technology Inc. and its subsidiaries
DS20002090F-page 33
MCP73871
PRODUCT IDENTIFICATION SYSTEM
To order or obtain information, e.g., on pricing or delivery, refer to the factory or the listed sales office.
Device:
MCP73871:
USB/AC Battery Charger with PPM
Tape and Reel
Option:
(Blank)
T
= Standard packaging (tube or tray)
= Tape and Reel(1)
Output Options * *
* Refer to table below for different operational
options.
** Consult Factory for Alternative Device Options.
Temperature:
I
= -40C to +85C
Package Type:
ML
= Plastic Quad Flat No Lead (QFN),
4x4x0.9 mm Body, 20-lead
PART NO.
-XXX
Output
Device
Options*
X
Temp.
/XX
Package
Examples: **
a) MCP73871-1AAI/ML:
Tube,
4.10V PPM Battery Charger,
20-LD QFN package
b) MCP73871T-1CAI/ML:
Tape and Reel,
4.10V PPM Battery Charger,
-40C to +85C,
20-LD QFN package
c) MCP73871-2AAI/ML:
Tube,
4.20V PPM Battery Charger,
-40°C to +85°C,
20-LD QFN package
d) MCP73871T-2CCI/ML:
Tape and Reel,
4.20V PPM Battery Charger,
-40°C to +85°C,
20-LD QFN package
e) MCP73871-3CAI/ML:
Tube,
4.35V PPM Battery Charger,
-40°C to +85°C,
20-LD QFN package
f) MCP73871T-4CCI/ML:
Tape and Reel,
4.40V PPM Battery Charger,
-40°C to +85°C,
20-LD QFN package
** Consult Factory for Alternative Device Options
[T](1)
Tape and Reel
Note 1:
Tape and Reel identifier only appears in the
catalog part number description. This identifier is
used for ordering purposes and is not printed on
the device package. Check with your Microchip
Sales Office for package availability with the
Tape and Reel option.
* Operational Output Options
Output
Options
VREG
Safety Timer
Duration (Hours)
LBO Voltage
Threshold (V)
1AA
4.10V
Disabled
Disabled
1CA
4.10V
6
Disabled
1CC
4.10V
6
3.1
2AA
4.20V
Disabled
Disabled
2CA
4.20V
6
Disabled
2CC
4.20V
6
3.1
3CA
4.35V
6
Disabled
3CC
4.35V
6
3.1
4CA
4.40V
6
Disabled
4CC
4.40V
6
3.1
** Consult Factory for Alternative Device Options.

<!-- Page 34 -->

MCP73871
DS20002090F-page 34
 2008-2022 Microchip Technology Inc. and its subsidiaries
NOTES:

<!-- Page 35 -->

 2008-2022 Microchip Technology Inc. and its subsidiaries
DS20002090F-page 35
This publication and the information herein may be used only
with Microchip products, including to design, test, and integrate
Microchip products with your application. Use of this informa-
tion in any other manner violates these terms. Information
regarding device applications is provided only for your conve-
nience and may be superseded by updates. It is your responsi-
bility to ensure that your application meets with your
specifications. Contact your local Microchip sales office for
additional support or, obtain additional support at https://
www.microchip.com/en-us/support/design-help/client-support-
services.
THIS INFORMATION IS PROVIDED BY MICROCHIP "AS IS".
MICROCHIP MAKES NO REPRESENTATIONS OR WAR-
RANTIES OF ANY KIND WHETHER EXPRESS OR IMPLIED,
WRITTEN OR ORAL, STATUTORY OR OTHERWISE,
RELATED TO THE INFORMATION INCLUDING BUT NOT
LIMITED TO ANY IMPLIED WARRANTIES OF NON-
INFRINGEMENT, MERCHANTABILITY, AND FITNESS FOR A
PARTICULAR PURPOSE, OR WARRANTIES RELATED TO
ITS CONDITION, QUALITY, OR PERFORMANCE.
IN NO EVENT WILL MICROCHIP BE LIABLE FOR ANY INDI-
RECT, SPECIAL, PUNITIVE, INCIDENTAL, OR CONSE-
QUENTIAL LOSS, DAMAGE, COST, OR EXPENSE OF ANY
KIND WHATSOEVER RELATED TO THE INFORMATION OR
ITS USE, HOWEVER CAUSED, EVEN IF MICROCHIP HAS
BEEN ADVISED OF THE POSSIBILITY OR THE DAMAGES
ARE
FORESEEABLE.
TO
THE
FULLEST
EXTENT
ALLOWED BY LAW, MICROCHIP'S TOTAL LIABILITY ON
ALL CLAIMS IN ANY WAY RELATED TO THE INFORMATION
OR ITS USE WILL NOT EXCEED THE AMOUNT OF FEES, IF
ANY, THAT YOU HAVE PAID DIRECTLY TO MICROCHIP
FOR THE INFORMATION.
Use of Microchip devices in life support and/or safety applica-
tions is entirely at the buyer's risk, and the buyer agrees to
defend, indemnify and hold harmless Microchip from any and
all damages, claims, suits, or expenses resulting from such
use. No licenses are conveyed, implicitly or otherwise, under
any Microchip intellectual property rights unless otherwise
stated.
Trademarks
The Microchip name and logo, the Microchip logo, Adaptec,
AnyRate, AVR, AVR logo, AVR Freaks, BesTime, BitCloud,
CryptoMemory, CryptoRF, dsPIC, flexPWR, HELDO, IGLOO,
JukeBlox, KeeLoq, Kleer, LANCheck, LinkMD, maXStylus,
maXTouch, MediaLB, megaAVR, Microsemi, Microsemi logo,
MOST, MOST logo, MPLAB, OptoLyzer, PIC, picoPower,
PICSTART, PIC32 logo, PolarFire, Prochip Designer, QTouch,
SAM-BA, SenGenuity, SpyNIC, SST, SST Logo, SuperFlash,
Symmetricom, SyncServer, Tachyon, TimeSource, tinyAVR, UNI/O,
Vectron, and XMEGA are registered trademarks of Microchip
Technology Incorporated in the U.S.A. and other countries.
AgileSwitch, APT, ClockWorks, The Embedded Control Solutions
Company, EtherSynch, Flashtec, Hyper Speed Control, HyperLight
Load, IntelliMOS, Libero, motorBench, mTouch, Powermite 3,
Precision Edge, ProASIC, ProASIC Plus, ProASIC Plus logo, Quiet-
Wire, SmartFusion, SyncWorld, Temux, TimeCesium, TimeHub,
TimePictra, TimeProvider, TrueTime, WinPath, and ZL are
registered trademarks of Microchip Technology Incorporated in the
U.S.A.
Adjacent Key Suppression, AKS, Analog-for-the-Digital Age, Any
Capacitor, AnyIn, AnyOut, Augmented Switching, BlueSky,
BodyCom, CodeGuard, CryptoAuthentication, CryptoAutomotive,
CryptoCompanion, CryptoController, dsPICDEM, dsPICDEM.net,
Dynamic Average Matching, DAM, ECAN, Espresso T1S,
EtherGREEN, GridTime, IdealBridge, In-Circuit Serial
Programming, ICSP, INICnet, Intelligent Paralleling, Inter-Chip
Connectivity, JitterBlocker, Knob-on-Display, maxCrypto, maxView,
memBrain, Mindi, MiWi, MPASM, MPF, MPLAB Certified logo,
MPLIB, MPLINK, MultiTRAK, NetDetach, NVM Express, NVMe,
Omniscient Code Generation, PICDEM, PICDEM.net, PICkit,
PICtail, PowerSmart, PureSilicon, QMatrix, REAL ICE, Ripple
Blocker, RTAX, RTG4, SAM-ICE, Serial Quad I/O, simpleMAP,
SimpliPHY, SmartBuffer, SmartHLS, SMART-I.S., storClad, SQI,
SuperSwitcher, SuperSwitcher II, Switchtec, SynchroPHY, Total
Endurance, TSHARC, USBCheck, VariSense, VectorBlox, VeriPHY,
ViewSpan, WiperLock, XpressConnect, and ZENA are trademarks
of Microchip Technology Incorporated in the U.S.A. and other
countries.
SQTP is a service mark of Microchip Technology Incorporated in
the U.S.A.
The Adaptec logo, Frequency on Demand, Silicon Storage
Technology, Symmcom, and Trusted Time are registered
trademarks of Microchip Technology Inc. in other countries.
GestIC is a registered trademark of Microchip Technology Germany
II GmbH & Co. KG, a subsidiary of Microchip Technology Inc., in
other countries.
All other trademarks mentioned herein are property of their
respective companies.
© 2008-2022, Microchip Technology Incorporated and its subsidiar-
ies.
All Rights Reserved.
ISBN: 978-1-5224-9870-4
Note the following details of the code protection feature on Microchip products:
•
Microchip products meet the specifications contained in their particular Microchip Data Sheet.
•
Microchip believes that its family of products is secure when used in the intended manner, within operating specifications, and
under normal conditions.
•
Microchip values and aggressively protects its intellectual property rights. Attempts to breach the code protection features of
Microchip product is strictly prohibited and may violate the Digital Millennium Copyright Act.
•
Neither Microchip nor any other semiconductor manufacturer can guarantee the security of its code. Code protection does not
mean that we are guaranteeing the product is “unbreakable”. Code protection is constantly evolving. Microchip is committed to
continuously improving the code protection features of our products.
For information regarding Microchip’s Quality Management Systems,
please visit www.microchip.com/quality.

<!-- Page 36 -->

DS20002090F-page 36
 2008-2022 Microchip Technology Inc. and its subsidiaries
AMERICAS
Corporate Office
2355 West Chandler Blvd.
Chandler, AZ 85224-6199
Tel: 480-792-7200
Fax: 480-792-7277
Technical Support:
http://www.microchip.com/
support
Web Address:
www.microchip.com
Atlanta
Duluth, GA
Tel: 678-957-9614
Fax: 678-957-1455
Austin, TX
Tel: 512-257-3370
Boston
Westborough, MA
Tel: 774-760-0087
Fax: 774-760-0088
Chicago
Itasca, IL
Tel: 630-285-0071
Fax: 630-285-0075
Dallas
Addison, TX
Tel: 972-818-7423
Fax: 972-818-2924
Detroit
Novi, MI
Tel: 248-848-4000
Houston, TX
Tel: 281-894-5983
Indianapolis
Noblesville, IN
Tel: 317-773-8323
Fax: 317-773-5453
Tel: 317-536-2380
Los Angeles
Mission Viejo, CA
Tel: 949-462-9523
Fax: 949-462-9608
Tel: 951-273-7800
Raleigh, NC
Tel: 919-844-7510
New York, NY
Tel: 631-435-6000
San Jose, CA
Tel: 408-735-9110
Tel: 408-436-4270
Canada - Toronto
Tel: 905-695-1980
Fax: 905-695-2078
ASIA/PACIFIC
Australia - Sydney
Tel: 61-2-9868-6733
China - Beijing
Tel: 86-10-8569-7000
China - Chengdu
Tel: 86-28-8665-5511
China - Chongqing
Tel: 86-23-8980-9588
China - Dongguan
Tel: 86-769-8702-9880
China - Guangzhou
Tel: 86-20-8755-8029
China - Hangzhou
Tel: 86-571-8792-8115
China - Hong Kong SAR
Tel: 852-2943-5100
China - Nanjing
Tel: 86-25-8473-2460
China - Qingdao
Tel: 86-532-8502-7355
China - Shanghai
Tel: 86-21-3326-8000
China - Shenyang
Tel: 86-24-2334-2829
China - Shenzhen
Tel: 86-755-8864-2200
China - Suzhou
Tel: 86-186-6233-1526
China - Wuhan
Tel: 86-27-5980-5300
China - Xian
Tel: 86-29-8833-7252
China - Xiamen
Tel: 86-592-2388138
China - Zhuhai
Tel: 86-756-3210040
ASIA/PACIFIC
India - Bangalore
Tel: 91-80-3090-4444
India - New Delhi
Tel: 91-11-4160-8631
India - Pune
Tel: 91-20-4121-0141
Japan - Osaka
Tel: 81-6-6152-7160
Japan - Tokyo
Tel: 81-3-6880- 3770
Korea - Daegu
Tel: 82-53-744-4301
Korea - Seoul
Tel: 82-2-554-7200
Malaysia - Kuala Lumpur
Tel: 60-3-7651-7906
Malaysia - Penang
Tel: 60-4-227-8870
Philippines - Manila
Tel: 63-2-634-9065
Singapore
Tel: 65-6334-8870
Taiwan - Hsin Chu
Tel: 886-3-577-8366
Taiwan - Kaohsiung
Tel: 886-7-213-7830
Taiwan - Taipei
Tel: 886-2-2508-8600
Thailand - Bangkok
Tel: 66-2-694-1351
Vietnam - Ho Chi Minh
Tel: 84-28-5448-2100
EUROPE
Austria - Wels
Tel: 43-7242-2244-39
Fax: 43-7242-2244-393
Denmark - Copenhagen
Tel: 45-4485-5910
Fax: 45-4485-2829
Finland - Espoo
Tel: 358-9-4520-820
France - Paris
Tel: 33-1-69-53-63-20
Fax: 33-1-69-30-90-79
Germany - Garching
Tel: 49-8931-9700
Germany - Haan
Tel: 49-2129-3766400
Germany - Heilbronn
Tel: 49-7131-72400
Germany - Karlsruhe
Tel: 49-721-625370
Germany - Munich
Tel: 49-89-627-144-0
Fax: 49-89-627-144-44
Germany - Rosenheim
Tel: 49-8031-354-560
Israel - Ra’anana
Tel: 972-9-744-7705
Italy - Milan
Tel: 39-0331-742611
Fax: 39-0331-466781
Italy - Padova
Tel: 39-049-7625286
Netherlands - Drunen
Tel: 31-416-690399
Fax: 31-416-690340
Norway - Trondheim
Tel: 47-7288-4388
Poland - Warsaw
Tel: 48-22-3325737
Romania - Bucharest
Tel: 40-21-407-87-50
Spain - Madrid
Tel: 34-91-708-08-90
Fax: 34-91-708-08-91
Sweden - Gothenberg
Tel: 46-31-704-60-40
Sweden - Stockholm
Tel: 46-8-5090-4654
UK - Wokingham
Tel: 44-118-921-5800
Fax: 44-118-921-5820
Worldwide Sales and Service

---

# 2. MAX17048/MAX17049 — Fuel Gauge

> **Role:** Battery gauge — MAX17048G+T10  
> **Covers:** `C2682616` (Gauge)

<!-- Page 1 -->

19-6171; Rev 7; 11/16
General Description
The MAX17048/MAX17049 ICs are tiny, micropower cur-
rent fuel gauges for lithium-ion (Li+) batteries in handheld
and portable equipment. The MAX17048 operates with
a single lithium cell and the MAX17049 with two lithium
cells in series.
The ICs use the sophisticated Li+ battery-modeling algo-
rithm ModelGauge™ to track the battery relative state-of-
charge (SOC) continuously over widely varying charge
and discharge conditions. The ModelGauge algorithm
eliminates current-sense resistor and battery-learn cycles
required in traditional fuel gauges. Temperature compen-
sation is implemented using the system microcontroller.
The ICs automatically detect when the battery enters a
low-current state and enters low-power 3µA hibernate
mode, while still providing accurate fuel gauging. The
ICs automatically exit hibernate mode when the system
returns to active state.
On battery insertion, the ICs debounce initial voltage
measurements to improve the initial SOC estimate,
thus allowing them to be located on system side. SOC,
voltage, and rate information is accessed using the I2C
interface. The ICs are available in a tiny 0.9mm x 1.7mm,
8-bump wafer-level package (WLP), or a 2mm x 2mm,
8-pin TDFN package.
Applications
●
●
Smartphones, Tablets
●
●
Smartwatches, Wearables
●
●
Bluetooth Headsets
●
●
Health and Fitness Monitors
●
●
Digital Still, Video, and Action Cameras
●
●
Medical Devices
●
●
Handheld Computers and Terminals
●
●
Wireless Speakers
●
●
Home and Building Automation, Sensors
Features and Benefits
●
●
MAX17048: 1 Cell, MAX17049: 2 Cells
●
●
Precision ±7.5mV/Cell Voltage Measurement
●
●
ModelGauge Algorithm
•	 Provides Accurate State-of-Charge
•	 Compensates for Temperature/Load Variation
•	 Does Not Accumulate Errors, Unlike Coulomb
Counters
•	 Eliminates Learning
•	 Eliminates Current-Sense Resistor
●
●
Ultra-Low Quiescent Current
•	 3μA Hibernate, 23μA Active
•	 Fuel Gauges in Hibernate Mode
•	 Automatically Enters and Exits Hibernate Mode
●
●
Reports Charge and Discharge Rate
●
●
Battery-Insertion Debounce
•	 Best of 16 Samples to Estimate Initial SOC
●
●
Programmable Reset for Battery Swap
•	 2.28V to 3.48V Range
●
●
Configurable Alert Indicator
•	 Low SOC
•	 1% Change in SOC
•	 Battery Undervoltage/Overvoltage
•	 VRESET Alert
●
●
I2C Interface
●
●
8-Bit OTP ID Register (Contact Factory)
ModelGauge is a trademark of Maxim Integrated Products, Inc.
Ordering Information appears at end of data sheet.
ONLY ONE
EXTERNAL
COMPONENT
VDD
ALRT
SDA
SCL
CELL
QSTRT
CTG
GND
SYSTEM
µP
MAX17048
MAX17048/MAX17049
3μA 1-Cell/2-Cell Fuel Gauge with ModelGauge
Simple Fuel-Gauge Circuit Diagram
EVALUATION KIT AVAILABLE

<!-- Page 2 -->

CELL to GND.........................................................-0.3V to +12V
All Other Pins to GND..............................................-0.3V to +6V
Continuous Sink Current, SDA, ALRT................................20mA
Operating Temperature Range........................... -40°C to +85°C
Storage Temperature Range............................. -55°C to +125°C
Lead Temperature (TDFN only) (soldering, 10s) ............+300°C
Soldering Temperature (reflow).......................................+260°C
(VDD = 2.5V to 4.5V, TA= -20°C to +70°C, unless otherwise noted. Typical values are at TA = +25°C.) (Note 1)
PARAMETER
SYMBOL
CONDITIONS
MIN
TYP
MAX
UNITS
Supply Voltage
VDD
(Note 2)
2.5
4.5
V
Fuel-Gauge SOC Reset
(VRESET Register)
VRST
Configuration range, in 40mV steps
2.28
3.48
V
Trimmed at 3V
2.85
3.0
3.15
V
Data I/O Pins
SCL, SDA,
ALRT
(Note 2)
-0.3
+5.5
V
Supply Current
IDD0
Sleep mode, TA ≤ +50°C
0.5
2
µA
Hibernate mode, reset comparator
disabled (VRESET.Dis = 1)
3
5
Hibernate mode, reset comparator
enabled (VRESET.Dis = 0)
4
IDD1
Active mode
23
40
Time Base Accuracy
tERR
Active, hibernate modes (Note 3)
-3.5
±1
+3.5
%
ADC Sample Period
Active mode
250
ms
Hibernate mode
45
s
Voltage Error
VERR
VCELL = 3.6V, TA = +25°C (Note 4)
-7.5
+7.5
mV/cell
-20
+20
Voltage-Measurement Resolution
1.25
mV/cell
Voltage-Measurement Range
MAX17048: VDD pin
2.5
5
V
MAX17049: CELL pin
5
10
SDA, SCL, QSTRT Input
Logic-High
VIH
1.4
V
SDA, SCL, QSTRT Input
Logic-Low
VIL

0.5
V
SDA, ALRT Output
Logic-Low
VOL
IOL = 4mA
0.4
V
SDA, SCL Bus
Low-Detection Current
IPD
VSDA = VSCL = 0.4V (Note 5)
0.2
0.4
µA
Bus Low-Detection Timeout
tSLEEP
(Note 6)
1.75
2.5
s
MAX17048/MAX17049
3μA 1-Cell/2-Cell Fuel Gauge with ModelGauge
www.maximintegrated.com
Maxim Integrated  │  2
Absolute Maximum Ratings
Stresses beyond those listed under “Absolute Maximum Ratings” may cause permanent damage to the device. These are stress ratings only, and functional operation of the device at these
or any other conditions beyond those indicated in the operational sections of the specifications is not implied. Exposure to absolute maximum rating conditions for extended periods may affect
device reliability.
Electrical Characteristics

<!-- Page 3 -->

(2.5V < VDD < 4.5V, TA = -20°C to +70°C, unless otherwise noted.) (Note 1)
Note 1:	 Specifications are 100% tested at TA = +25°C. Limits over the operating range are guaranteed by design and
characterization.
Note 2:	 All voltages are referenced to GND.
Note 3:	 Test is performed on unmounted/unsoldered parts.
Note 4:	 The voltage is trimmed and verified with 16x averaging.
Note 5:	 This current is always present.
Note 6:	 The IC enters shutdown mode after SCL < VIL and SDA < VIL for longer than 2.5s.
Note 7:	 Timing must be fast enough to prevent the IC from entering sleep mode due to bus low for period > tSLEEP.
Note 8:	 fSCL must meet the minimum clock low time plus the rise/fall times.
Note 9:	 The maximum tHD:DAT has to be met only if the device does not stretch the low period (tLOW) of the SCL signal.
Note 10:	This device internally provides a hold time of at least 100ns for the SDA signal (referred to the VIH,MIN of the SCL signal) to
bridge the undefined region of the falling edge of SCL.
Note 11:	Filters on SDA and SCL suppress noise spikes at the input buffers and delay the sampling instance.
Note 12:	CB is total capacitance of one bus line in pF.
PARAMETER
SYMBOL
CONDITIONS
MIN
TYP
MAX
UNITS
SCL Clock Frequency
fSCL
(Note 7)
0
400
kHz
Bus Free Time Between a
STOP and START Condition
tBUF
1.3
µs
START Condition (Repeated)
Hold Time
tHD:STA
(Note 8)
0.6
µs
Low Period of SCL Clock
tLOW
1.3
µs
High Period of SCL Clock
tHIGH
0.6
µs
Setup Time for a Repeated
START Condition
tSU:STA
0.6
µs
Data Hold Time
tHD:DAT
(Notes 9, 10)
0
0.9
µs
Data Setup Time
tSU:DAT
(Note 9)
100
ns
Rise Time of Both SDA and
SCL Signals
tR
20 + 0.1CB
300
ns
Fall Time of Both SDA and SCL
Signals
tF
20 + 0.1CB
300
ns
Setup Time for STOP Condition
tSU:STO
0.6
µs
Spike Pulse Widths Suppressed
by Input Filter
tSP
(Note 11)
0
50
ns
Capacitive Load for Each Bus
Line
CB
(Note 12)
400
pF
SCL, SDA Input Capacitance
CB,IN
60
pF
MAX17048/MAX17049
3μA 1-Cell/2-Cell Fuel Gauge with ModelGauge
www.maximintegrated.com
Maxim Integrated  │  3
Electrical Characteristics (I2C INTERFACE)

<!-- Page 4 -->

(TA = +25°C, battery is Sanyo UF504553F, unless otherwise noted.)
Figure 1. I2C Bus Timing Diagram
CRATE ACCURACY
MAX17048 toc04
CRATE (%/Hr)
-0.75
-0.50
-0.25
0
0.25
0.50
0.75
1.00
-1.00
TIME (Hr)
6
4
2
0
-2
-4
8
MAX17048 CRATE
MEASURED CRATE
ENTER HIBERNATE MODE
AUTOMATICALLY
MAX17048 toc05
TIME (min)
CURRENT (I_BATT mA, I_DD uA)
VBATT (V)
15
10
5
0
3.70
100
200
300
400
500
600
-100
0
20
VBATT
IBATT
IDD1
IDD0
3.75
3.80
3.85
3.90
3.95
4.00
3.65
QUIESCENT CURRENT vs. SUPPLY
VOLTAGE (HIBERNATE MODE)
MAX17048 toc01
VCELL (V)
QUIESCENT CURRENT (µA)
4.0
3.5
3.0
0
2.5
4.5
TA = +70°C
1
2
3
4
5
TA = -20°C
TA = +25°C
5
10
15
20
25
30
35
40
QUIESCENT CURRENT vs. SUPPLY
VOLTAGE (ACTIVE MODE)
MAX17048 toc02
VCELL (V)
QUIESCENT CURRENT (µA)
4.0
3.5
3.0
0
2.5
4.5
TA = +70°C
TA = -20°C
TA = +25°C
VOLTAGE ADC ERROR vs. TEMPERATURE
MAX17048 toc03
TEMPERATURE (°C)
VOLTAGE ADC ERROR (mV/CELL)
55
40
-5
10
25
-15
-10
-5
0
5
10
15
20
-20
-20
70
VCELL = 3.6V
VCELL = 2.5V
VCELL = 4.5V
SDA
SCL
tF
tLOW
tHD:STA
tHD:DAT
tSU:STA
tSU:STO
tSU:DAT
tHD:STA
tSP
tR
tBUF
tR
tF
S
Sr
P
S
MAX17048/MAX17049
3μA 1-Cell/2-Cell Fuel Gauge with ModelGauge
www.maximintegrated.com
Maxim Integrated  │  4
Typical Operating Characteristics

<!-- Page 5 -->

(TA = +25°C, battery is Sanyo UF504553F, unless otherwise noted.)
EXIT HIBERNATE MODE
AUTOMATICALLY
MAX17048 toc06
TIME (min)
CURRENT (I_BATT mA, I_DD uA)
VBATT (V)
8
2
4
6
0
3.70
100
200
300
400
500
600
-100
0
10
VBATT
IBATT
IDD1
IDD0
3.75
3.80
3.85
3.90
3.95
4.00
3.65
SOC ACCURACY TA = 20°C, HIBERNATE MODE
MAX17048 toc07
TIME (Hr)
SOC (%)
ERROR (%)
8
6
4
REFERENCE SOC
MODELGAUGE
ERROR
2
25
50
75
100
0
-5
0
5
10
-10
-4
-2
0
10
ZIGZAG PATTERN SOC ACCURACY (1/3)
MAX17048 toc08
SOC (%)
ERROR (%)
REFERENCE SOC
MODELGAUGE
ERROR
25
50
75
100
0
-5
0
5
10
-10
TIME (Hr)
80
60
40
20
0
100
ZIGZAG PATTERN SOC ACCURACY (2/3)
MAX17048 toc09
TIME (Hr)
SOC (%)
ERROR (%)
8
6
4
REFERENCE SOC
MODELGAUGE
ERROR
2
25
50
75
100
0
-5
0
5
10
-10
0
10
ZIGZAG PATTERN SOC ACCURACY (3/3)
MAX17048 toc10
TIME (Hr)
SOC (%)
ERROR (%)
103
101
99
REFERENCE SOC
MODELGAUGE
ERROR
97
25
50
75
100
0
-5
0
5
10
-10
95
105
MAX17048 toc11
0A
0V
0V
0V
4ms/div
DEBOUNCE
COMPLETED
DEBOUNCE
BEGINS
VCELL
OCV
BATTERY-INSERTION DEBOUNCE/
OCV ACQUISITION
Maxim Integrated  │  5
www.maximintegrated.com
MAX17048/MAX17049
3μA 1-Cell/2-Cell Fuel Gauge with ModelGauge
Typical Operating Characteristics (continued)

<!-- Page 6 -->

PIN/BUMP
NAME
FUNCTION
TDFN
WLP
1
A1
CTG
Connect to Ground
2
A2
CELL
Connect to the Positive Battery Terminal.
MAX17048: Not internally connected.
MAX17049: Voltage sense input.
3
A3
VDD
Power-Supply Input. Bypass with 0.1µF to GND.
MAX17048: Voltage sense input. Connect to positive battery terminal.
MAX17049: Connect to regulated power-supply voltage.
4
A4
GND
Ground. Connect to negative battery terminal.
5
B4
ALRT
Open-Drain, Active-Low Alert Output. Optionally connect to interrupt input of the system
microcontroller.
6
B3
QSTRT
Quick-Start Input. Allows reset of the device through hardware. Connect to GND if not used.
7
B2
SCL
I2C Clock Input. SCL has an internal pulldown (IPD) for sensing disconnection.
8
B1
SDA
Open-Drain I2C Data Input/Output. SDA has an internal pulldown (IPD) for sensing
disconnection.
—
—
EP
Exposed Pad (TDFN Only). Connect to GND.
1
+
3
4
8
6
5
SDA
QSTRT
ALRT
MAX17048
MAX17049
2
7
SCL
CTG
VDD
GND
CELL
TDFN
TOP VIEW
(PAD SIDE DOWN)
A1
A2
A3
A4
B1
B2
B3
B4
+
TOP VIEW
(BUMP SIDE DOWN)
MAX17048
MAX17049
WLP
CTG
CELL
VDD
GND
SDA
SCL
QSTRT
ALRT
MAX17048/MAX17049
3μA 1-Cell/2-Cell Fuel Gauge with ModelGauge
www.maximintegrated.com
Maxim Integrated  │  6
Pin/Bump Descriptions
Pin/Bump Configurations

<!-- Page 7 -->

Detailed Description
ModelGauge Theory of Operation
The MAX17048/MAX17049 ICs simulate the internal,
nonlinear dynamics of a Li+ battery to determine its SOC.
The sophisticated battery model considers impedance
and the slow rate of chemical reactions in the battery
(Figure 2).
ModelGauge performs best with a custom model, obtained
by characterizing the battery at multiple discharge cur-
rents and temperatures to precisely model it. At power-on
reset (POR), the ICs have a preloaded ROM model that
performs well for some batteries. Contact Maxim if you
need a custom model.
Fuel-Gauge Performance
In coulomb counter-based fuel gauges, SOC drifts
because offset error in the current-sense ADC measure-
ment accumulates over time. Instantaneous error can be
very small, but never precisely zero. Error accumulates
over time in such systems (typically 0.5%–2% per day)
and requires periodic corrections. Some algorithms cor-
rect drift using occasional events, and until such an event
occurs the algorithm’s error is boundless:
•	 Reaching predefined SOC levels near full or empty
•	 Measuring the relaxed battery voltage after a long
period of inactivity
•	 Completing a full charge/discharge cycle
ModelGauge requires no correction events because it
uses only voltage, which is stable over time. As TOCs 8,
9, and 10 show, ModelGauge remains accurate despite
the absence of any of the above events; it neither drifts
nor accumulates error over time.
To correctly measure performance of a fuel gauge as
experienced by end-users, exercise the battery dynami-
cally. Accuracy cannot be fully determined from only
simple cycles.
Battery Voltage and State-Of-Charge
Open-circuit voltage (OCV) of a Li+ battery uniquely
determines its SOC; one SOC can have only one value of
OCV. In contrast, a given VCELL can occur at many differ-
ent values of OCV because VCELL is a function of time,
OCV, load, temperature, age, and impedance, etc.; one
value of OCV can have many values of VCELL. Therefore,
one SOC can have many values of VCELL, so VCELL can-
not uniquely determine SOC.
Figure 3 shows that VCELL = 3.81V occurs at 2%, 50%,
and 72% SOC.
Even the use of sophisticated tables to consider both
voltage and load results in significant error due to the
load transients typically experienced in a system. During
charging or discharging, and for approximately 30min
after, VCELL and OCV differ substantially, and VCELL has
been affected by the preceding hours of battery activity.
ModelGauge uses voltage comprehensively.
Figure 2. Block Diagram
Figure 3. Instantaneous Voltage Does Not Translate Directly to
SOC
STATE
MACHINE
(SOC, RATE)
2-WIRE
INTERFACE
IC
GROUND
TIME BASE
(32kHz)
ADC (VCELL)
VOLTAGE
REFERENCE
BIAS
GND
CELL
VDD
SCL
SDA
ALRT
QSTRT
CTG
MAX17048
MAX17049
TIME (HOURS)
SOC
VCELL
100%
80%
60%
40%
20%
0%
0
1
2
3
4
5
6
7
8
3.4V
3.6V
3.8V
4.0V
4.2V
3.2V
3.81V = 2%
VCELL
SOC
3.81V = 72%
3.81V = 50%
3.81V
MAX17048/MAX17049
3μA 1-Cell/2-Cell Fuel Gauge with ModelGauge
www.maximintegrated.com
Maxim Integrated  │  7

<!-- Page 8 -->

Temperature Compensation
For best performance, the host microcontroller must mea-
sure battery temperature periodically, and compensate
the RCOMP ModelGauge parameter accordingly, at least
once per minute. Each custom model defines constants
RCOMP0 (default is 0x97), TempCoUp (default is -0.5),
and TempCoDown (default is -5.0). To calculate the new
value of CONFIG.RCOMP:
// T is battery temperature (degrees Celsius)
if (T > 20) {
RCOMP = RCOMP0 + (T - 20) x TempCoUp;
}
else {
RCOMP = RCOMP0 + (T - 20) x TempCoDown;
}
Impact of Empty-Voltage Selection
Most applications have a minimum operating voltage
below which the system immediately powers off (empty
voltage). When characterizing the battery to create a cus-
tom model, choose empty voltage carefully. As shown in
Figure 4, capacity unavailable to the system increases at
an accelerating rate as empty voltage increases.
To ensure a controlled shutdown, consider including
operating margin into the fuel gauge based on some low
threshold of SOC, for example shutting down at 3% or
5%. This utilizes the battery more effectively than adding
error margin to empty voltage.
Battery Insertion
When the battery is first inserted into the system, the
fuel-gauge IC has no previous knowledge about the bat-
tery’s SOC. Assuming that the battery is relaxed, the IC
translates its first VCELL measurement into the best initial
estimate of SOC. Initial error caused by the battery not
being in a relaxed state diminishes over time, regardless
of loading following this initial conversion. While SOC esti-
mated by a coulomb counter diverges, ModelGauge SOC
converges, correcting error automatically as illustrated in
Figure 5; initial error has no long-lasting impact.
Battery Insertion Debounce
Any time the IC powers on or resets (see the VRESET/
ID Register (0x18) section), it estimates that OCV is the
maximum of 16 VCELL samples (1ms each, full 12-bit
resolution). OCV is ready 17ms after battery insertion,
and SOC is ready 175ms after that.
Figure 4. Increasing Empty Voltage Reduces Battery Capacity
Figure 5. ModelGauge Heals Error Automatically
CAPACITY LOST (%)
60
50
40
30
20
10
0
TARGET EMPTY VOLTAGE (V)
3.0
3.1
3.2
3.3
3.4
3.5
C/3 LOAD
C/10 LOAD
LONGER BATTERY RELAXATION
IMPROVES INITIAL ACCURACY
RELAXATION TIME BEFORE INSERTION (MINUTES)
INITIAL VOLTAGE ERROR (mV)
SOC ERROR (%)
0
-10
-20
0
-5
-10
0.1
1
10
100
1000
SOC ERROR
VOLTAGE ERROR
MODELGAUGE HEALS ERROR
AUTOMATICALLY OVER TIME
TIME AFTER INSERTION (MINUTES)
SOC (%)
0
-5
-10
30
45
15
0
0
20
40
60
80
RELAXED SOC
REFERENCE SOC
RELAXED ERROR
UNRELAXED ERROR
UNRELAXED SOC
MAX17048/MAX17049
3μA 1-Cell/2-Cell Fuel Gauge with ModelGauge
www.maximintegrated.com
Maxim Integrated  │  8

<!-- Page 9 -->

Battery Swap Detection
If VCELL falls below VRST, the IC quick-starts when
VCELL returns above VRST. This handles battery swap;
the SOC of the previous battery does not affect that of the
new one. See the Quick-Start and VRESET/ID Register
(0x18) sections.
Quick-Start
If the IC generates an erroneous initial SOC, the battery
insertion and system powerup voltage waveforms must
be examined to determine if a quick-start is necessary,
as well as the best time to execute the command. The IC
samples the maximum VCELL during the first 17ms. See
the Battery Insertion Debounce section. Unless VCELL is
fully relaxed, even the best sampled voltage can appear
greater or less than OCV. Therefore, quick-start must be
used cautiously.
Most systems should not use quick-start because the
ICs handle most startup problems transparently, such as
intermittent battery-terminal connection during insertion. If
battery voltage stabilizes faster than 17ms, as illustrated
in Figure 6, then do not use quick-start.
The quick-start command restarts fuel-gauge calcula-
tions in the same manner as initial power-up of the IC. If
the system power-up sequence is so noisy that the initial
estimate of SOC has unacceptable error, the system
microcontroller might be able to reduce the error by using
quick-start. A quick-start is initiated by a rising edge on
the QSTRT pin, or by writing 1 to the quick-start bit in the
MODE register.
Power-On Reset (POR)
POR includes a quick-start, so only use it when the bat-
tery is fully relaxed. See the Quick-Start section. This
command restores all registers to their default values.
After this command, reload the custom model. See the
CMD Register (0xFE) section.
Hibernate Mode
The ICs have a low-power hibernate mode that can accu-
rately fuel gauge the battery when the charge/discharge
rate is low. By default, the device automatically enters
and exits the hibernate mode according to the charge/
discharge rate, which minimizes quiescent current (below
5µA) without compromising fuel-gauge accuracy. The ICs
can be forced into hibernate or active modes. Force the
IC into hibernate mode to reduce power consumption in
applications with less than C/4-rate maximum loading.
For applications with higher loading, Maxim recommends
the default configuration of automatic control of hibernate
mode.
In hibernate mode, the device reduces its ADC conver-
sion period and SOC update to once per 45s. See the
HIBRT Register (0x0A) section for details on how the IC
automatically enters and exits hibernate mode.
Figure 6. Insertion Waveform Not Requiring Quick-Start
Command
Figure 7. Insertion Waveform Requiring Quick-Start Command
STEADY SYSTEM
LOAD BEGINS
VCELL HAS
FULLY RELAXED
TIME
VCELL
INITIAL SAMPLE
DEBOUNCE WINDOW
TIME
VCELL
INITIAL SAMPLE
DEBOUNCE WINDOW
QUICK-START DURING
THIS TIME SPAN
STEADY
SYSTEM
LOAD BEGINS
BEST TIME TO
QUICK-START
VCELL HAS
FULLY RELAXED
MAX17048/MAX17049
3μA 1-Cell/2-Cell Fuel Gauge with ModelGauge
www.maximintegrated.com
Maxim Integrated  │  9

<!-- Page 10 -->

Alert Interrupt
The ICs can interrupt a system microcontroller with
five configurable alerts (see Table 1). All alerts can be
disabled or enabled with software. When the interrupt
occurs, the system microcontroller can determine the
cause from the STATUS register.
When an alert is triggered, the IC drives the ALRT
pin logic-low and sets CONFIG.ALRT = 1. The ALRT
pin remains logic-low until the system software writes
CONFIG.ALRT = 0 to clear the alert. The alert function
is enabled by default, so any alert can occur immediately
upon power-up. Entering sleep mode clears no alerts.
Sleep Mode
In sleep mode, the IC halts all operations, reducing cur-
rent consumption to below 1µA. After exiting sleep mode,
the IC continues normal operation. In sleep mode, the
IC does not detect self-discharge. If the battery changes
state while the IC sleeps, the IC cannot detect it, causing
SOC error. Wake up the IC before charging or discharg-
ing. To enter sleep mode, write MODE.EnSleep = 1 and
either:
•	 Hold SDA and SCL logic-low for a period for tSLEEP.
A rising edge on SDA or SCL wakes up the IC.
•	 Write CONFIG.SLEEP = 1. To wake up the IC, write
CONFIG.SLEEP = 0. Other communication does not
wake up the IC. POR does wake up the IC.
Applications which can tolerate 4µA should use hibernate
rather than sleep mode.
Register Summary
All registers must be written and read as 16-bit words;
8-bit writes cause no effect. Any bits marked X (don’t
care) or read only must be written with the rest of the
register, but the value written is ignored by the IC. The
values read from don’t care bits are undefined. Calculate
the register’s value by multiplying the 16-bit word by the
register’s LSb value, as shown in Table 2.
VCELL Register (0x02)
The MAX17048 measures VCELL between the VDD and
GND pins. The MAX17049 measures VCELL between the
CELL and GND pins. VCELL is the average of four ADC
conversions. The value updates every 250ms in active
mode and every 45s in hibernate mode.
SOC Register (0x04)
The ICs calculate SOC using the ModelGauge algorithm.
This register automatically adapts to variation in battery
size since ModelGauge naturally recognizes relative SOC.
The upper byte least-significant bit has units of 1%. The
lower byte provides additional resolution.
The first update is available approximately 1s after POR
of the IC. Subsequent updates occur at variable intervals
depending on application conditions.
Table 1. Alert Interrupt Summary
Table 2. Register Summary
ALERT FUNCTION
WHERE CONFIGURED
INDICATOR BIT
Low SOC
CONFIG.ATHD
STATUS.HD
SOC 1% change
CONFIG.ALSC
STATUS.SC
Reset
VRESET, STATUS.RI
STATUS.VR
Overvoltage
VALRT.MAX
STATUS.VH
Undervoltage
VALRT.MIN
STATUS.VL
ADDRESS
REGISTER
NAME
16-BIT LSb
DESCRIPTION
READ/WRITE
DEFAULT
0x02
VCELL
78.125µV/cell
ADC measurement of VCELL.
R
—
0x04
SOC
1%/256
Battery state of charge.
R
—
0x06
MODE
—
Initiates quick-start, reports hibernate mode,
and enables sleep mode.
W
0x0000
0x08
VERSION
—
IC production version.
R
0x001_
0x0A
HIBRT
—
Controls thresholds for entering and exiting
hibernate mode.
R/W
0x8030
MAX17048/MAX17049
3μA 1-Cell/2-Cell Fuel Gauge with ModelGauge
www.maximintegrated.com
Maxim Integrated  │  10

<!-- Page 11 -->

MODE Register (0x06)
The MODE register allows the system processor to send
special commands to the IC (see Figure 8).
•	 Quick-Start generates a first estimate of OCV and
SOC based on the immediate cell voltage. Use with
caution; see the Quick-Start section.
•	 EnSleep enables sleep mode. See the Sleep Mode
section.
•	 HibStat indicates when the IC is in hibernate mode
(read only).
VERSION Register (0x08)
The value of this read-only register indicates the produc-
tion version of the IC.
Table 2. Register Summary (continued)
Figure 8. MODE Register Format
ADDRESS
REGISTER
NAME
16-BIT LSb
DESCRIPTION
READ/WRITE
DEFAULT
0x0C
CONFIG
—
Compensation to optimize performance, sleep
mode, alert indicators, and configuration.
R/W
0x971C
0x14
VALRT
—
Configures the VCELL range outside of which
alerts are generated.
R/W
0x00FF
0x16
CRATE
0.208%/hr
Approximate charge or discharge rate of the
battery.
R
—
0x18
VRESET/ID
—
Configures VCELL threshold below which
the IC resets itself, ID is a one-time factory-
programmable identifier.
R/W
0x96__
0x1A
STATUS
—
Indicates overvoltage, undervoltage, SOC
change, SOC low, and reset alerts.
R/W
0x01__
0x40 to 0x7F
TABLE
—
Configures battery parameters.
W
—
0xFE
CMD
—
Sends POR command.
R/W
0xFFFF
MSB—ADDRESS 0x06
LSB—ADDRESS 0x07
X
Quick-
Start
EnSleep
HibStat
X
X
X
X
X
X
X
X
X
X
X
X
MSb
LSb
MSb
LSb
MAX17048/MAX17049
3μA 1-Cell/2-Cell Fuel Gauge with ModelGauge
www.maximintegrated.com
Maxim Integrated  │  11

<!-- Page 12 -->

HIBRT Register (0x0A)
To disable hibernate mode, set HIBRT = 0x0000. To
always use hibernate mode, set HIBRT = 0xFFFF (see
Figure 9).
•	 ActThr (active threshold): If at any ADC sample |OCV-
CELL| is greater than ActThr, the IC exits hibernate
mode. 1 LSb = 1.25mV.
•	 HibThr (hibernate threshold). If the absolute value of
CRATE is less than HibThr for longer than 6min, the IC
enters hibernate mode. 1 LSb = 0.208%/hr.
CONFIG Register (0x0C)
•	 RCOMP is an 8-bit value that can be adjusted to opti-
mize IC performance for different lithium chemistries
or different operating temperatures. Contact Maxim
for instructions for optimization. The POR value of
RCOMP is 0x97.
•	 SLEEP forces the IC in or out of sleep mode if Mode.
EnSleep is set. Writing 1 forces the IC to enter sleep
mode, and 0 forces the IC to exit. The POR value of
SLEEP is 0.
•	 ALSC (SOC change alert) enables alerting when
SOC changes by at least 1%. Each alert remains until
STATUS.SC is cleared, after which the alert automati-
cally clears until SOC again changes by 1%. Do not
use this alert to accumulate changes in SOC.
•	 ALRT (alert status bit) is set by the IC when an alert
occurs. When this bit is set, the ALRT pin asserts
low. Clear this bit to service and deassert the ALRT
pin. The power-up default value for ALRT is 0. The
STATUS register specifies why the ALRT pin was
asserted.
•	 ATHD (empty alert threshold) sets the SOC threshold,
where an interrupt is generated on the ALRT pin and
can be programmed from 1% up to 32%. The value is
(32 - ATHD)% (e.g., 00000b → 32%, 00001b → 31%,
00010b → 30%, 11111b → 1%). The POR value of
ATHD is 0x1C, or 4%. The alert only occurs on a falling
edge past this threshold.
Figure 9. HIBRT Register Format
Figure 10. CONFIG Register Format
MSB (HibThr)—ADDRESS 0x0A
LSB (ActThr)—ADDRESS 0x0B
27
26
25
24
23
22
21
20
27
26
25
24
23
22
21
20
MSb
LSb
MSb
LSb
HibThr 20 UNIT: 0.208%/hr
ActThr 20 UNIT: 1.25mV
MSB (RCOMP)—ADDRESS 0x0C
LSB—ADDRESS 0x0D
RCOMP
7
RCOMP
6
RCOMP
5
RCOMP
4
RCOMP
3
RCOMP
2
RCOMP
1
RCOMP
0
SLEEP ALSC ALRT ATHD
4
ATHD
3
ATHD
2
ATHD
1
ATHD
0
MSb
LSb
MSb
LSb
MAX17048/MAX17049
3μA 1-Cell/2-Cell Fuel Gauge with ModelGauge
www.maximintegrated.com
Maxim Integrated  │  12

<!-- Page 13 -->

VALRT Register (0x14)
This register is divided into two thresholds: Voltage alert
maximum (VALRT.MAX) and minimum (VALRT. MIN).
Both registers have 1 LSb = 20mV. The IC alerts while
VCELL > VALRT.MAX or VCELL < VALRT.MIN (see
Figure 11).
CRATE Register (0x16)
The IC calculates an approximate value for the average
SOC rate of change. 1 LSb = 0.208% per hour (not for
conversion to ampere).
VRESET/ID Register (0x18)
See Figure 12.
•	 ID is an 8-bit read-only value that is one-time program-
mable at the factory, which can be used as an identifier
to distinguish multiple cell types in production. Writes
to these bits are ignored.
•	 VRESET[7:1] adjusts a fast analog comparator and a
slower digital ADC threshold to detect battery removal
and reinsertion. For captive batteries, set to 2.5V. For
removable batteries, set to at least 300mV below the
application’s empty voltage, according to the desired
reset threshold for your application. If the comparator
is enabled, the IC resets 1ms after VCELL rises above
the threshold. Otherwise, the IC resets 250ms after the
VCELL register rises above the threshold.
•	 Dis. Set Dis = 1 to disable the analog comparator in
hibernate mode to save approximately 0.5µA.
Figure 11. VALRT Register Format
Figure 12. VRESET/ID Register Format
MSB (VALRT.MIN)—ADDRESS 0x14
LSB (VALRT.MAX)—ADDRESS 0x15
MIN7 MIN6 MIN5 MIN4 MIN3 MIN2 MIN1 MIN0
MAX7 MAX6 MAX5 MAX4 MAX3 MAX2 MAX1 MAX0
MSb
LSb
MSb
LSb
UNIT: 20mV
MSB (VRESET)—ADDRESS 0x18
LSB (ID)—ADDRESS 0x19
27
26
25
24
23
22
21
Dis
ID6
ID5
ID4
ID3
ID2
ID1
ID0
ID
MSb
LSb
MSb
LSb
VRESET 20 UNITS: 40mV
MAX17048/MAX17049
3μA 1-Cell/2-Cell Fuel Gauge with ModelGauge
www.maximintegrated.com
Maxim Integrated  │  13

<!-- Page 14 -->

STATUS Register (0x1A)
An alert can indicate many different conditions. The
STATUS register identifies which alert condition was met.
Clear the corresponding bit after servicing the alert (see
Figure 13).
Reset Indicator:
•	 RI (reset indicator) is set when the device powers up.
Any time this bit is set, the IC is not configured, so the
model should be loaded and the bit should be cleared.
Alert Descriptors:
These bits are set only when they cause an alert (e.g., if
CONFIG.ALSC = 0, then SC is never set).
•	 VH (voltage high) is set when VCELL has been above
ALRT.VALRTMAX.
•	 VL (voltage low) is set when VCELL has been below
ALRT.VALRTMIN.
•	 VR (voltage reset) is set after the device has been
reset if EnVr is set.
•	 HD (SOC low) is set when SOC crosses the value in
CONFIG.ATHD.
•	 SC (1% SOC change) is set when SOC changes by at
least 1% if CONFIG.ALSC is set.
Enable or Disable VRESET Alert:
•	 EnVr (enable voltage reset alert) when set to 1 asserts
the ALRT pin when a voltage-reset event occurs under
the conditions described by the VRESET/ ID register.
TABLE Registers (0x40 to 0x7F)
Contact Maxim for details on how to configure these
registers. The default value is appropriate for some Li+
batteries.
To unlock the TABLE registers, write 0x57 to address
0x3F, and 0x4A to address 0x3E. While TABLE is
unlocked, no ModelGauge registers are updated, so
relock as soon as possible by writing 0x00 to address
0x3F, and 0x00 to address 0x3E.
CMD Register (0xFE)
Writing a value of 0x5400 to this register causes
the device to completely reset as if power had been
removed (see the Power-On Reset (POR) section). The
reset occurs when the last bit has been clocked in. The
IC does not respond with an I2C ACK after this com-
mand sequence.
Application Examples
The ICs have a variety of configurations, depending on
the application. Table 3 shows the most common system
configurations and the proper pin connections for each.
In all cases, the system must provide pullup circuits for
ALRT (if used), SDA, and SDL.
Figure 14 shows an example application for a 1S cell
pack. In this example, the ALRT pin is connected to the
microcontroller’s interrupt input to allow the MAX17048 to
signal when the battery is low. The QSTRT pin is unused
in this application and is connected to GND.
Figure 15 shows a MAX17049 example application using
a 2S cell pack. The MAX17049 is mounted on the system
side and powered from a 3.3V supply generated by the
system. The CELL pin is still connected directly to PACK+.
Figure 13. STATUS Register Format
MSB—ADDRESS 0x1A
LSB—ADDRESS 0x1B
X
EnVR
SC
HD
VR
VL
VH
RI
X
X
X
X
X
X
X
X
MSb
LSb
MSb
LSb
MAX17048/MAX17049
3μA 1-Cell/2-Cell Fuel Gauge with ModelGauge
www.maximintegrated.com
Maxim Integrated  │  14

<!-- Page 15 -->

Figure 14. MAX17048 Application Circuit (1S Cell Pack)
Figure 15. MAX17049 Application Circuit (2S Cell Pack)
Table 3. Possible Application Configurations
SYSTEM CONFIGURATION
IC
VDD
ALRT
QSTRT
1S pack-side location
MAX17048
Power directly from battery
Leave unconnected
Connect to GND
1S host-side location
MAX17048
Power directly from battery
Leave unconnected
Connect to GND
1S host-side location,
low-cell interrupt
MAX17048
Power directly from battery
Connect to system
interrupt
Connect to GND
1S host-side location,
hardware quick-start
MAX17048
Power directly from battery
Leave unconnected
Connect to rising-edge
reset signal
2S pack-side location
MAX17049
Power from +2.5V to +4.5V
LDO in pack
Leave unconnected
Connect to GND
2S host-side location
MAX17049
Power from +2.5V to +4.5V
LDO or PMIC
Leave unconnected
Connect to GND
2S host-side location,
low-cell interrupt
MAX17049
Power from +2.5V to +4.5V
LDO or PMIC
Connect to system
interrupt
Connect to GND
2S host-side location,
hardware quick-start
MAX17049
Power from +2.5V to +4.5V
LDO or PMIC
Leave unconnected
Connect to rising-edge
reset signal
VDD
ALRT
SDA
SCL
CELL
QSTRT
CTG
GND
INTERRUPT
SDA
SCL
SYSTEM µP
I2C MASTER
MAX17048
BATTERY PACK
PROTECTION
0.1µF
VDD
ALRT
SDA
SCL
CELL
QSTRT
CTG
GND
INTERRUPT
SDA
SCL
SYSTEM µP
I2C MASTER
MAX17049
BATTERY PACK
PROTECTION
0.1µF
SYSTEM
2.5V TO 4.5V OUTPUT
MAX17048/MAX17049
3μA 1-Cell/2-Cell Fuel Gauge with ModelGauge
www.maximintegrated.com
Maxim Integrated  │  15

<!-- Page 16 -->

I2C Bus System
The I2C bus system supports operation as a slave-only
device in a single or multislave, and single or multimaster
system. Slave devices can share the bus by uniquely set-
ting the 7-bit slave address. The I2C interface consists of
a serial-data line (SDA) and serial-clock line (SCL). SDA
and SCL provide bidirectional communication between
the IC’s slave device and a master device at speeds up to
400kHz. The IC’s SDA pin operates bidirectionally; that is,
when the IC receives data, SDA operates as an input, and
when the IC returns data, SDA operates as an open-drain
output, with the host system providing a resistive pullup.
The IC always operates as a slave device, receiving and
transmitting data under the control of a master device.
The master initiates all transactions on the bus and gener-
ates the SCL signal, as well as the START and STOP bits,
which begin and end each transaction.
Bit Transfer
One data bit is transferred during each SCL clock cycle,
with the cycle defined by SCL transitioning low-to-high
and then high-to-low. The SDA logic level must remain
stable during the high period of the SCL clock pulse.
Any change in SDA when SCL is high is interpreted as a
START or STOP control signal.
Bus Idle
The bus is defined to be idle, or not busy, when no master
device has control. Both SDA and SCL remain high when
the bus is idle. The STOP condition is the proper method
to return the bus to the idle state.
START and STOP Conditions
The master initiates transactions with a START condition
(S) by forcing a high-to-low transition on SDA while SCL
is high. The master terminates a transaction with a STOP
condition (P), a low-to-high transition on SDA while SCL
is high. A Repeated START condition (Sr) can be used in
place of a STOP then START sequence to terminate one
transaction and begin another without returning the bus to
the idle state. In multimaster systems, a Repeated START
allows the master to retain control of the bus. The START
and STOP conditions are the only bus activities in which
the SDA transitions when SCL is high.
Acknowledge Bits
Each byte of a data transfer is acknowledged with an
acknowledge bit (A) or a no-acknowledge bit (N). Both
the master and the MAX17048 slave generate acknowl-
edge bits. To generate an acknowledge, the receiving
device must pull SDA low before the rising edge of the
acknowledge-related clock pulse (ninth pulse) and keep it
low until SCL returns low. To generate a no- acknowledge
(also called NAK), the receiver releases SDA before the
rising edge of the acknowledge-related clock pulse and
leaves SDA high until SCL returns low. Monitoring the
acknowledge bits allows for detection of unsuccessful
data transfers. An unsuccessful data transfer can occur
if a receiving device is busy or if a system fault has
occurred. In the event of an unsuccessful data transfer,
the bus master should reattempt communication.
Data Order
A byte of data consists of 8 bits ordered most significant
bit (MSb) first. The least significant bit (LSb) of each
byte is followed by the acknowledge bit. The IC registers
composed of multibyte values are ordered MSB first.
The MSB of multibyte registers is stored on even data-
memory addresses.
Slave Address
A bus master initiates communication with a slave device
by issuing a START condition followed by a slave address
(SAddr) and the read/write (R/W) bit. When the bus is
idle, the ICs continuously monitor for a START condition
followed by its slave address. When the ICs receive a
slave address that matches the value in the slave address
register, they respond with an acknowledge bit during the
clock period following the R/W bit. The 7-bit slave address
is fixed to 0x6C (write)/0x6D (read):
Read/Write Bit
The R/W bit following the slave address determines the
data direction of subsequent bytes in the transfer. R/W =
0 selects a write transaction with the following bytes being
written by the master to the slave. R/W = 1 selects a read
transaction with the following bytes being read from the
slave by the master (Table 4).
0110110
MAX17048 /MAX17049
SLAVE ADDRESS
MAX17048/MAX17049
3μA 1-Cell/2-Cell Fuel Gauge with ModelGauge
www.maximintegrated.com
Maxim Integrated  │  16

<!-- Page 17 -->

Bus Timing
The ICs are compatible with any bus timing up to 400kHz.
No special configuration is required to operate at any
speed.
I2C Command Protocols
The command protocols involve several transaction
formats. The simplest format consists of the master
writing the START bit, slave address, R/W bit, and then
monitoring the acknowledge bit for presence of the ICs.
More complex formats, such as the Write Data and Read
Data, read data and execute device-specific operations.
All bytes in each command format require the slave or
host to return an acknowledge bit before continuing with
the next byte. Table 4 shows the key that applies to the
transaction formats.
Basic Transaction Formats
A write transaction transfers 2 or more data bytes to the
ICs. The data transfer begins at the memory address
supplied in the MAddr byte. Control of the SDA signal is
retained by the master throughout the transaction, except
for the acknowledge cycles:
A read transaction transfers 2 or more bytes from the
ICs. Read transactions are composed of two parts, a
write portion followed by a read portion, and are therefore
inherently longer than a write transaction. The write por-
tion communicates the starting point for the read opera-
tion. The read portion follows immediately, beginning with
a Repeated START, slave address with R/W set to a 1.
Control of SDA is assumed by the ICs, beginning with the
slave address acknowledge cycle. Control of the SDA
signal is retained by the ICs throughout the transaction,
except for the acknowledge cycles. The master indicates
the end of a read transaction by responding to the last
byte it requires with a no acknowledge. This signals the
ICs that control of SDA is to remain with the master fol-
lowing the acknowledge clock.
Write: S. SAddr W. A. MAddr. A. Data0. A. Data1. A. P
Read: S. SAddr W. A. MAddr. A. Sr. SAddr R. A. Data0. A. Data1. N. P
Write Portion
Read Portion
Write Data Protocol
The write data protocol is used to write to register to the
ICs starting at memory address MAddr. Data0 represents
the data written to MAddr, Data1 represents the data
written to MAddr + 1, and DataN represents the last data
byte, written to MAddr + N. The master indicates the end
of a write transaction by sending a STOP or Repeated
START after receiving the last acknowledge bit:
S. SAddr W. A. MAddr. A. Data0. A. Data1. A... DataN. A. P
The MSb of the data to be stored at address MAddr can
be written immediately after the MAddr byte is acknowl-
edged. Because the address is automatically incremented
after the LSb of each byte is received by the ICs, the MSb
of the data at address MAddr + 1 can be written imme-
diately after the acknowledgment of the data at address
MAddr. If the bus master continues an autoincremented
write transaction beyond address 4Fh, the ICs ignore
the data. A valid write must include both register bytes.
Data is also ignored on writes to read-only addresses.
Incomplete bytes and bytes that are not acknowledged by
the ICs are not written to memory.
Table 4. I2C Protocol Key
KEY
DESCRIPTION
KEY
DESCRIPTION
S
START bit
Sr
Repeated START
SAddr
Slave address (7 bit)
W
R/W bit = 0
MAddr
Memory address byte
P
STOP bit
Data
Data byte written by master
Data
Data byte returned by slave
A
Acknowledge bit—master
A
Acknowledge bit—slave
N
No acknowledge—master
N
No acknowledge bit—slave
R
R/W bit = 1
MAX17048/MAX17049
3μA 1-Cell/2-Cell Fuel Gauge with ModelGauge
www.maximintegrated.com
Maxim Integrated  │  17

<!-- Page 18 -->

Read Data Protocol
The read data protocol is used to read to register from the
ICs starting at the memory address specified by MAddr.
Both register bytes must be read in the same transaction
for the register data to be valid. Data0 represents the data
byte in memory location MAddr, Data1 represents the
data from MAddr + 1, and DataN represents the last byte
read by the master:
S. SAddr W. A. MAddr. A. Sr. SAddr R. A.
Data0. A. Data1. A... DataN. N. P
Data is returned beginning with the MSb of the data in
MAddr. Because the address is automatically incremented
after the LSb of each byte is returned, the MSb of the data
at address MAddr + 1 is available to the host immediately
after the acknowledgment of the data at address MAddr.
If the bus master continues to read beyond address FFh,
the ICs output data values of FFh. Addresses labeled
Reserved in the memory map return undefined data. The
bus master terminates the read transaction at any byte
boundary by issuing a no acknowledge followed by a
STOP or Repeated START.
+Denotes a lead(Pb)-free/RoHS-compliant package.
*EP = Exposed pad.
T = Tape and reel.
PACKAGE TYPE
PACKAGE CODE
OUTLINE NO.
LAND PATTERN NO.
8 WLP
W80B1+1
21-0555
Refer to
Application Note 1891
8 TDFN-EP
T822+3
21-0168
90-0065
PART
TEMP RANGE
PIN-PACKAGE
DESCRIPTION
MAX17048G+
-40°C to +85°C
8 TDFN-EP*
1-Cell ModelGauge IC
MAX17048G+T10
-40°C to +85°C
8 TDFN-EP*
1-Cell ModelGauge IC
MAX17048X+
-40°C to +85°C
8 WLP
1-Cell ModelGauge IC
MAX17048X+T10
-40°C to +85°C
8 WLP
1-Cell ModelGauge IC
MAX17049G+
-40°C to +85°C
8 TDFN-EP*
2-Cell ModelGauge IC
MAX17049G+T10
-40°C to +85°C
8 TDFN-EP*
2-Cell ModelGauge IC
MAX17049X+
-40°C to +85°C
8 WLP
2-Cell ModelGauge IC
MAX17049X+T10
-40°C to +85°C
8 WLP
2-Cell ModelGauge IC
MAX17048/MAX17049
3μA 1-Cell/2-Cell Fuel Gauge with ModelGauge
www.maximintegrated.com
Maxim Integrated  │  18
Package Information
For the latest package outline information and land patterns (footprints), go to www.maximintegrated.com/packages. Note that a “+”,
“#”, or “-” in the package code indicates RoHS status only. Package drawings may show a different suffix character, but the drawing
pertains to the package regardless of RoHS status.
Ordering Information

<!-- Page 19 -->

REVISION
NUMBER
REVISION
DATE
DESCRIPTION
PAGES
CHANGED
0
2/12
Initial release
—
1
4/12
Corrected byte-order errors
10, 11, 13
2
8/12
Updated soldering temperature in Absolute Maximum Ratings; corrected Hibernate
register names that were switched
2, 12, 14
3
10/12
Corrected VDD pin names in Absolute Maximum Ratings and Electrical
Characteristics
2, 3
4
8/13
Corrected version number
10
5
10/13
Corrected conditions for Supply Current in Electrical Charateristics
2
6
10/14
Updated VRESET recommendation from 40mV–80mV below 300mW empty voltage
and corrected VR bit of Status register
13, 14
7
11/16
Updated front page title, description, applications, and features
1
Maxim Integrated cannot assume responsibility for use of any circuitry other than circuitry entirely embodied in a Maxim Integrated product. No circuit patent licenses
are implied. Maxim Integrated reserves the right to change the circuitry and specifications without notice at any time. The parametric values (min and max limits)
shown in the Electrical Characteristics table are guaranteed. Other parametric values quoted in this data sheet are provided for guidance.
Maxim Integrated and the Maxim Integrated logo are trademarks of Maxim Integrated Products, Inc.
©  2016 Maxim Integrated Products, Inc.  │  19
MAX17048/MAX17049
3μA 1-Cell/2-Cell Fuel Gauge with ModelGauge
Revision History
For pricing, delivery, and ordering information, please contact Maxim Direct at 1-888-629-4642, or visit Maxim Integrated’s website at www.maximintegrated.com.

---

# 3. AP2112 — 600mA CMOS LDO Regulator

> **Role:** Regulator — AP2112K-3.3  
> **Covers:** `C51118` (Regulator: 3.3V)

<!-- Page 1 -->

AP2112
Document number: DS39724  Rev. 2 - 2
1 of 18
www.diodes.com
June 2017
© Diodes Incorporated

AP2112
600mA CMOS LDO REGULATOR WITH ENABLE

Description
The AP2112 is CMOS process low dropout linear regulator with
enable function, the regulator delivers a guaranteed 600mA (min.)
continuous load current.

The AP2112 is available with a fixed output voltage of 1.2V, 1.8V,
2.5V, 2.6V, or 3.3V. The LDO has an output accuracy of ±1.5% and a
very fast loop response providing excellent performance for dealing
with line and load transients. The AP2112 includes an auto discharge
function which connects the output to ground via 60 of resistance
when the device is disabled.

The regulator features low power consumption, and provides SOT25,
SOT89-5, and SO-8 packages. Previously SOT-23-5, SOT-89-5 and
SOIC-8 packages were respectively identified as SOT23-5, SOT89-5
and SO-8 but have been renamed to match the latest Diodes
Incorporated‘s nomenclature.

Features

Output Voltage Accuracy: ±1.5%

Output Current: 600mA (Min.)

Foldback Short Current Protection: 50mA

Enable Function to Turn ON/OFF VOUT

Low Dropout Voltage (3.3V): 250mV (Typ.) @IOUT = 600mA

Excellent Load Regulation: 0.2%/A (Typ.)

Excellent Line Regulation: 0.02%/V (Typ.)

Low Quiescent Current: 55µA (Typ.)

Low Standby Current: 0.01µA (Typ.)

Low Output Noise: 50µVRMS

PSRR: 100Hz -65dB, 1kHz -65dB

OTSD Protection

Stable with 1.0µF Flexible Cap: Ceramic, Tantalum and
Aluminum Electrolytic

Operation Temperature Range: -40°C to +85°C

ESD: MM 400V, HBM 4000V

Totally Lead-Free & Fully RoHS Compliant (Notes 1 & 2)

Halogen and Antimony Free. “Green” Device (Note 3)

Applications

Laptop Computer

LCD Monitor

Portable DVD

Pin Assignments

(Top View)                                      (Top View)

1
2
3
4
5
VOUT
NC
EN
GND
VIN
1
2
3
4
8
7
6
5
VOUT
NC
VIN
GND
GND
EN
NC
NC

                         SOT25                                              SO-8

(Top View)                                       (Top View)

1
2
3
4
5
VOUT
VIN
NC
GND
EN

1
2
3
4
5
VOUT
VIN
NC
GND
EN

   (R5 Package)                                  (R5A Package)
SOT89-5 (Option 1)

(Top View)                                      (Top View)

1
2
3
4
5
VOUT
VIN
NC
GND
EN

1
2
3
4
5
VOUT
VIN
EN
GND
NC

   (R5 Package)                                  (R5A Package)
SOT89-5 (Option 2)

Notes:
1. No purposely added lead. Fully EU Directive 2002/95/EC (RoHS) & 2011/65/EU (RoHS 2) compliant.

2. See http://www.diodes.com/quality/lead_free.html for more information about Diodes Incorporated‘s definitions of Halogen- and Antimony-free, "Green"

    and Lead-free.

3. Halogen- and Antimony-free "Green‖ products are defined as those which contain <900ppm bromine, <900ppm chlorine (<1500ppm total Br + Cl) and

    <1000ppm antimony compounds.

<!-- Page 2 -->

AP2112
Document number: DS39724  Rev. 2 - 2
2 of 18
www.diodes.com
June 2017
© Diodes Incorporated

AP2112

Typical Applications Circuit (Note 4)

AP2112
GND
VIN
CIN
VOUT
COUT
OFF
VEN
VIN
VOUT
1mF
1.2V/1.8V/
2.5V/2.6V/
3.3V
1mF
ON

Note 4:      It is recommended to use X7R or X5R dielectric capacitor if 1.0µF ceramic capacitor is selected as input/output capacitors.

Pin Descriptions

Pin Number
Pin Name
Function
SOT25
SOT89-5
SO-8
1
4
8
VIN
Input Voltage
2
2
6, 7
GND
GND
3
3 (R5)
5
EN
Chip Enable, H – normal work, L – shutdown output
1 (R5A)
—
1 (R5)
2, 3, 4
NC
No Connection
3 (R5A)
5
5
1
VOUT
Output Voltage

Functional Block Diagram

Shutdown Logic
Thermal
Shutdown
Foldback
Current Limit
VREF
GND
EN
VOUT
VIN
3M
4(4){8}[1]
2(2){6,7}[2]
3(1){5}[3]
5(5){1}[5]
A (B){C}[D]
A: SOT89-5 (R5)
B: SOT89-5 (R5A)
C: SO-8
D: SOT25

<!-- Page 3 -->

AP2112
Document number: DS39724  Rev. 2 - 2
3 of 18
www.diodes.com
June 2017
© Diodes Incorporated

AP2112

Absolute Maximum Ratings (Note 5)

Symbol
Parameter
Rating
Unit
VCC
Power Supply Voltage
6.5
V
TJ
Operating Junction Temperature Range
+150
°C
TSTG
Storage Temperature Range
-65 to +150
°C
TLEAD
Lead Temperature (Soldering, 10 Seconds)
+260
°C
θJA
Thermal Resistance (Junction to Ambient)(No Heatsink)
SOT25
184
°C/W
SO-8
114
SOT89-5
120
—
ESD (Machine Model)
400
V
—
ESD (Human Body Model)
4000
V

Note 5:    Stresses greater than those listed under ―Absolute Maximum Ratings‖ may cause permanent damage to the device. These are stress ratings only, and
functional operation of the device at these or any other conditions beyond those indicated under ―Recommended Operating Conditions‖ is not implied.
Exposure to ―Absolute Maximum Ratings‖ for extended periods may affect device reliability.

Recommended Operating Conditions

Symbol
Parameter
Min
Max
Unit
VIN
Supply Voltage
2.5
6.0
V
TA
Ambient Operation Temperature Range
-40
+85
°C

<!-- Page 4 -->

AP2112
Document number: DS39724  Rev. 2 - 2
4 of 18
www.diodes.com
June 2017
© Diodes Incorporated

AP2112

Electrical Characteristics
AP2112-1.2 Electrical Characteristics (@VIN = 2.5V, CIN = 1.0µF (Ceramic), COUT = 1.0µF (Ceramic), Typical TA = +25°C,
unless otherwise specified (Note 6))

Symbol
Parameter
Conditions
Min
Typ
Max
Unit
VOUT
Output Voltage
VIN = 2.5V, 1mA ≤ IOUT ≤ 30mA
VOUT
*98.5%
1.2
VOUT
*101.5%
V
IOUT(MAX)
Maximum Output Current
VIN = 2.5V, VOUT = 1.182V to 1.218V
600
—
—
mA
(∆VOUT/VOUT)/∆IOUT
Load Regulation
VIN = 2.5V, 1mA ≤ IOUT ≤ 600mA
-1
0.2
1
%/A
(∆VOUT/VOUT)/∆VIN
Line Regulation
2.5V ≤ VIN  ≤ 6V, IOUT = 30mA
-0.1
0.02
0.1
%/V
VDROP
Dropout Voltage
IOUT = 10mA
—
1000
1300
mV
IOUT = 300mA
—
1000
1300
IOUT = 600mA
—
1000
1300
IQ
Quiescent Current
VIN = 2.5V, IOUT = 0mA
—
55
80
µA
ISTD
Standby Current
VIN = 2.5V, VEN in OFF mode
—
0.01
1.0
µA
PSRR
Power Supply Rejection Ratio
Ripple 0.5Vp-p
VIN = 2.5V,
IOUT = 100mA
f = 100Hz
—
65
—
dB
f = 1kHz
—
65
—
(∆VOUT/VOUT)/∆T
Output Voltage Temperature
Coefficient
IOUT = 30mA
TA = -40°C to +85°C
—
±100
—
ppm/°C
ISHORT
Short Current Limit
VOUT = 0V
—
50
—
mA
VNOISE
RMS Output Noise
No Load, 10Hz ≤ f ≤ 100kHz
—
50
—
µVRMS
VIH
VEN High Voltage
Enable logic high, regulator on
1.5
—
6.0
V
VIL
VEN Low Voltage
Enable logic low, regulator off
0
—
0.4
tS
Start-up Time
No Load
—
20
—
µs
RPD
EN Pull Down Resistor
—
—
3.0
—
MΩ
RDCHG
VOUT Discharge Resistor
Set EN pin at Low
—
60
—
Ω
TOTSD
Thermal Shutdown Temperature
—
—
+160
—
°C
THYOTSD
Thermal Shutdown Hysteresis
—
—
+25
—
θJC
Thermal Resistance
(Junction to Case)
SOT25
—
96
—
°C/W
SO-8
—
75
—
SOT89-5
—
47
—
Note 6:        Production testing at TA = +25°C. Over temperature specifications guaranteed by design only.

<!-- Page 5 -->

AP2112
Document number: DS39724  Rev. 2 - 2
5 of 18
www.diodes.com
June 2017
© Diodes Incorporated

AP2112

Electrical Characteristics (Cont.)
AP2112-1.8 Electrical Characteristics (@VIN = 2.8V, CIN = 1.0µF (Ceramic), COUT = 1.0µF (Ceramic), Typical TA = +25°C,
unless otherwise specified (Note 6))

Symbol
Parameter
Conditions
Min
Typ
Max
Unit
VOUT
Output Voltage
VIN = 2.8V, 1mA ≤ IOUT ≤ 30mA
VOUT
*98.5%
1.8
VOUT
*101.5%
V
IOUT(MAX)
Maximum Output Current
VIN = 2.8V, VOUT = 1.773V to 1.827V
600
—
—
mA
(∆VOUT/VOUT)/∆IOUT
Load Regulation
VOUT = 1.8V, VIN = VOUT+1V,
1mA ≤ IOUT ≤ 600mA
-1
0.2
1
%/A
(∆VOUT/VOUT)/∆VIN
Line Regulation
2.8V ≤ VIN ≤ 6V, IOUT = 30mA
-0.1
0.02
0.1
%/V
VDROP
Dropout Voltage
IOUT = 10mA
—
500
700
mV
IOUT = 300mA
—
500
700
IOUT = 600mA
—
500
700
IQ
Quiescent Current
VIN = 2.8V, IOUT = 0mA
—
55
80
µA
ISTD
Standby Current
VIN = 2.8V, VEN in OFF mode
—
0.01
1.0
µA
PSRR
Power Supply Rejection Ratio
Ripple 0.5Vp-p
VIN = 2.8V,
IOUT = 100mA
f = 100Hz
—
65
—
dB
f = 1kHz
—
65
—
(∆VOUT/VOUT)/∆T
Output Voltage Temperature
Coefficient
IOUT = 30mA
TA = -40°C to +85°C
—
±100
—
ppm/°C
ISHORT
Short Current Limit
VOUT = 0V
—
50
—
mA
VNOISE
RMS Output Noise
No Load, 10Hz ≤ f ≤ 100kHz
—
50
—
µVRMS
VIH
VEN High Voltage
Enable logic high, regulator on
1.5
—
6.0
V
VIL
VEN Low Voltage
Enable logic low, regulator off
0
—
0.4
tS
Start-up Time
No Load
—
20
—
µs
RPD
EN Pull Down Resistor
—
—
3.0
—
MΩ
RDCHG
VOUT Discharge Resistor
Set EN pin at Low
—
60
—
Ω
TOTSD
Thermal Shutdown Temperature
—
—
+160
—
°C
THYOTSD
Thermal Shutdown Hysteresis
—
—
+25
—
θJC
Thermal Resistance
(Junction to Case)
SOT25
—
96
—
°C/W
SO-8
—
75
—
SOT89-5
—
47
—
Note 6:        Production testing at TA = +25°C. Over temperature specifications guaranteed by design only.

<!-- Page 6 -->

AP2112
Document number: DS39724  Rev. 2 - 2
6 of 18
www.diodes.com
June 2017
© Diodes Incorporated

AP2112

Electrical Characteristics (Cont.)
AP2112-2.5 Electrical Characteristics (@VIN = 3.5V, CIN = 1.0µF (Ceramic), COUT = 1.0µF (Ceramic), Typical TA = +25°C,
unless otherwise specified (Note 6))

Symbol
Parameter
Conditions
Min
Typ
Max
Unit
VOUT
Output Voltage
VIN  = 3.5V, 1mA ≤ IOUT ≤ 30mA
VOUT
*98.5%
2.5
VOUT
*101.5%
V
IOUT(MAX)
Maximum Output Current
VIN = 3.5V,
VOUT = 2.463V to 2.537V
600
—
—
mA
(∆VOUT/VOUT)/∆IOUT
Load Regulation
VOUT = 2.5V, VIN = VOUT+1V,
1mA ≤ IOUT ≤ 600mA
-1
0.2
1
%/A
(∆VOUT/VOUT)/∆VIN
Line Regulation
3.5V ≤ VIN ≤ 6V, IOUT = 30mA
-0.1
0.02
0.1
%/V
VDROP
Dropout Voltage
IOUT  = 10mA
—
5
8
mV
IOUT = 300mA
—
125
200
IOUT = 600mA
—
250
400
IQ
Quiescent Current
VIN = 3.5V, IOUT = 0mA
—
55
80
µA
ISTD
Standby Current
VIN = 3.5V, VEN in OFF mode
—
0.01
1.0
µA
PSRR
Power Supply Rejection Ratio
Ripple 0.5Vp-p
VIN = 3.5V,
IOUT = 100mA
f = 100Hz
—
65
—
dB
f = 1KHz
—
65
—
(∆VOUT/VOUT)/∆T
Output Voltage Temperature
Coefficient
IOUT = 30mA
TA = -40°C to +85°C
—
±100
—
ppm/°C
ISHORT
Short Current Limit
VOUT = 0V
—
50
—
mA
VNOISE
RMS Output Noise
No Load, 10Hz ≤ f ≤ 100kHz
—
50
—
µVRMS
VIH
VEN High Voltage
Enable logic high, regulator on
1.5
—
6.0
V
VIL
VEN Low Voltage
Enable logic low, regulator off
0
—
0.4
tS
Start-up Time
No Load
—
20
—
µs
RPD
EN Pull Down Resistor
—
—
3.0
—
MΩ
RDCHG
VOUT Discharge Resistor
Set EN pin at Low
—
60
—
Ω
TOTSD
Thermal Shutdown Temperature
—
—
+160
—
°C
THYOTSD
Thermal Shutdown Hysteresis
—
—
+25
—
θJC
Thermal Resistance
(Junction to Case)
SOT25
—
96
—
°C/W
SO-8
—
75
—
SOT89-5
—
47
—
Note 6:       Production testing at TA = +25°C. Over temperature specifications guaranteed by design only.

<!-- Page 7 -->

AP2112
Document number: DS39724  Rev. 2 - 2
7 of 18
www.diodes.com
June 2017
© Diodes Incorporated

AP2112

Electrical Characteristics (Cont.)
AP2112-2.6 Electrical Characteristics (@VIN = 3.6V, CIN = 1.0µF (Ceramic), COUT = 1.0µF (Ceramic), Typical TA = +25°C,
unless otherwise specified (Note 6))

Symbol
Parameter
Conditions
Min
Typ
Max
Unit
VOUT
Output Voltage
VIN = 3.6V, 1mA ≤ IOUT ≤ 30mA
VOUT
*98.5%
2.6
VOUT
*101.5%
V
IOUT(MAX)
Maximum Output Current
VIN = 3.6V,
VOUT = 2.561V to 2.639V
600
—
—
mA
(∆VOUT/VOUT)/∆IOUT
Load Regulation
VOUT = 2.6V, VIN = VOUT+1V,
1mA ≤ IOUT ≤ 600mA
-1
0.2
1
%/A
(∆VOUT/VOUT)/∆VIN
Line Regulation
3.6V ≤ VIN ≤ 6V, IOUT = 30mA
-0.1
0.02
0.1
%/V
VDROP
Dropout Voltage
IOUT = 10mA
—
5
8
mV
IOUT = 300mA
—
125
200
IOUT = 600mA
—
250
400
IQ
Quiescent Current
VIN = 3.6V, IOUT = 0mA
—
55
80
µA
ISTD
Standby Current
VIN = 3.6V, VEN in OFF mode
—
0.01
1.0
µA
PSRR
Power Supply Rejection Ratio
Ripple 0.5Vp-p
VIN = 3.6V,
IOUT = 100mA
f = 100Hz
—
65
—
dB
f = 1kHz
—
65
—
(∆VOUT/VOUT)/∆T
Output Voltage
Temperature Coefficient
IOUT = 30mA
TA = -40°C to +85°C
—
±100
—
ppm/°C
ISHORT
Short Current Limit
VOUT = 0V
—
50
—
mA
VNOISE
RMS Output Noise
No Load, 10Hz ≤ f ≤ 100kHz
—
50
—
µVRMS
VIH
VEN High Voltage
Enable logic high, regulator on
1.5
—
6.0
V
VIL
VEN Low Voltage
Enable logic low, regulator off
0
—
0.4
tS
Start-up Time
No Load
—
20
—
µs
RPD
EN Pull Down Resistor
—
—
3.0
—
MΩ
RDCHG
VOUT Discharge Resistor
Set EN pin at Low
—
60
—
Ω
TOTSD
Thermal Shutdown Temperature
—
—
+160
—
°C
THYOTSD
Thermal Shutdown Hysteresis
—
—
+25
—
θJC
Thermal Resistance
(Junction to Case)
SOT25
—
96
—
°C/W
SO-8
—
75
—
SOT89-5
—
47
—
Note 6:       Production testing at TA = +25°C. Over temperature specifications guaranteed by design only.

<!-- Page 8 -->

AP2112
Document number: DS39724  Rev. 2 - 2
8 of 18
www.diodes.com
June 2017
© Diodes Incorporated

AP2112

Electrical Characteristics (Cont.)
AP2112-3.3 Electrical Characteristics (@VIN = 4.3V, CIN = 1.0µF (Ceramic), COUT = 1.0µF (Ceramic), Typical TA = +25°C,
unless otherwise specified (Note 6))

Symbol
Parameter
Conditions
Min
Typ
Max
Unit
VOUT
Output Voltage
VIN = 4.3V, 1mA ≤ IOUT ≤ 30mA
VOUT
*98.5%
3.3
VOUT
*101.5%
V
IOUT(MAX)
Maximum Output Current
VIN = 4.3V, VOUT = 3.251V to 3.350V
600
—
—
mA
(∆VOUT/VOUT)/∆IOUT
Load Regulation
VIN = 4.3V, 1mA ≤ IOUT ≤ 600mA
-1
0.2
1
%/A
(∆VOUT/VOUT)/∆VIN
Line Regulation
4.3V≤ VIN  ≤ 6V, IOUT = 30mA
-0.1
0.02
0.1
%/V
VDROP
Dropout Voltage
IOUT = 10mA
—
5
8
mV
IOUT = 300mA
—
125
200
IOUT = 600mA
—
250
400
IQ
Quiescent Current
VIN = 4.3V, IOUT = 0mA
—
55
80
µA
ISTD
Standby Current
VIN = 4.3V, VEN in OFF mode
—
0.01
1.0
µA
PSRR
Power Supply Rejection Ratio
Ripple 0.5Vp-p
VIN = 4.3V,
IOUT = 100mA
f = 100Hz
—
65
—
dB
f = 1kHz
—
65
—
(∆VOUT/VOUT)/∆T
Output Voltage Temperature
Coefficient
IOUT = 30mA
TA = -40°C to +85°C
—
±100
—
ppm/°C
ISHORT
Short Current Limit
VOUT = 0V
—
50
—
mA
VNOISE
RMS Output Noise
No Load, 10Hz ≤ f ≤ 100kHz
—
50
—
µVRMS
VIH
VEN High Voltage
Enable logic high, regulator on
1.5
—
6.0
V
VIL
VEN Low Voltage
Enable logic low, regulator off
0
—
0.4
tS
Start-up Time
No Load
—
20
—
µs
RPD
EN Pull Down Resistor
—
—
3.0
—
MΩ
RDCHG
VOUT Discharge Resistor
Set EN pin at Low
—
60
—
Ω
TOTSD
Thermal Shutdown Temperature
—
—
+160
—
°C
THYOTSD
Thermal Shutdown Hysteresis
—
—
+25
—
θJC
Thermal Resistance
(Junction to Case)
SOT25
—
96
—
°C/W
SO-8
—
75
—
SOT89-5
—
47
—
Note 6:       Production testing at TA = +25°C. Over temperature specifications guaranteed by design only.

<!-- Page 9 -->

AP2112
Document number: DS39724  Rev. 2 - 2
9 of 18
www.diodes.com
June 2017
© Diodes Incorporated

AP2112

Performance Characteristics

Output Voltage vs. Input Voltage                                              Output Voltage vs. Input Voltage

Quiescent Current vs. Temperature                                         Quiescent Current vs. Input Voltage

Output Voltage vs. Temperature                                               Output Voltage vs. Temperature

0.0
0.5
1.0
1.5
2.0
2.5
3.0
3.5
4.0
4.5
5.0
5.5
6.0
0.0
0.2
0.4
0.6
0.8
1.0
1.2
1.4
1.6
NO Load
 TA=-40
oC
 TA=25
oC
  TA=85
oC
VOUT=1.2V

Output Voltage (V)
Input Voltage (V)
0.0
0.5
1.0
1.5
2.0
2.5
3.0
3.5
4.0
4.5
5.0
5.5
6.0
0.0
0.5
1.0
1.5
2.0
2.5
3.0
3.5
4.0
Output Voltage (V)
Input Voltage (V)
 TA=-40
oC
 TA=25
oC
 TA=85
oC
VOUT=3.3V
No Load
-40.0
-20.0
0.0
20.0
40.0
60.0
80.0
46
48
50
52
54
56
58
60
62
64
66
68
70
VIN=2.5V
No Load
Quiescent Current (mA)
Temperature (
oC)
1.0
1.5
2.0
2.5
3.0
3.5
4.0
4.5
5.0
5.5
6.0
0
10
20
30
40
50
60
70
Quiescent Current (mA)
 TA=-40
OC
 TA=25
OC
 TA=85
OC
No Load
Input Voltage (V)
-40
-20
0
20
40
60
80
3.25
3.26
3.27
3.28
3.29
3.30
3.31
3.32
3.33
3.34
3.35
Output Voltage (V)
Temperature(
oC)
 IOUT=10mA
 IOUT=100mA
 IOUT=300mA
 IOUT=600mA
VIN=4.3V
CIN=1mF
COUT=1mF
-40.0
-20.0
0.0
20.0
40.0
60.0
80.0
1.200
1.202
1.204
1.206
1.208
1.210
 IOUT=300mA
 IOUT=600mA
 IOUT=10mA
 IOUT=100mA
VIN=2.5V
CIN=1mF
COUT=1mF
Output Voltage (V)
Temperature (
oC)

<!-- Page 10 -->

AP2112
Document number: DS39724  Rev. 2 - 2
10 of 18
www.diodes.com
June 2017
© Diodes Incorporated

AP2112

Performance Characteristics (Cont.)

Output Voltage vs. Output Current                                          Output Voltage vs. Output Current

Output Voltage vs. Output Current                                           Output Voltage vs. Output Current

Dropout Voltage vs. Output Current                                          Ground Current vs. Output Current

0.0
0.1
0.2
0.3
0.4
0.5
0.6
0.7
0.8
0.9
1.0
-0.1
0.0
0.1
0.2
0.3
0.4
0.5
0.6
0.7
0.8
0.9
1.0
1.1
1.2
1.3
VIN=2.5V
Output Voltage (V)
Output Current (A)
 TA= -40
oC
 TA=25
oC
 TA=85
oC
0.0
0.1
0.2
0.3
0.4
0.5
0.6
0.7
0.8
0.9
1.0
-0.5
0.0
0.5
1.0
1.5
2.0
2.5
3.0
3.5
4.0
Output Voltage (V)
Output Current (A)
 TA=-40
oC
 TA= 25
oC
 TA= 85
oC
VIN=4.3V
0.0
0.1
0.2
0.3
0.4
0.5
0.6
0.7
0.8
0.9
1.0
0.0
0.2
0.4
0.6
0.8
1.0
1.2
T
A=25
oC
CIN=1mF
COUT=1mF
 VIN=5V
 VIN=2V
 VIN=5.5V
 VIN=6V
 VIN=2.5V
Output Voltage (V)
Output Current (A)
0.0
0.1
0.2
0.3
0.4
0.5
0.6
0.7
0.8
0.9
1.0
0.0
0.5
1.0
1.5
2.0
2.5
3.0
3.5
4.0
Output Voltage (V)
Output Current (A)
 VIN=4.0V
 VIN=4.3V
 VIN=5.0V
 VIN=5.5V
 VIN=6.0V
TA=25
oC
CIN=1mF
COUT=1mF
0.0
0.1
0.2
0.3
0.4
0.5
0.6
40
60
80
100
120
140
160
180
200
220
240
260
Ground Current (mA)
Output Current (A)
 TA=-40
oC
 TA= 25
oC
 TA= 85
oC
VIN=4.3V
0.0
0.1
0.2
0.3
0.4
0.5
0.6
0
50
100
150
200
250
300
350
Dropout Voltage (mV)
Output Current (A)
 TA=-40
oC
 TA= 25
oC
 TA= 85
oC
VOUT=3.3V

<!-- Page 11 -->

AP2112
Document number: DS39724  Rev. 2 - 2
11 of 18
www.diodes.com
June 2017
© Diodes Incorporated

AP2112

Performance Characteristics (Cont.)

PSRR vs. Frequency                                                                  Load Transient

Enable On                                                                                Enable Off

Application Note
In some unusual applications where a current load could be present at the output before the part is enabled the fold back current limiting may
prevent the part from starting. Applications with multiple supplies or negative supplies need to be evaluated for this possibility. Product testing
where a current source is applied before the part is enabled could be another area of concern.  With a normal load as shown below there is no
interference of the fold back current limiting circuit.

100
1k
10k
100k
30
35
40
45
50
55
60
65
70
 IOUT=10mA
IOUT=100mA
 IOUT=300mA
VOUT=1.2V
PSRR (dB)
Frequency (Hz)
20
VIN=2.5V
Ripple=0.5V
0mA
VIN=2.5V, CIN=1mF, COUT=1mF
CH1: VOUT
10mV/div
CH2: IOUT
200mA/div
600mA
VIN
(2V/div)
VIN
(2V/div)
VEN
(2V/div)
VEN
(2V/div)
VOUT
(2V/div)
VOUT
(2V/div)
20ms/div
VIN
(2V/div)
VIN
(2V/div)
VEN
(2V/div)
VEN
(2V/div)
VOUT
(2V/div)
VOUT
(2V/div)
200ms/div
0.0
0.1
0.2
0.3
0.4
0.5
0.6
0.7
0.8
0.9
1.0
0.0
0.5
1.0
1.5
2.0
2.5
3.0
3.5
4.0
Output Voltage (V)
Output Current (A)
 VIN=4.0V
 VIN=4.3V
 VIN=5.0V
 VIN=5.5V
 VIN=6.0V
TA=25
oC
CIN=1mF
COUT=1mF
Load Line

<!-- Page 12 -->

AP2112
Document number: DS39724  Rev. 2 - 2
12 of 18
www.diodes.com
June 2017
© Diodes Incorporated

AP2112

Ordering Information

AP2112 X - X X X
Packing
Package
K : SOT25
M : SO-8
Product Name
Output Voltage
1.8 : 1.8V
2.5 : 2.5V
2.6 : 2.6V
1.2 : 1.2V
RoHS/Green
R5/R5A : SOT89-5
TR : Tape & Reel
G1 : Green
3.3 : 3.3V

Package
Temperature
Range
Condition
Part Number
Marking ID
Packing
SOT25
-40 to +85°C
1.2V
AP2112K-1.2TRG1
G3L
3000/7‖/Tape & Reel
1.8V
AP2112K-1.8TRG1
G3M
3000/7‖/Tape & Reel
2.5V
AP2112K-2.5TRG1
G3N
3000/7‖/Tape & Reel
2.6V
AP2112K-2.6TRG1
G5N
3000/7‖/Tape & Reel
3.3V
AP2112K-3.3TRG1
G3P
3000/7‖/Tape & Reel
SO-8
-40 to +85°C
1.2V
AP2112M-1.2TRG1
2112M-1.2G1
4000/13‖/Tape & Reel
1.8V
AP2112M-1.8TRG1
2112M-1.8G1
4000/13‖/Tape & Reel
2.5V
AP2112M-2.5TRG1
2112M-2.5G1
4000/13‖/Tape & Reel
2.6V
AP2112M-2.6TRG1
2112M-2.6G1
4000/13‖/Tape & Reel
3.3V
AP2112M-3.3TRG1
2112M-3.3G1
4000/13‖/Tape & Reel
SOT89-5
-40 to +85°C
1.2V(R5)
AP2112R5-1.2TRG1
G37D
1000/7‖/Tape & Reel
1.8V(R5)
AP2112R5-1.8TRG1
G37E
1000/7‖/Tape & Reel
2.5V(R5)
AP2112R5-2.5TRG1
G37F
1000/7‖/Tape & Reel
2.6V(R5)
AP2112R5-2.6TRG1
G13F
1000/7‖/Tape & Reel
3.3V(R5)
AP2112R5-3.3TRG1
G37G
1000/7‖/Tape & Reel
SOT89-5
-40 to +85°C
1.2V(R5A)
AP2112R5A-1.2TRG1
G33C
1000/7‖/Tape & Reel
1.8V(R5A)
AP2112R5A-1.8TRG1
G33E
1000/7‖/Tape & Reel
2.5V(R5A)
AP2112R5A-2.5TRG1
G28G
1000/7‖/Tape & Reel
2.6V(R5A)
AP2112R5A-2.6TRG1
G13E
1000/7‖/Tape & Reel
3.3V(R5A)
AP2112R5A-3.3TRG1
G28H
1000/7‖/Tape & Reel

<!-- Page 13 -->

AP2112
Document number: DS39724  Rev. 2 - 2
13 of 18
www.diodes.com
June 2017
© Diodes Incorporated

AP2112

Marking Information

(1) SOT25

XXX

(2) SO-8

(3) SOT89-5

: Logo
XXX : Marking ID (See Ordering Information)
XXXX
YWWAXX
First Line: Logo and Marking ID
Second line: Date Code
Y: Year
WW: Work Week of Molding
A: Assembly House Code
XX: 7th and 8th Digits of Batch Number
2112M-X.XG1
YWWAXX
First line: Logo and Marking ID
Second line: Date Code
Y: Year
WW: Work Week of Molding
A: Assembly House Code
XX: 7th and 8th Digits of Batch Number

<!-- Page 14 -->

AP2112
Document number: DS39724  Rev. 2 - 2
14 of 18
www.diodes.com
June 2017
© Diodes Incorporated

AP2112

Package Outline Dimensions (Previously identified as SOT-23-5 for this product)
Please see http://www.diodes.com/package-outlines.html for the latest version.

SOT25

Suggested Pad Layout
Please see http://www.diodes.com/package-outlines.html for the latest version.

SOT25

Note:
The suggested land pattern dimensions have been provided for reference only, as actual pad layouts may vary depending on application. These
dimensions may be modified based on user equipment capability or fabrication criteria. A more robust pattern may be desired for wave soldering
and is calculated by adding 0.2 mm to the ‗Z‘ dimension. For further information, please reference document IPC-7351A, Naming Convention for
Standard SMT Land Patterns, and for International grid details, please see document IEC, Publication 97.

Note:
For high voltage applications, the appropriate industry sector guidelines should be considered with regards to creepage and clearance distances
between device Terminals and PCB tracking.

SOT25
Dim
Min
Max Typ
A
0.35
0.50 0.38
B
1.50
1.70 1.60
C
2.70
3.00 2.80
D
-
-
0.95
H
2.90
3.10 3.00
J
0.013 0.10 0.05
K
1.00
1.30 1.10
L
0.35
0.55 0.40
M
0.10
0.20 0.15
N
0.70
0.80 0.75

0°
8°
-
All Dimensions in mm
Dimensions
Value
Z
3.20
G
1.60
X
0.55
Y
0.80
C1
2.40
C2
0.95
A
M
J
L
D
B C
H
K
N
X
Z
Y
C1
C2
C2
G

<!-- Page 15 -->

AP2112
Document number: DS39724  Rev. 2 - 2
15 of 18
www.diodes.com
June 2017
© Diodes Incorporated

AP2112

Package Outline Dimensions (All dimensions in mm.) (Previously identified as SOT-89-5 for this product)

SOT89-5

45
1.030(0.041)REF
1.550(0.061)REF
4.400(0.173)
4.600(0.181)
0.900(0.035)
1.100(0.043)
3.950(0.156)
4.250(0.167)
3.000(0.118)
TYP
0.480(0.019)
2.300(0.091)
2.600(0.102)
0.320(0.013)
3
10
2.060(0.081)REF
0.350(0.014)
0.450(0.018)
R0.150(0.006)
3
10
1.500(0.059)
0.320(0.013)REF
1.620(0.064)REF
2.210(0.087)REF
0.320(0.013)
1.800(0.071)
Option 1
1.100(0.043)
0.900(0.035)
TYP
0.540(0.021)
0.540(0.021)
Option 2
1.620(0.064)
1.830(0.072)
R 0.200(0.008)
2.630(0.104)
2.930(0.115)
0.950(0.037)
0.650(0.026)
0.650(0.026)
0.950(0.037)
0.500(0.020)
0.620(0.024)
1.400(0.055)
1.600(0.063)
Option 1

<!-- Page 16 -->

AP2112
Document number: DS39724  Rev. 2 - 2
16 of 18
www.diodes.com
June 2017
© Diodes Incorporated

AP2112

Suggested Pad Layout (Previously identified as SOT-89-5 for this product)

SOT89-5

X1
X2
Y1
E
Z
Y
X

Dimensions
Z
(mm)/(inch)
X
(mm)/(inch)
X1
(mm)/(inch)
X2
(mm)/(inch)
Y
(mm)/(inch)
Y1
(mm)/(inch)
E
(mm)/(inch)
Value
4.600/0.181
0.550/0.022
1.850/0.073
0.800/0.031
1.300/0.051
1.475/0.058
1.500/0.059

<!-- Page 17 -->

AP2112
Document number: DS39724  Rev. 2 - 2
17 of 18
www.diodes.com
June 2017
© Diodes Incorporated

AP2112

Package Outline Dimensions (Previously identified as SOIC-8 for this product)
Please see http://www.diodes.com/package-outlines.html for the latest version.

SO-8

SO-8
Dim
Min
Max
Typ
A
1.40
1.50
1.45
A1
0.10
0.20
0.15
b
0.30
0.50
0.40
c
0.15
0.25
0.20
D
4.85
4.95
4.90
E
5.90
6.10
6.00
E1
3.80
3.90
3.85
E0
3.85
3.95
3.90
e
--
--
1.27
h
-
--
0.35
L
0.62
0.82
0.72
Q
0.60
0.70
0.65
All Dimensions in mm

Suggested Pad Layout
Please see http://www.diodes.com/package-outlines.html for the latest version.

SO-8

Note:
The suggested land pattern dimensions have been provided for reference only, as actual pad layouts may vary depending on application. These
dimensions may be modified based on user equipment capability or fabrication criteria. A more robust pattern may be desired for wave soldering
and is calculated by adding 0.2 mm to the ‗Z‘ dimension. For further information, please reference document IPC-7351A, Naming Convention for
Standard SMT Land Patterns, and for International grid details, please see document IEC, Publication 97.

Note:
For high voltage applications, the appropriate industry sector guidelines should be considered with regards to creepage and clearance distances
between device Terminals and PCB tracking.

1
b
e
E
A
A1
9° (All sides)
4°± 3°
c
Q
h
45°
R 0.1
7°
D
E0
E1
L
Seating Plane
Gauge Plane
Dimensions Value (in mm)
C
1.27
X
0.802
X1
4.612
Y
1.505
Y1
6.50
C
X
Y
Y1
X1

<!-- Page 18 -->

AP2112
Document number: DS39724  Rev. 2 - 2
18 of 18
www.diodes.com
June 2017
© Diodes Incorporated

AP2112

IMPORTANT NOTICE

DIODES INCORPORATED MAKES NO WARRANTY OF ANY KIND, EXPRESS OR IMPLIED, WITH REGARDS TO THIS DOCUMENT,
INCLUDING, BUT NOT LIMITED TO, THE IMPLIED WARRANTIES OF MERCHANTABILITY AND FITNESS FOR A PARTICULAR PURPOSE
(AND THEIR EQUIVALENTS UNDER THE LAWS OF ANY JURISDICTION).

Diodes Incorporated and its subsidiaries reserve the right to make modifications, enhancements, improvements, corrections or other changes
without further notice to this document and any product described herein. Diodes Incorporated does not assume any liability arising out of the
application or use of this document or any product described herein; neither does Diodes Incorporated convey any license under its patent or
trademark rights, nor the rights of others.  Any Customer or user of this document or products described herein in such applications shall assume
all risks of such use and will agree to hold Diodes Incorporated and all the companies whose products are represented on Diodes Incorporated
website, harmless against all damages.

Diodes Incorporated does not warrant or accept any liability whatsoever in respect of any products purchased through unauthorized sales channel.
Should Customers purchase or use Diodes Incorporated products for any unintended or unauthorized application, Customers shall indemnify and
hold Diodes Incorporated and its representatives harmless against all claims, damages, expenses, and attorney fees arising out of, directly or
indirectly, any claim of personal injury or death associated with such unintended or unauthorized application.

Products described herein may be covered by one or more United States, international or foreign patents pending.  Product names and markings
noted herein may also be covered by one or more United States, international or foreign trademarks.

This document is written in English but may be translated into multiple languages for reference.  Only the English version of this document is the
final and determinative format released by Diodes Incorporated.

LIFE SUPPORT

Diodes Incorporated products are specifically not authorized for use as critical components in life support devices or systems without the express
written approval of the Chief Executive Officer of Diodes Incorporated. As used herein:

A.   Life support devices or systems are devices or systems which:

1. are intended to implant into the body, or

2. support or sustain life and whose failure to perform when properly used in accordance with instructions for use provided in the

     labeling can be reasonably expected to result in significant injury to the user.

B.   A critical component is any component in a life support device or system whose failure to perform can be reasonably expected to cause the
      failure of the life support device or to affect its safety or effectiveness.

Customers represent that they have all necessary expertise in the safety and regulatory ramifications of their life support devices or systems, and
acknowledge and agree that they are solely responsible for all legal, regulatory and safety-related requirements concerning their products and any
use of Diodes Incorporated products in such safety-critical, life support devices or systems, notwithstanding any devices- or systems-related
information or support that may be provided by Diodes Incorporated.  Further, Customers must fully indemnify Diodes Incorporated and its
representatives against any damages arising out of the use of Diodes Incorporated products in such safety-critical, life support devices or systems.

Copyright © 2017, Diodes Incorporated

www.diodes.com

---
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
